phiphi33/block/docs/IMG_20210426_165738.jpg

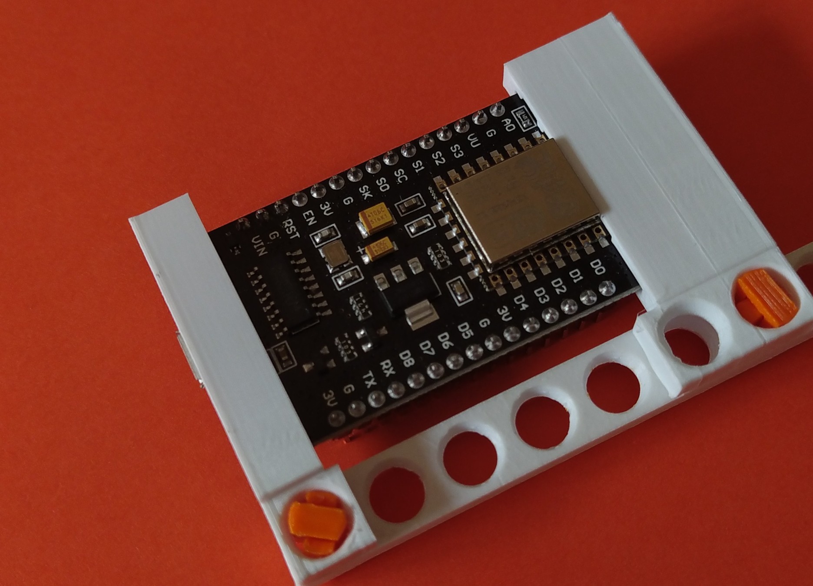
docs/IMG_20210426_165738.jpg
