phiphi33/block/docs/list-elec-csv.png

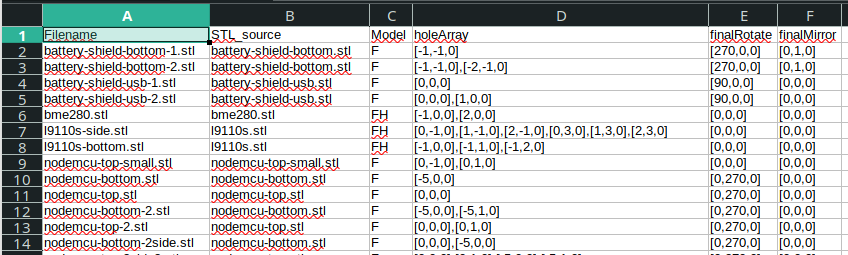
docs/list-elec-csv.png
