phiphi33/block/docs/projects/smartphone-holder.jpg

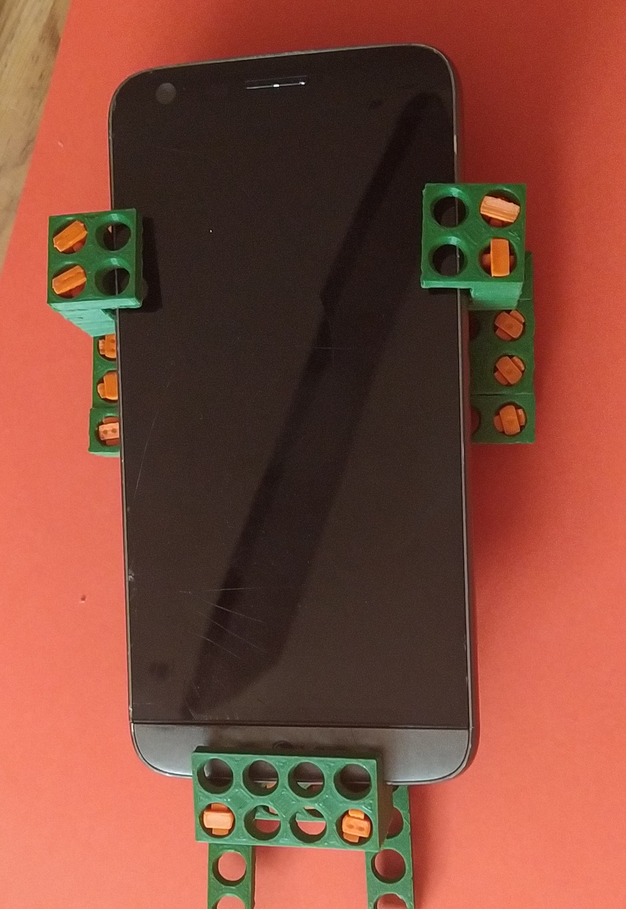
docs/projects/smartphone-holder.jpg
