phiphi33/block/other/12.8/stl/clips/blocker-2.png

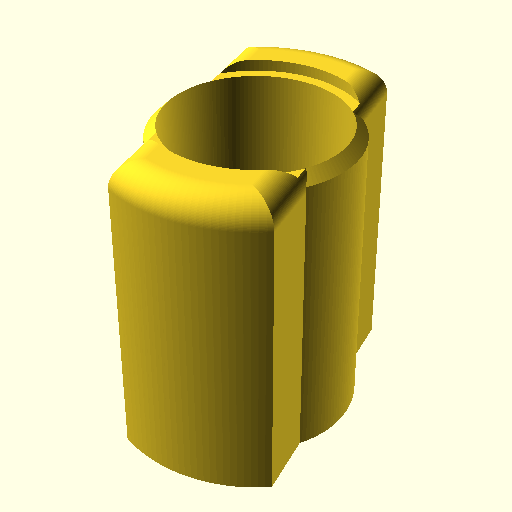
other/12.8/stl/clips/blocker-2.png
