phiphi33/block/other/12.8/stl/clips/clip-2.png

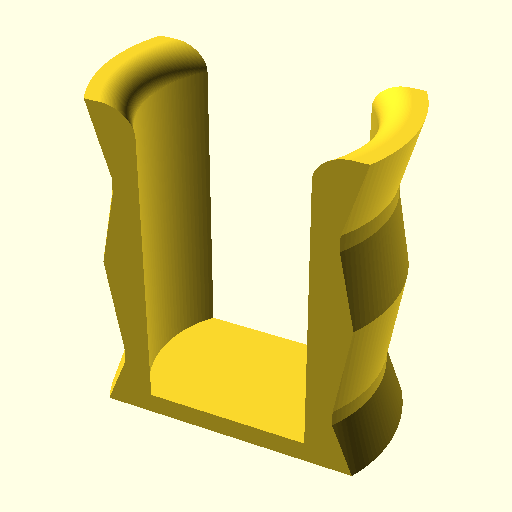
other/12.8/stl/clips/clip-2.png
