phiphi33/block/other/lego/stl/L1.png

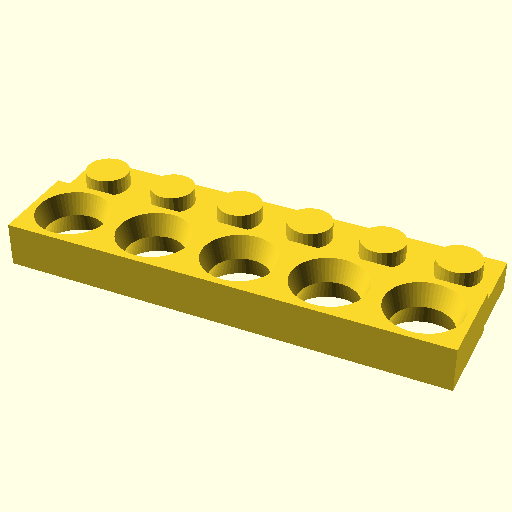
other/lego/stl/L1.png
