phiphi33/block/other/lego/stl/L2.png

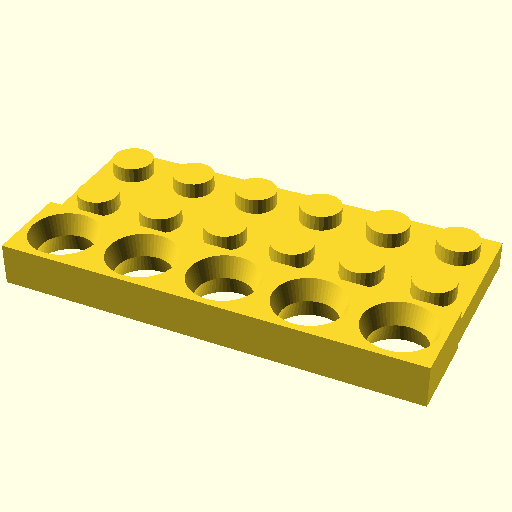
other/lego/stl/L2.png
