phiphi33/block/other/lego/stl/L3.png

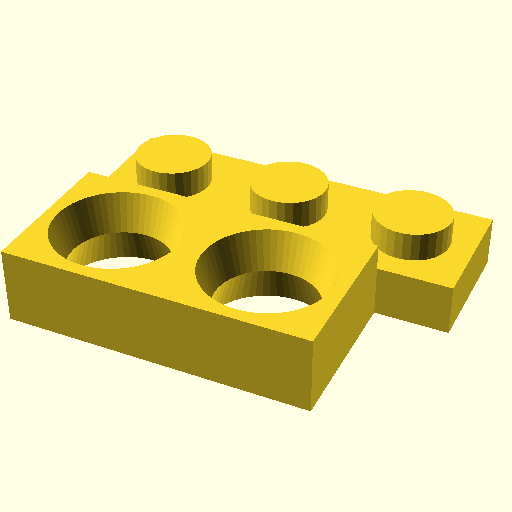
other/lego/stl/L3.png
