phiphi33/block/other/lego/stl/L4.png

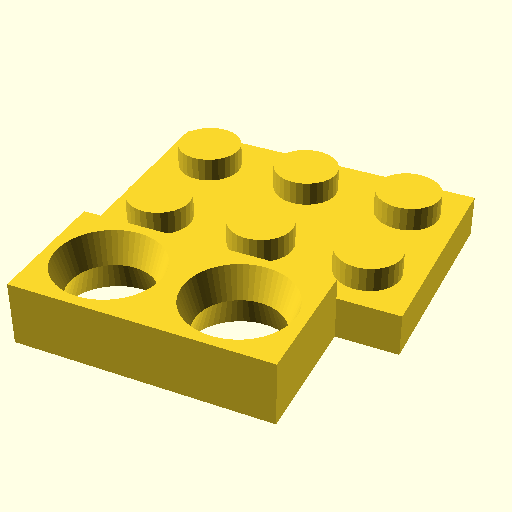
other/lego/stl/L4.png
