phiphi33/block/other/lego/stl/L5.png

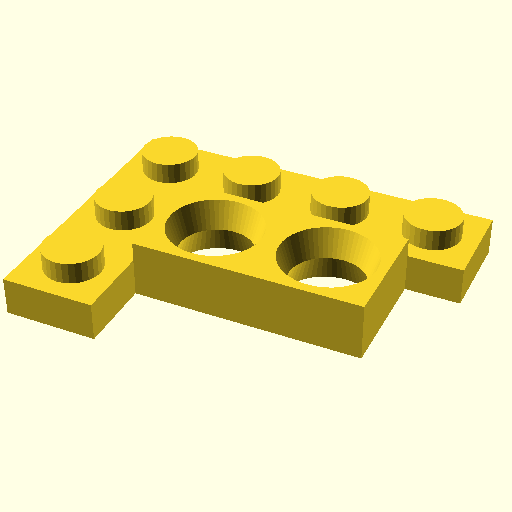
other/lego/stl/L5.png
