phiphi33/block/other/lego/stl/L6.png

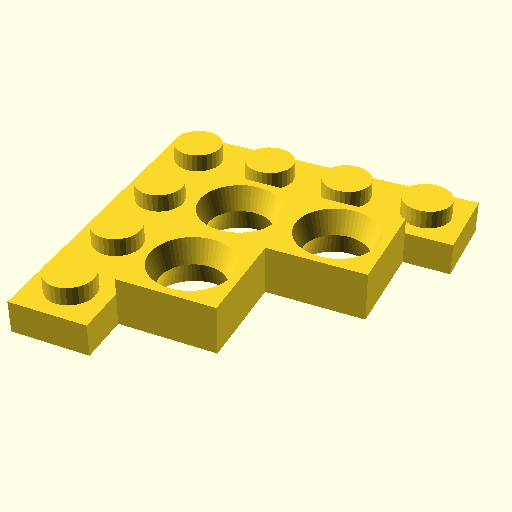
other/lego/stl/L6.png
