phiphi33/block/other/lego/stl/L7.png

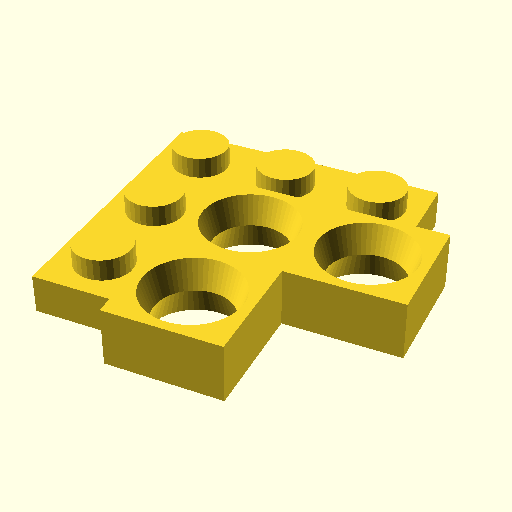
other/lego/stl/L7.png
