phiphi33/block/other/spiralwheel/stl/SP45-hard-clip.png

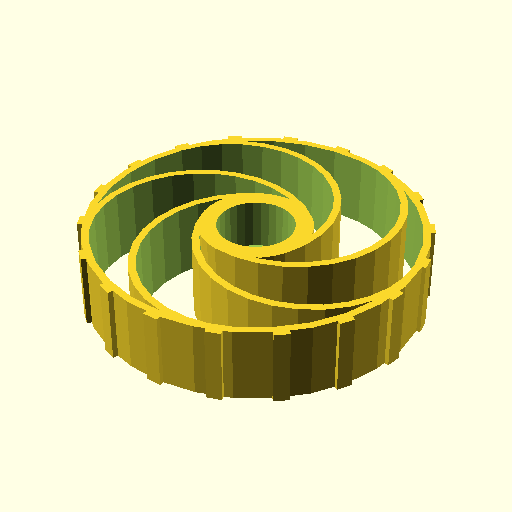
other/spiralwheel/stl/SP45-hard-clip.png
