phiphi33/block/other/spiralwheel/stl/SP45-hard-dc-gearbox.png

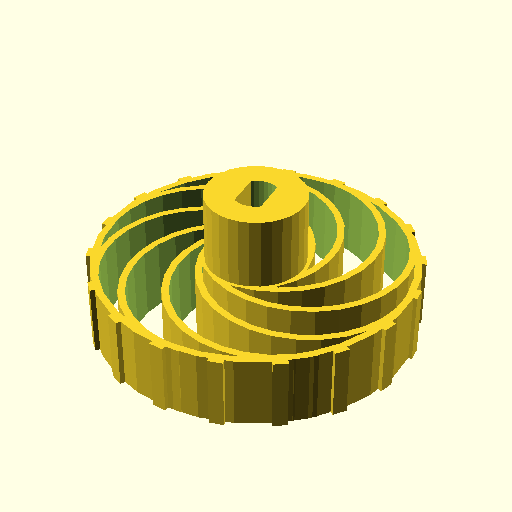
other/spiralwheel/stl/SP45-hard-dc-gearbox.png
