phiphi33/block/other/spiralwheel/stl/SP45-soft-sg90.png

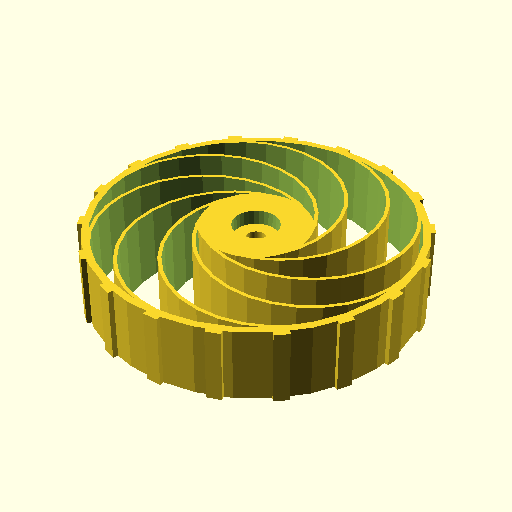
other/spiralwheel/stl/SP45-soft-sg90.png
