phiphi33/block/other/spiralwheel/stl/SP65-soft-clip.png

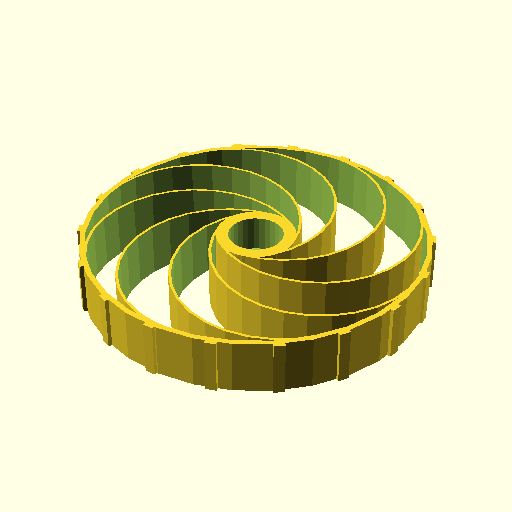
other/spiralwheel/stl/SP65-soft-clip.png
