phiphi33/block/other/spiralwheel/stl/washer.png

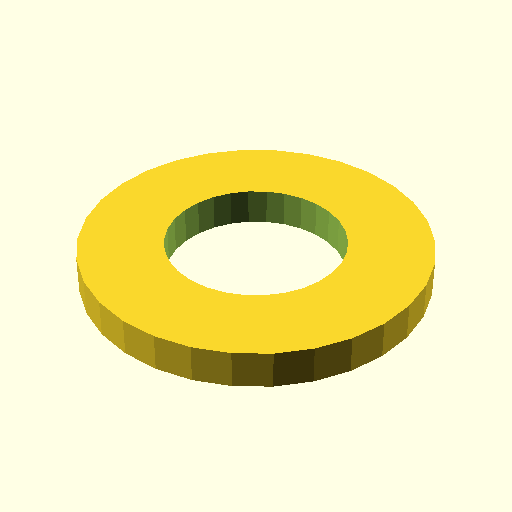
other/spiralwheel/stl/washer.png
