phiphi33/block/stl/clips/blocker-2-easy2.png

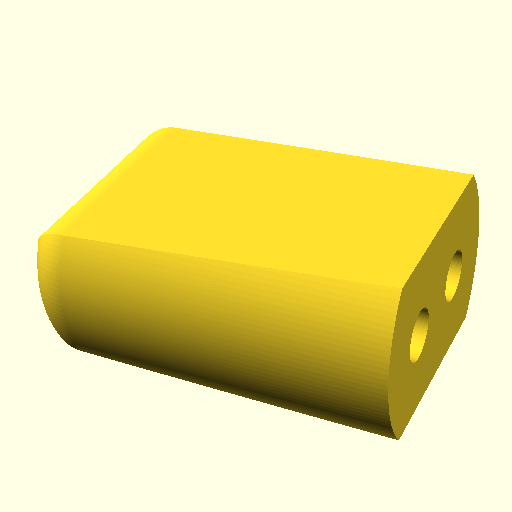
stl/clips/blocker-2-easy2.png
