phiphi33/block/stl/clips/blocker-2-easy.png

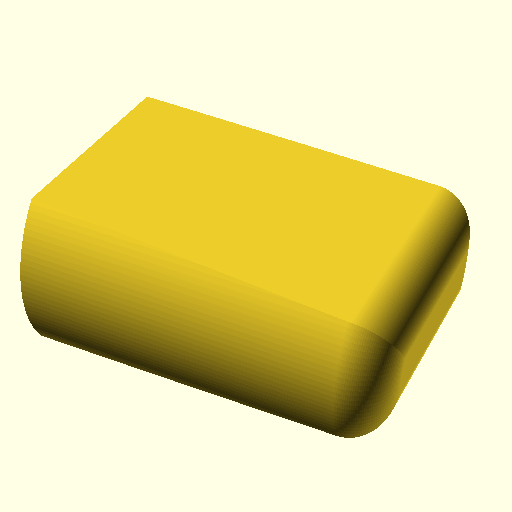
stl/clips/blocker-2-easy.png
