phiphi33/block/stl/clips/blocker-2-strong.png

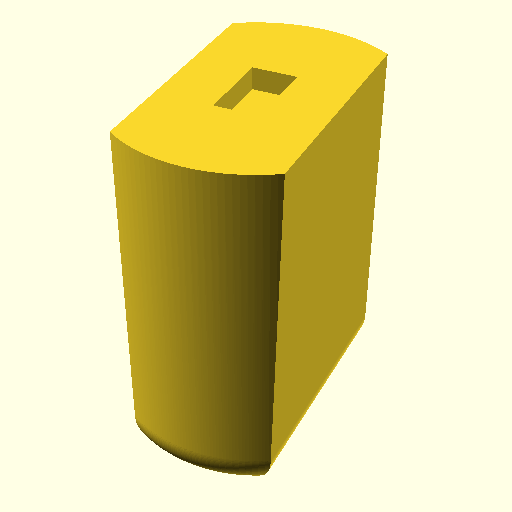
stl/clips/blocker-2-strong.png
