phiphi33/block/stl/clips/blocker-2.png

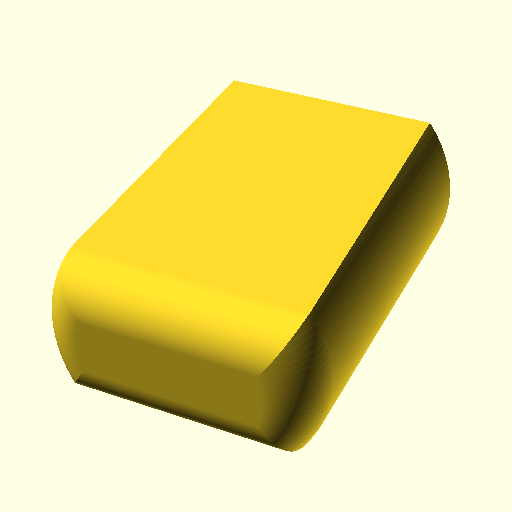
stl/clips/blocker-2.png
