phiphi33/block/stl/clips/blocker-3-easy2.png

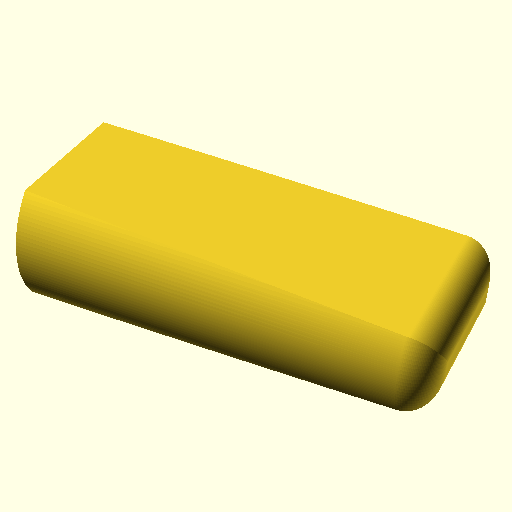
stl/clips/blocker-3-easy2.png
