phiphi33/block/stl/clips/blocker-3-strong.png

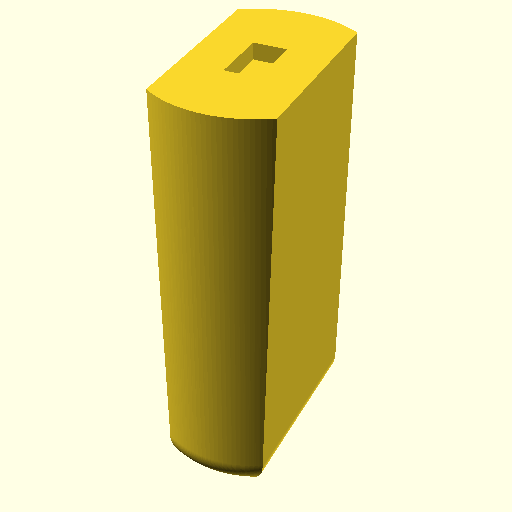
stl/clips/blocker-3-strong.png
