phiphi33/block/stl/clips/blocker-3.png

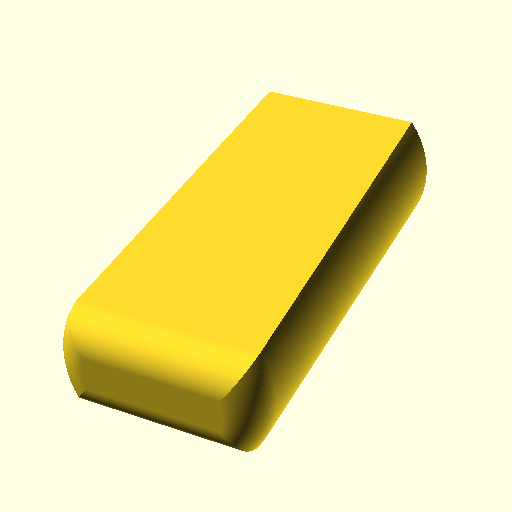
stl/clips/blocker-3.png
