phiphi33/block/stl/clips/blocker-4-easy2.png

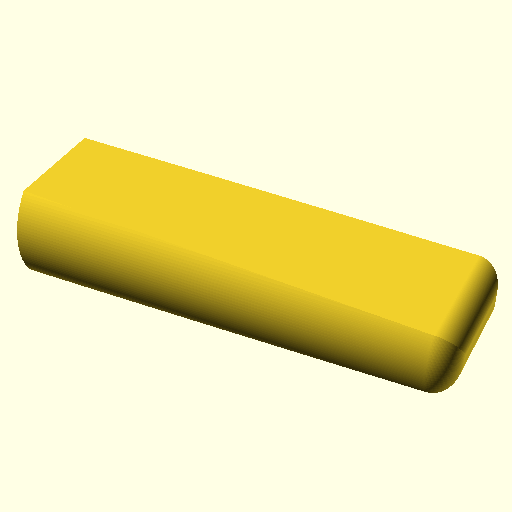
stl/clips/blocker-4-easy2.png
