phiphi33/block/stl/clips/blocker-4-strong.png

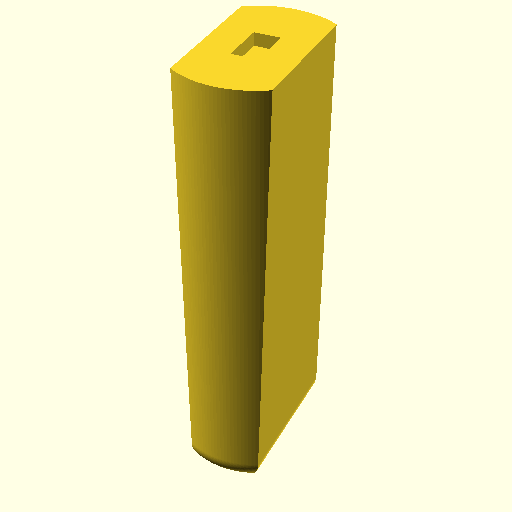
stl/clips/blocker-4-strong.png
