phiphi33/block/stl/clips/blocker-4.png

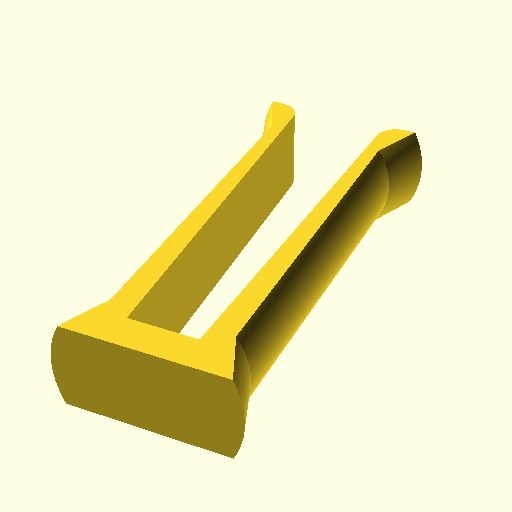
stl/clips/blocker-4.png
