phiphi33/block/stl/clips/blocker-5.png

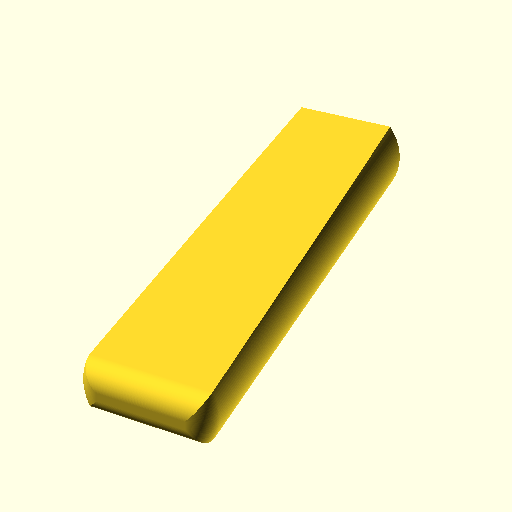
stl/clips/blocker-5.png
