phiphi33/block/stl/clips/clip-2-M4.png

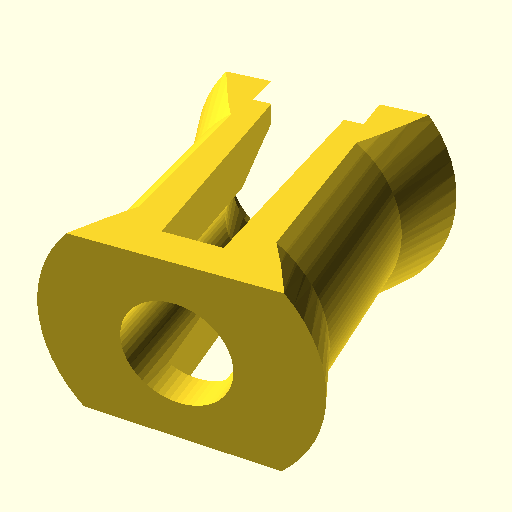
stl/clips/clip-2-M4.png
