phiphi33/block/stl/clips/clip-2.png

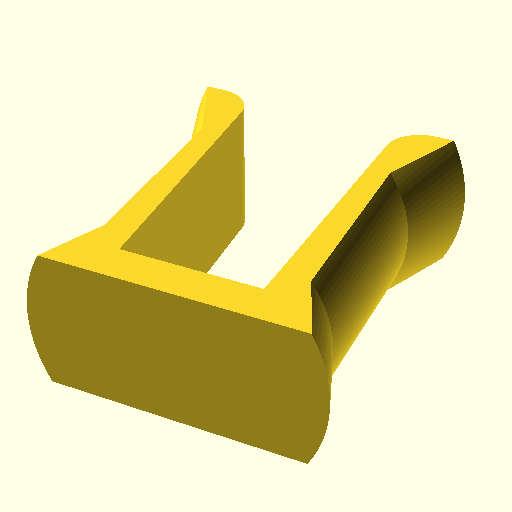
stl/clips/clip-2.png
