phiphi33/block/stl/clips/clip-3-M4.png

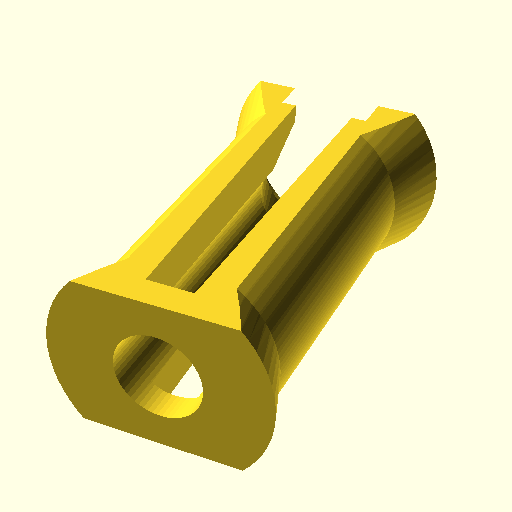
stl/clips/clip-3-M4.png
