phiphi33/block/stl/clips/clip-3.png

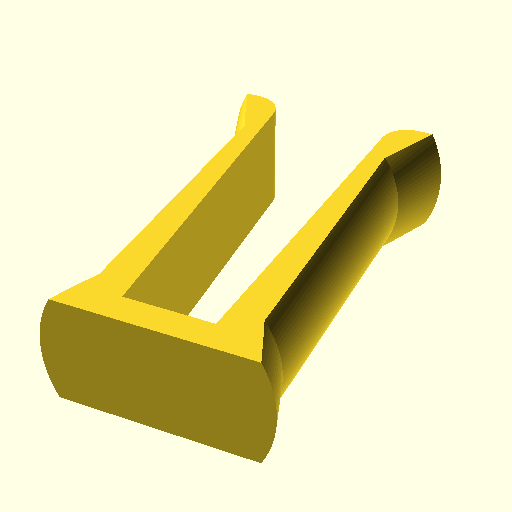
stl/clips/clip-3.png
