phiphi33/block/stl/clips/clip-3a.png

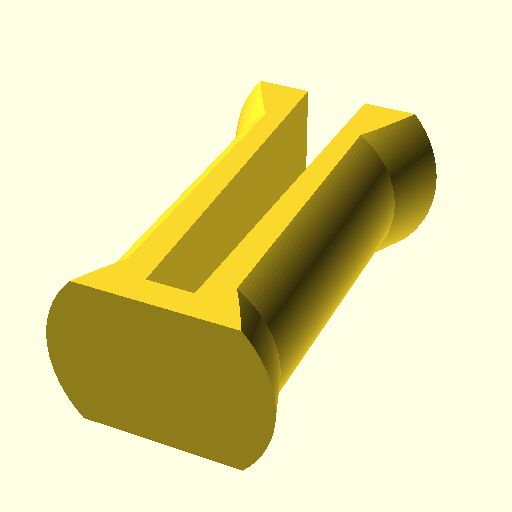
stl/clips/clip-3a.png
