phiphi33/block/stl/clips/clip-4-M4.png

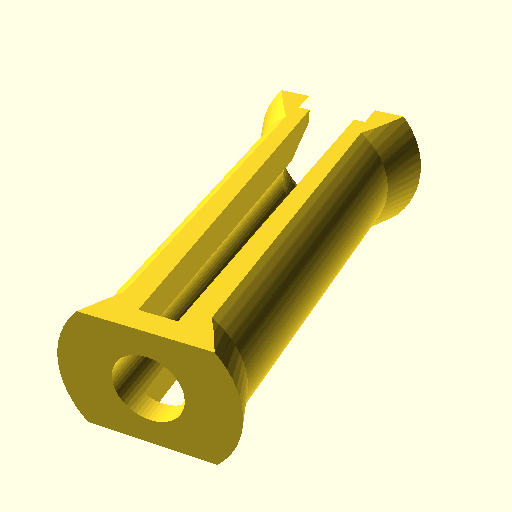
stl/clips/clip-4-M4.png
