phiphi33/block/stl/clips/clip-5.png

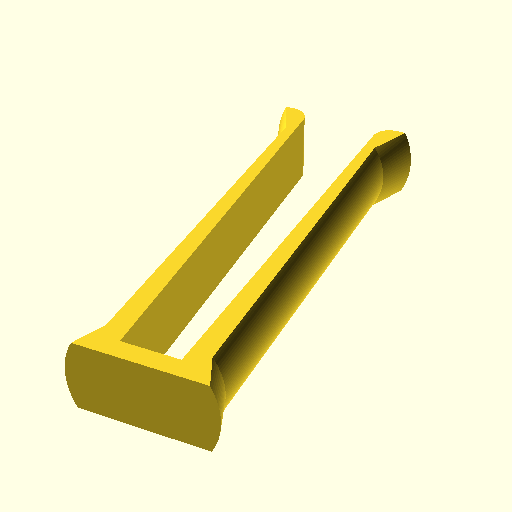
stl/clips/clip-5.png
