phiphi33/block/stl/clips/clip-6.png

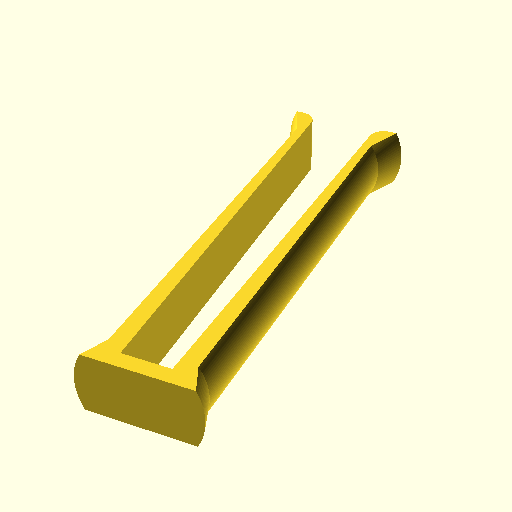
stl/clips/clip-6.png
