phiphi33/block/other/12.8/stl/basic-parts/C-2-1-1.png

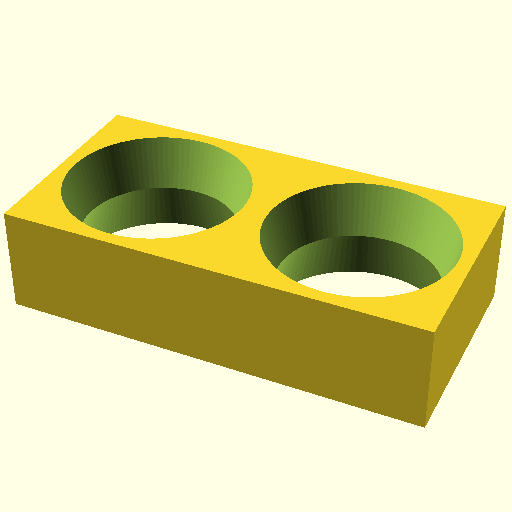
other/12.8/stl/basic-parts/C-2-1-1.png
