phiphi33/block/stl/basic-parts/C-2-2-1.png

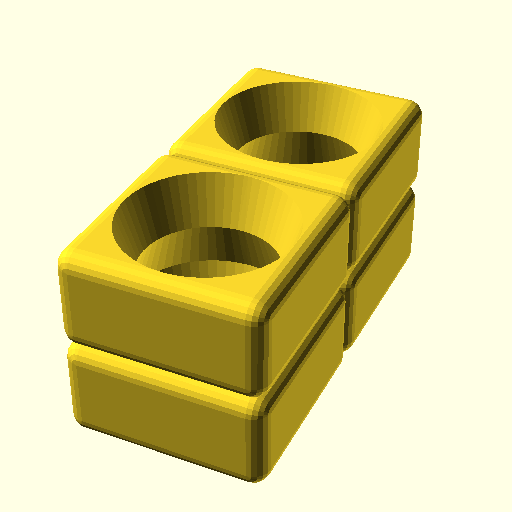
stl/basic-parts/C-2-2-1.png
