phiphi33/block/stl/basic-parts/C-2-2-2.png

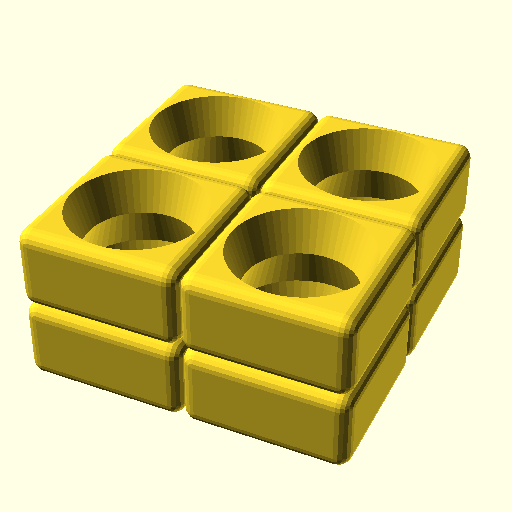
stl/basic-parts/C-2-2-2.png
