phiphi33/block/stl/basic-parts/C-3-1-1.png

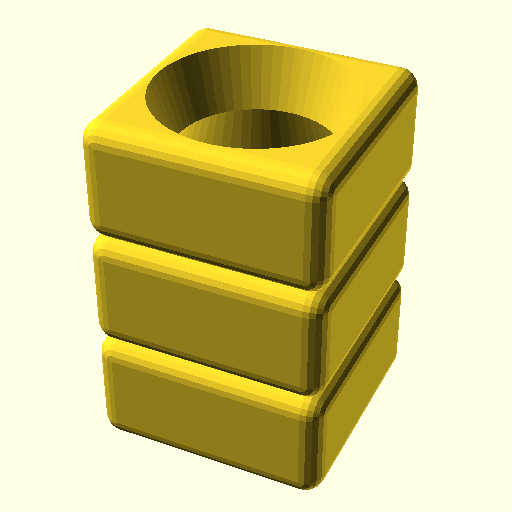
stl/basic-parts/C-3-1-1.png
