phiphi33/block/stl/basic-parts/I-1.png

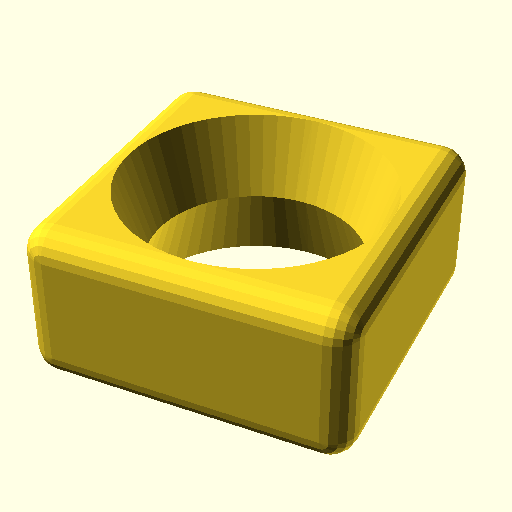
stl/basic-parts/I-1.png
