phiphi33/block/stl/basic-parts/I-2.png

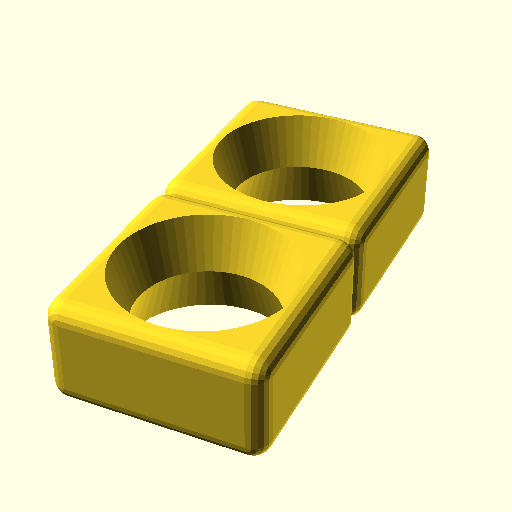
stl/basic-parts/I-2.png
