phiphi33/block/stl/basic-parts/I-3.png

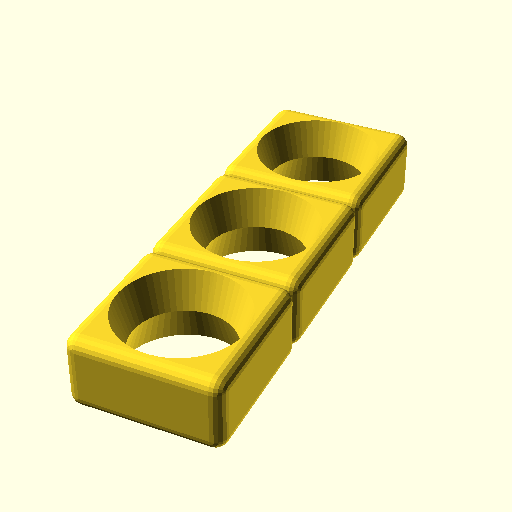
stl/basic-parts/I-3.png
