phiphi33/block/stl/basic-parts/I-4.png

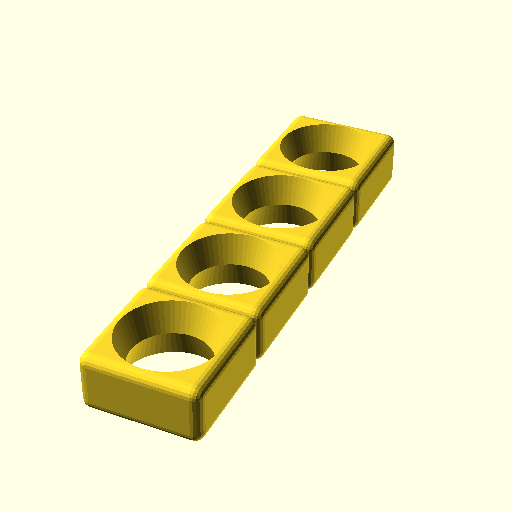
stl/basic-parts/I-4.png
