phiphi33/block/stl/basic-parts/I-7.png

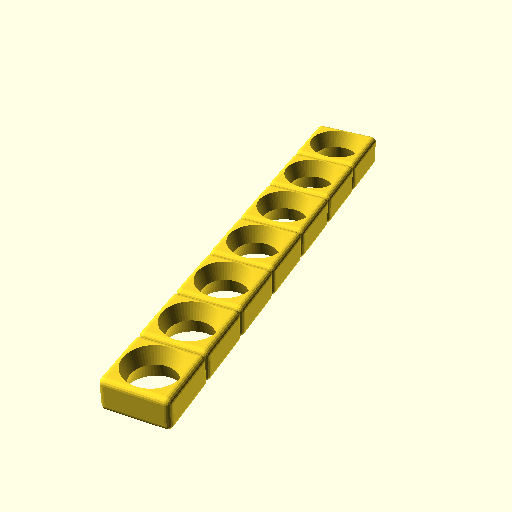
stl/basic-parts/I-7.png
