phiphi33/block/stl/basic-parts/IHR-2.png

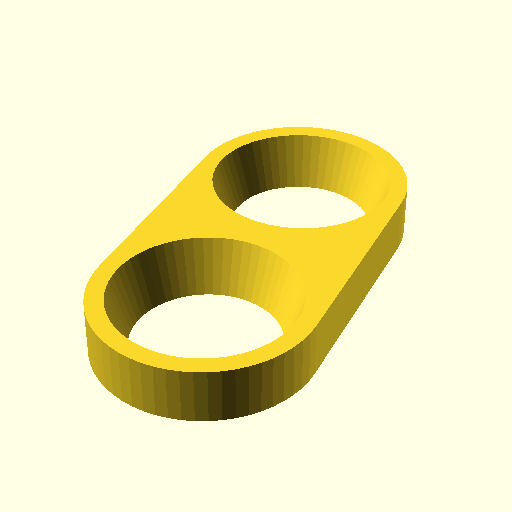
stl/basic-parts/IHR-2.png
