phiphi33/block/stl/basic-parts/IR-1.png

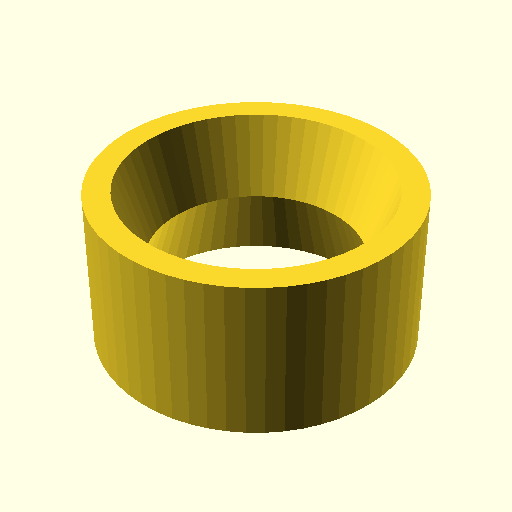
stl/basic-parts/IR-1.png
