phiphi33/block/stl/basic-parts/IR-2.png

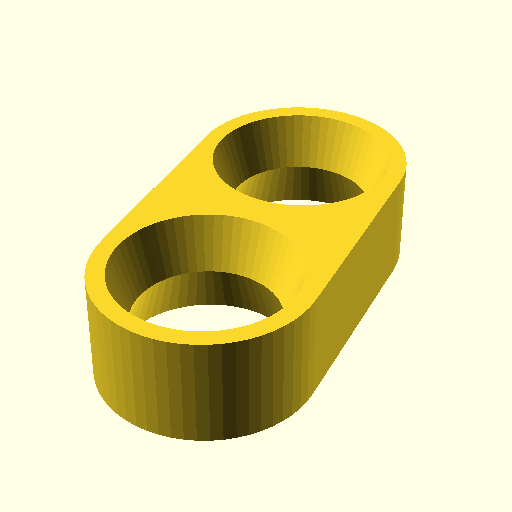
stl/basic-parts/IR-2.png
