phiphi33/block/stl/basic-parts/IR-3.png

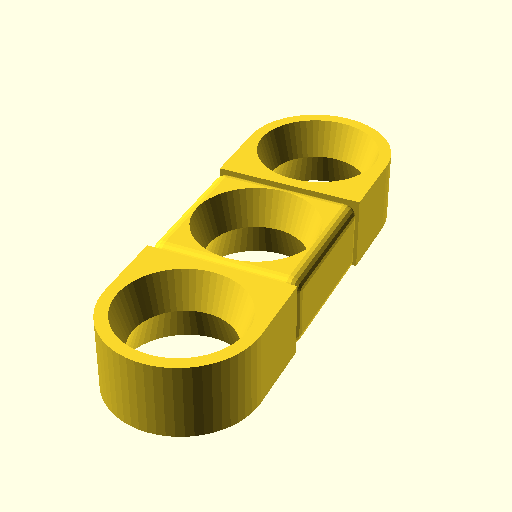
stl/basic-parts/IR-3.png
