phiphi33/block/stl/basic-parts/L-1-1-3.png

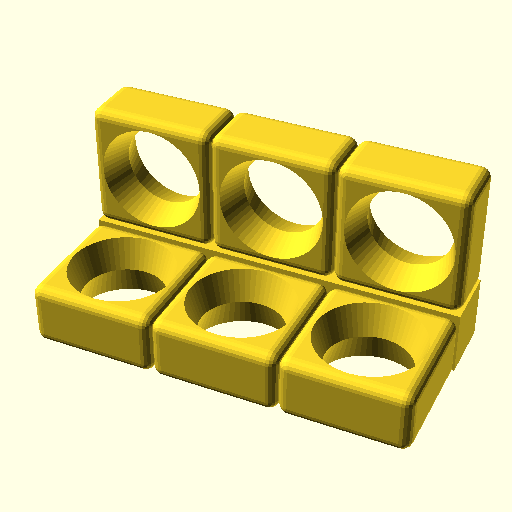
stl/basic-parts/L-1-1-3.png
