phiphi33/block/stl/basic-parts/L-1-1-4.png

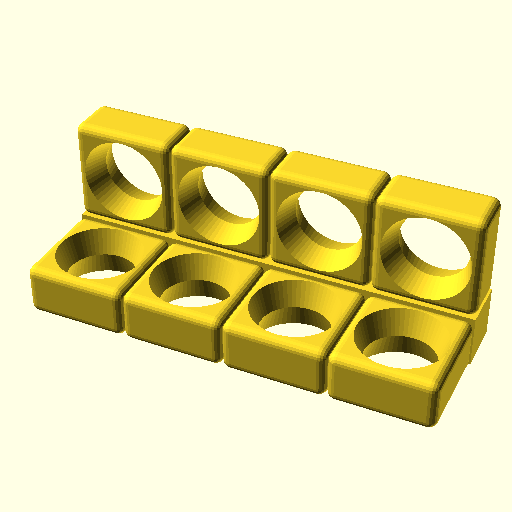
stl/basic-parts/L-1-1-4.png
