phiphi33/block/stl/basic-parts/L-1-1-8.png

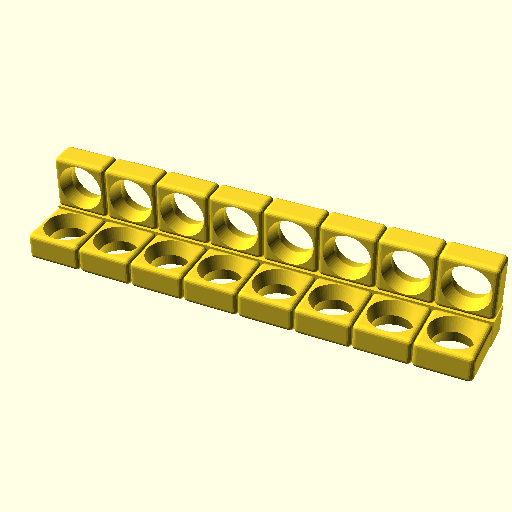
stl/basic-parts/L-1-1-8.png
