phiphi33/block/stl/basic-parts/L-2-1-2.png

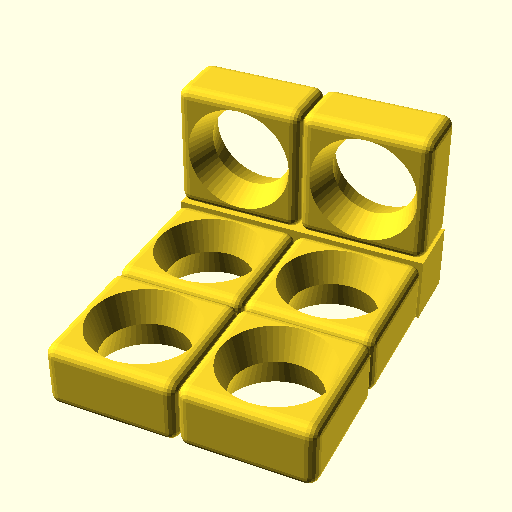
stl/basic-parts/L-2-1-2.png
