phiphi33/block/stl/basic-parts/L-2-1-5.png

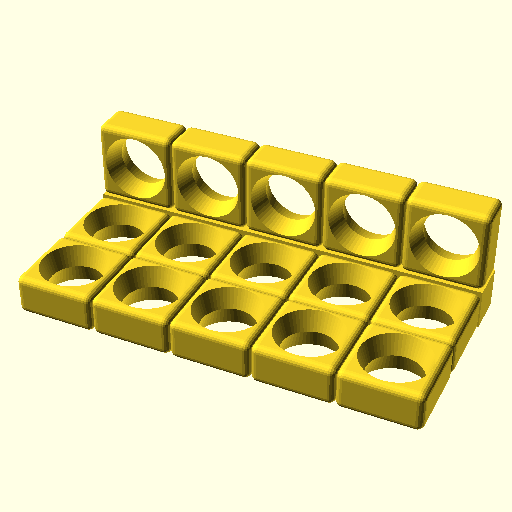
stl/basic-parts/L-2-1-5.png
