phiphi33/block/stl/basic-parts/L-2-2-1.png

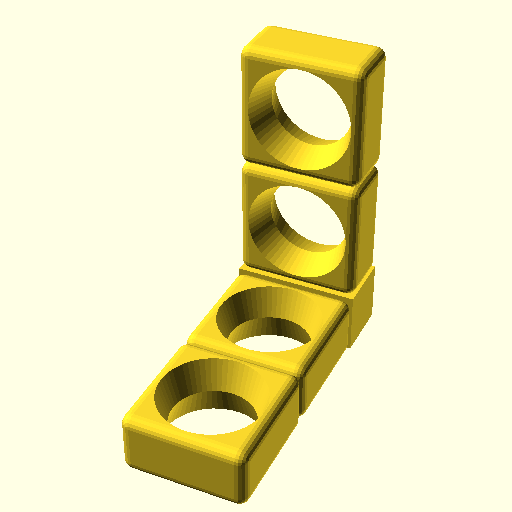
stl/basic-parts/L-2-2-1.png
