phiphi33/block/stl/basic-parts/L-2-2-3.png

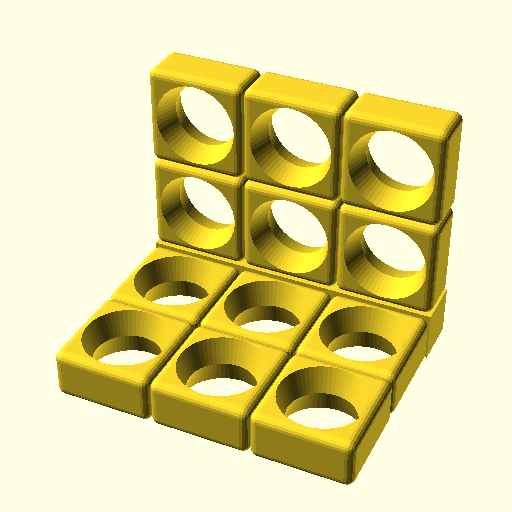
stl/basic-parts/L-2-2-3.png
