phiphi33/block/stl/basic-parts/L-3-1-1.png

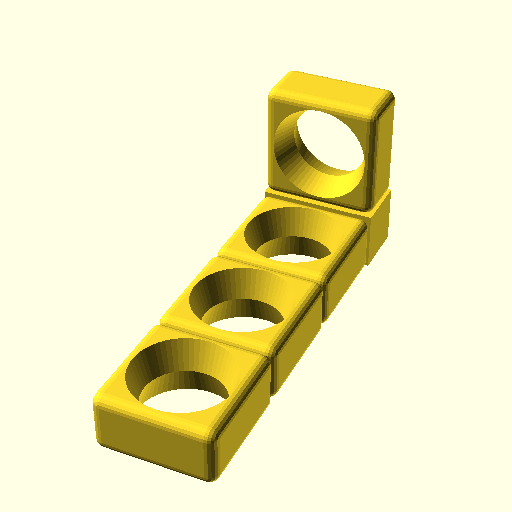
stl/basic-parts/L-3-1-1.png
