phiphi33/block/stl/basic-parts/L-3-3-3.png

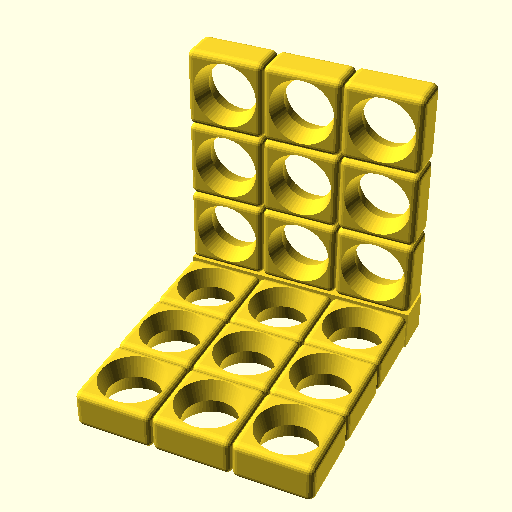
stl/basic-parts/L-3-3-3.png
