phiphi33/block/stl/basic-parts/L-4-1-1.png

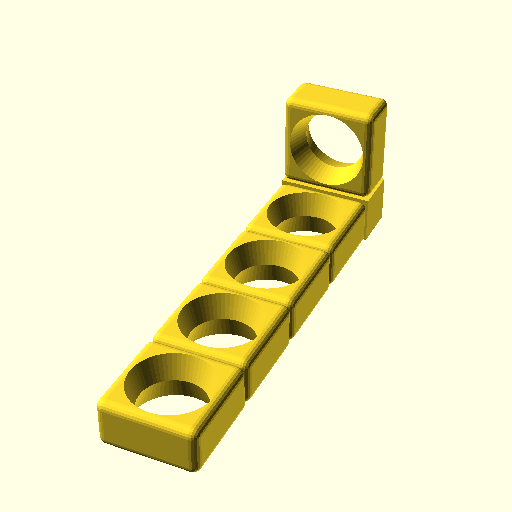
stl/basic-parts/L-4-1-1.png
