phiphi33/block/stl/basic-parts/L-6-1-1.png

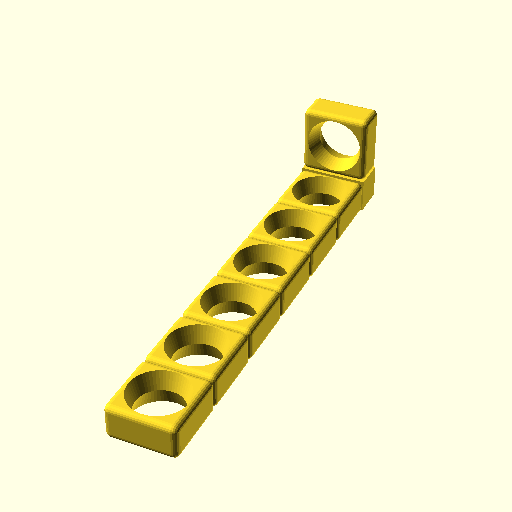
stl/basic-parts/L-6-1-1.png
