phiphi33/block/stl/basic-parts/LF-2-2.png

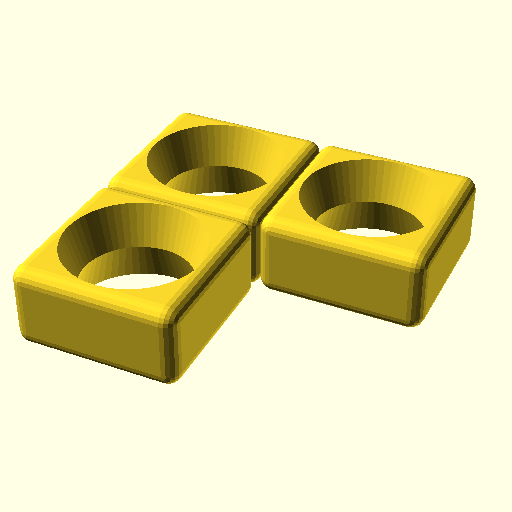
stl/basic-parts/LF-2-2.png
