phiphi33/block/stl/basic-parts/LF-3-2.png

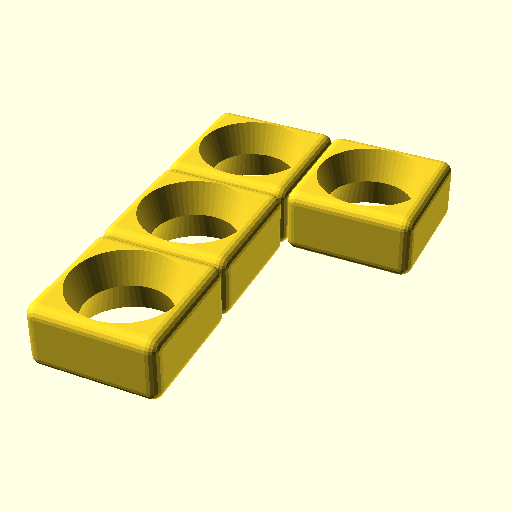
stl/basic-parts/LF-3-2.png
