phiphi33/block/stl/basic-parts/LF-3-3.png

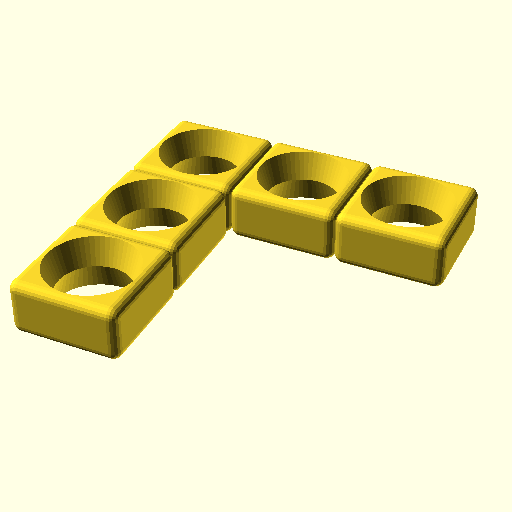
stl/basic-parts/LF-3-3.png
