phiphi33/block/stl/basic-parts/LF-4-2.png

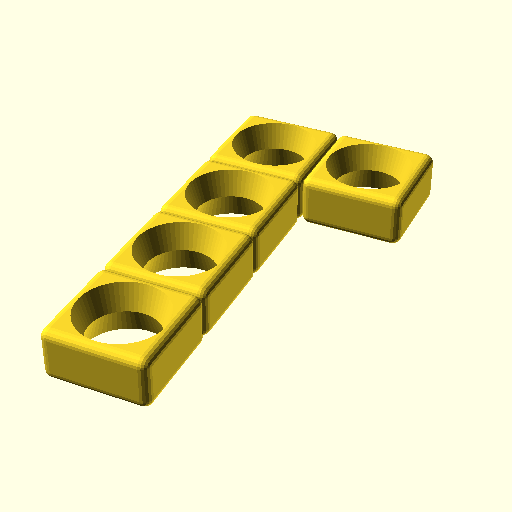
stl/basic-parts/LF-4-2.png
