phiphi33/block/stl/basic-parts/LF-4-3.png

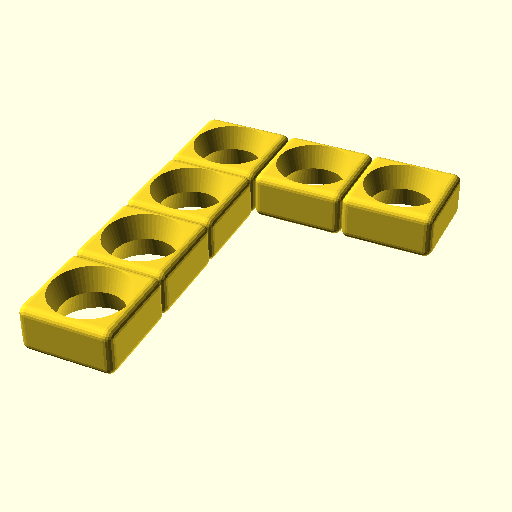
stl/basic-parts/LF-4-3.png
