phiphi33/block/stl/basic-parts/LF-4-4.png

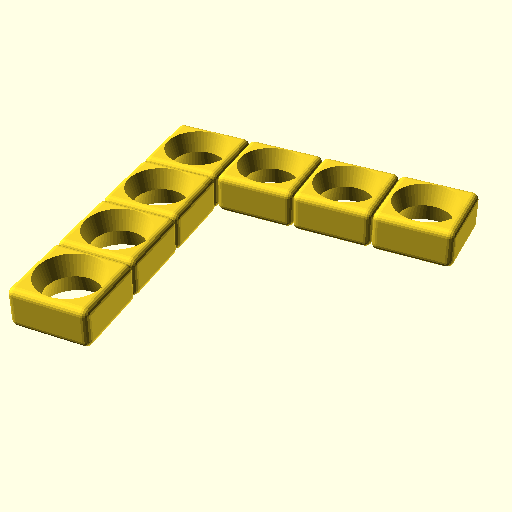
stl/basic-parts/LF-4-4.png
