phiphi33/block/stl/basic-parts/LF-6-2.png

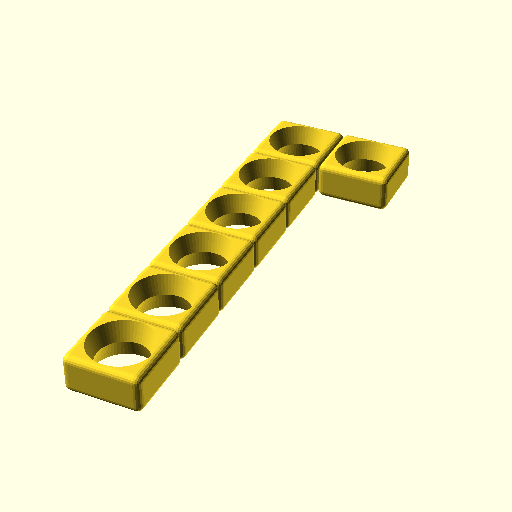
stl/basic-parts/LF-6-2.png
