phiphi33/block/stl/basic-parts/LF-6-3.png

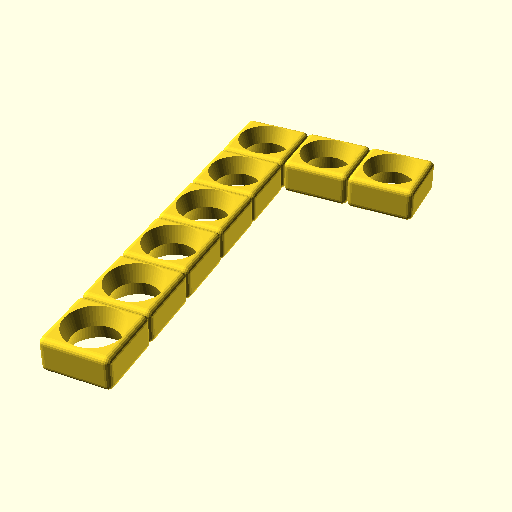
stl/basic-parts/LF-6-3.png
