phiphi33/block/stl/basic-parts/P-2-2.png

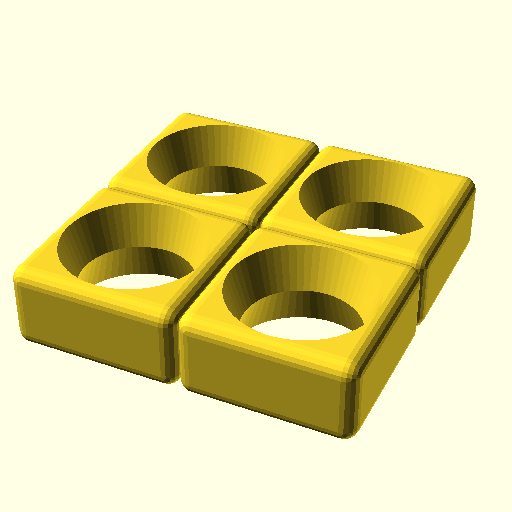
stl/basic-parts/P-2-2.png
