phiphi33/block/stl/basic-parts/P-3-2.png

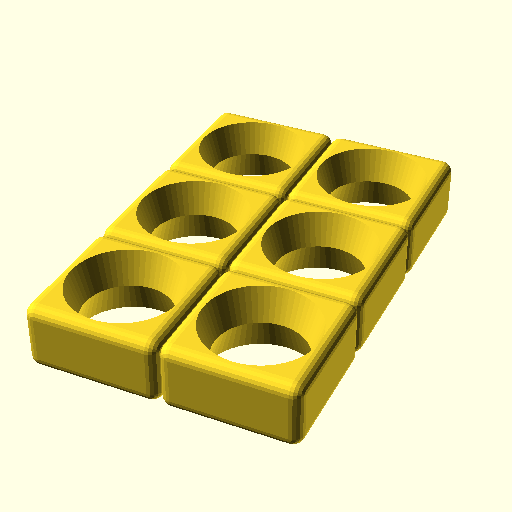
stl/basic-parts/P-3-2.png
