phiphi33/block/stl/basic-parts/P-3-3.png

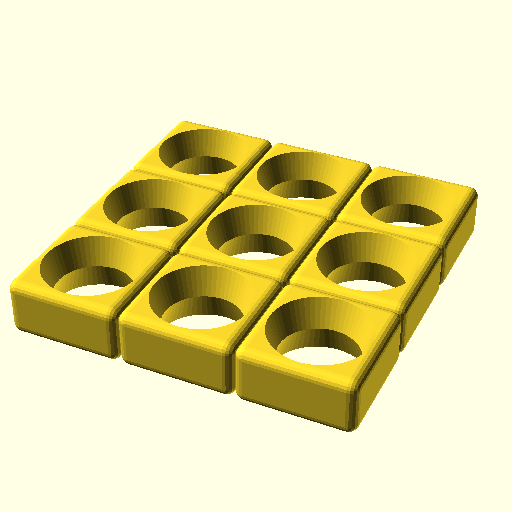
stl/basic-parts/P-3-3.png
