phiphi33/block/stl/basic-parts/P-4-2.png

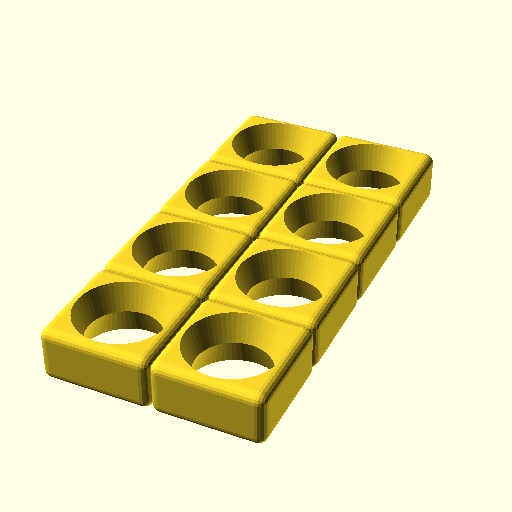
stl/basic-parts/P-4-2.png
