phiphi33/block/stl/basic-parts/P-4-4.png

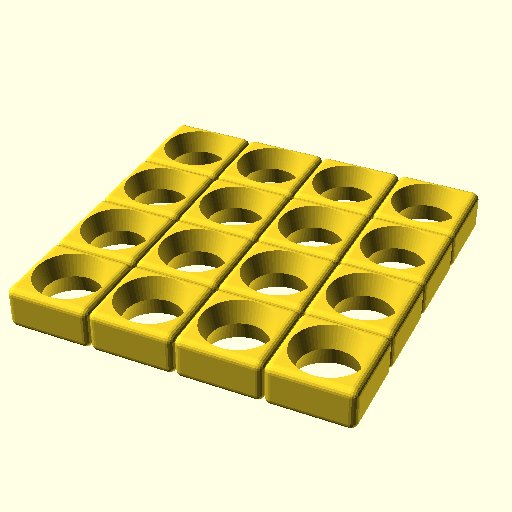
stl/basic-parts/P-4-4.png
