phiphi33/block/stl/basic-parts/P-5-2.png

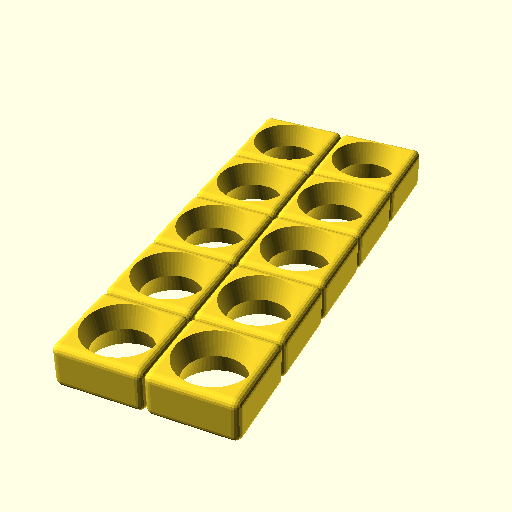
stl/basic-parts/P-5-2.png
