phiphi33/block/stl/basic-parts/P-5-4.png

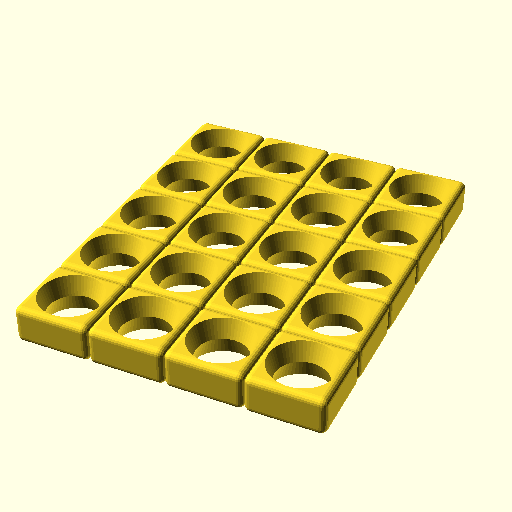
stl/basic-parts/P-5-4.png
