phiphi33/block/stl/basic-parts/P-6-2.png

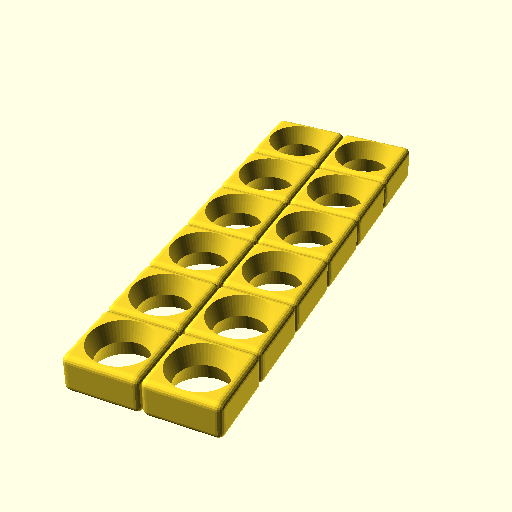
stl/basic-parts/P-6-2.png
