phiphi33/block/stl/basic-parts/S-1-1-1.png

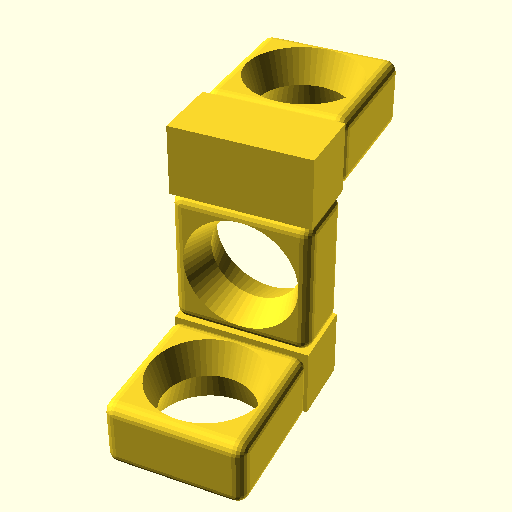
stl/basic-parts/S-1-1-1.png
