phiphi33/block/stl/basic-parts/S-2-1-2.png

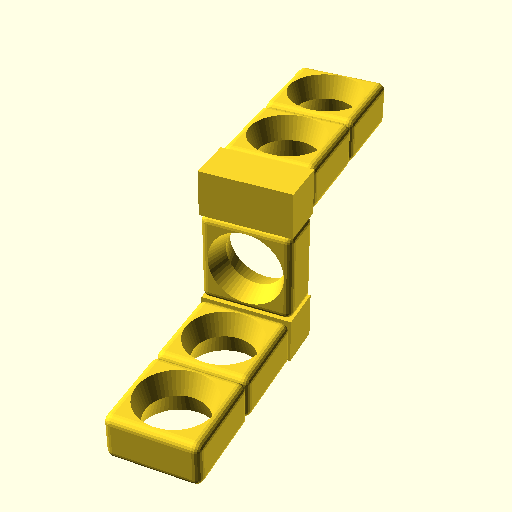
stl/basic-parts/S-2-1-2.png
