phiphi33/block/stl/basic-parts/U-1-2-1.png

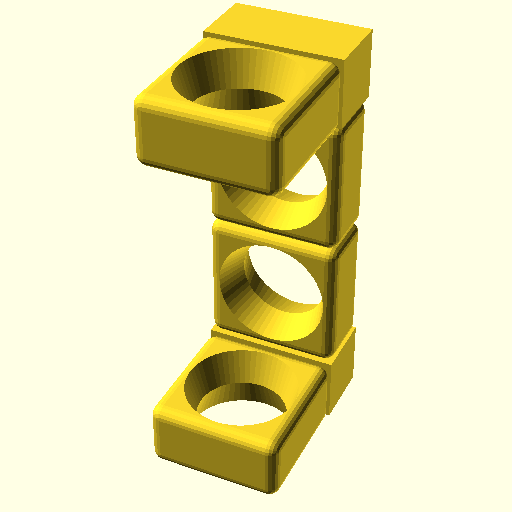
stl/basic-parts/U-1-2-1.png
