phiphi33/block/stl/basic-parts/U-2-2-2.png

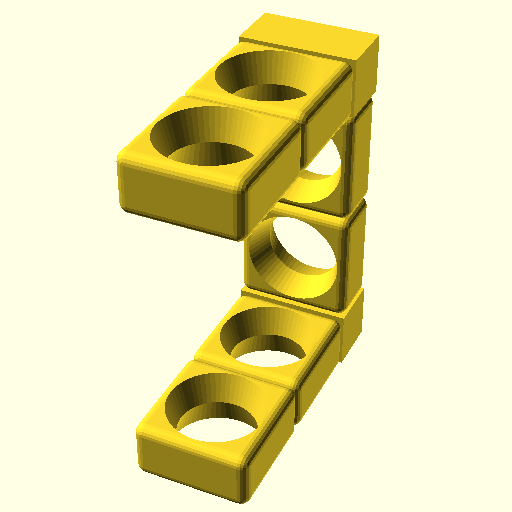
stl/basic-parts/U-2-2-2.png
