phiphi33/block/stl/basic-parts/U-3-3-3.png

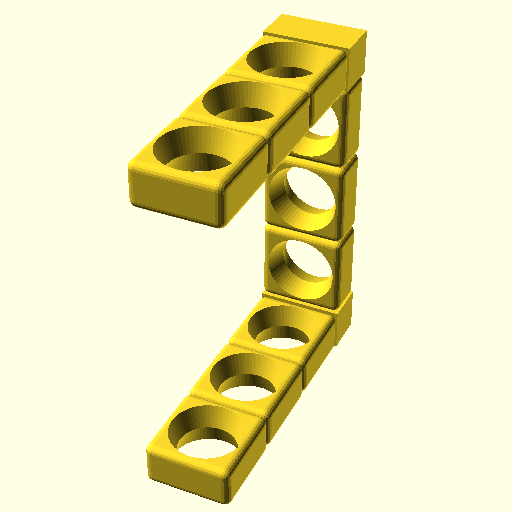
stl/basic-parts/U-3-3-3.png
