phiphi33/block/stl/electronic-parts/18650x2/18650x2-holder-bottom.png

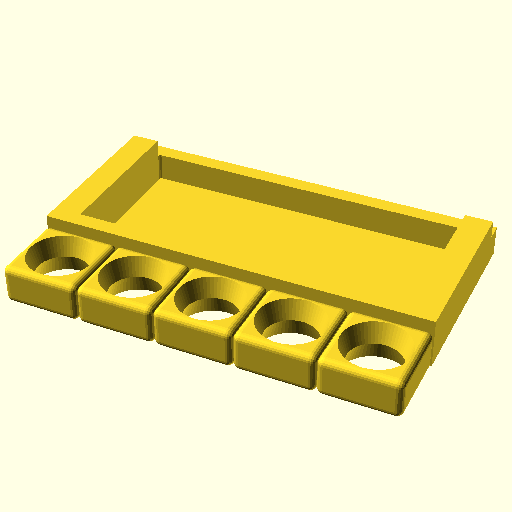
stl/electronic-parts/18650x2/18650x2-holder-bottom.png
