phiphi33/block/stl/electronic-parts/arduino-nano/nano-bottom-2side.png

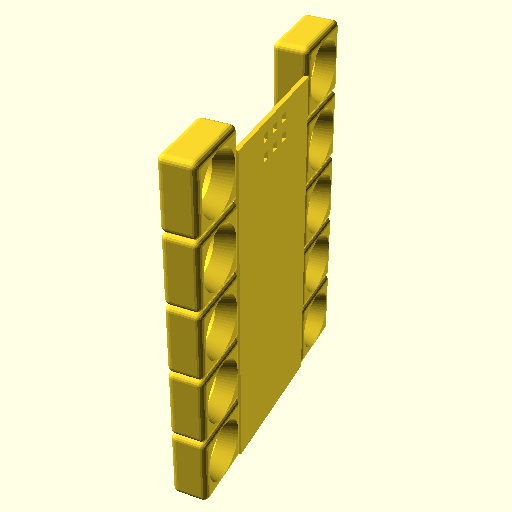
stl/electronic-parts/arduino-nano/nano-bottom-2side.png
