phiphi33/block/stl/electronic-parts/battery-shield/battery-shield-bottom-1.png

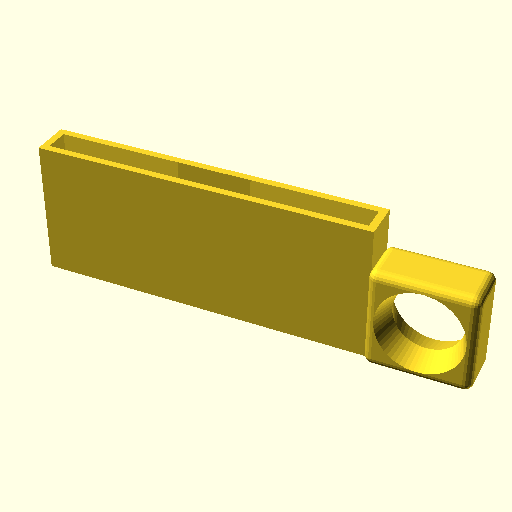
stl/electronic-parts/battery-shield/battery-shield-bottom-1.png
