phiphi33/block/stl/electronic-parts/battery-shield/battery-shield-usb-1.png

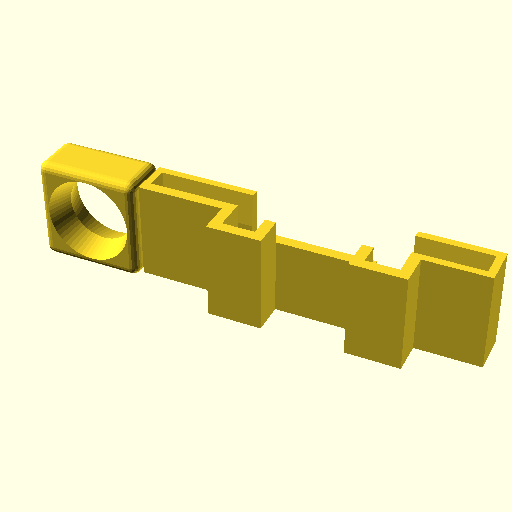
stl/electronic-parts/battery-shield/battery-shield-usb-1.png
