phiphi33/block/stl/electronic-parts/battery-shield/battery-shield-usb-2.png

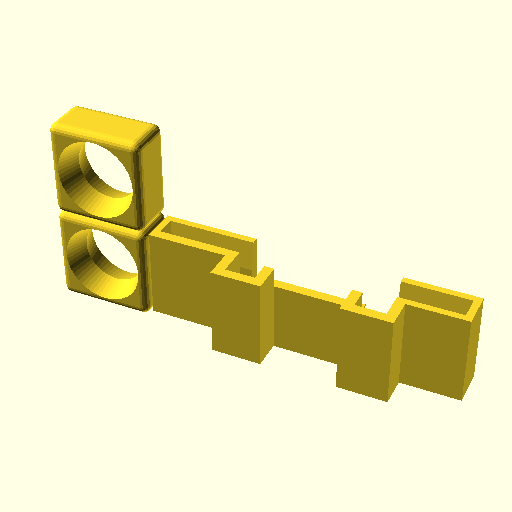
stl/electronic-parts/battery-shield/battery-shield-usb-2.png
