phiphi33/block/stl/electronic-parts/bme280/bme280.png

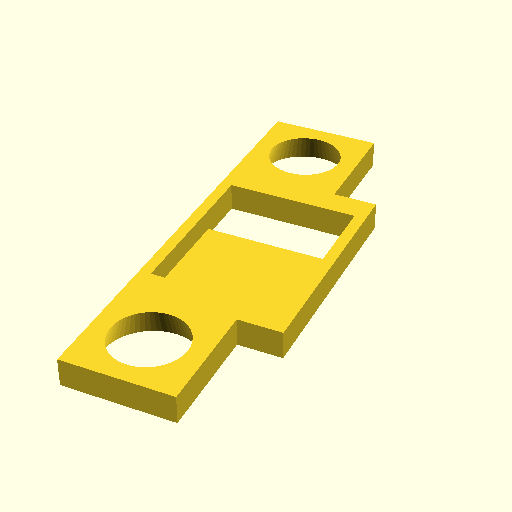
stl/electronic-parts/bme280/bme280.png
