phiphi33/block/stl/electronic-parts/breadboard/breadboard25-2.png

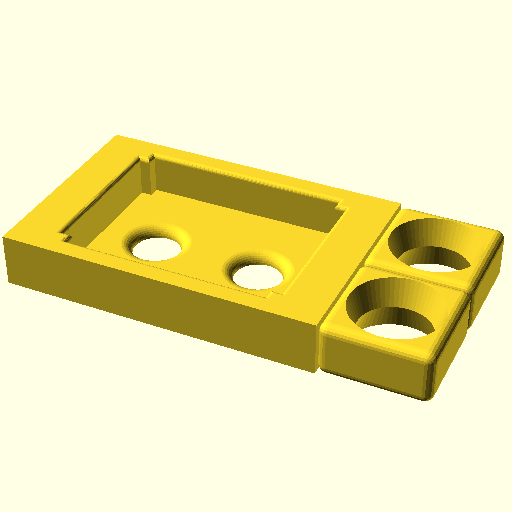
stl/electronic-parts/breadboard/breadboard25-2.png
