phiphi33/block/stl/electronic-parts/breadboard/breadboard25-3.png

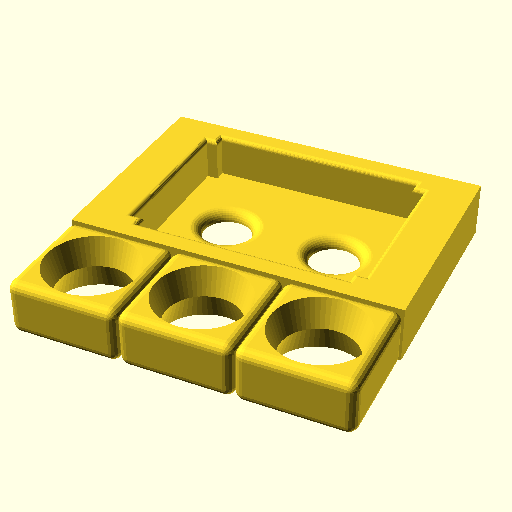
stl/electronic-parts/breadboard/breadboard25-3.png
