phiphi33/block/stl/electronic-parts/button14x20/button14x20-bottom-1side.png

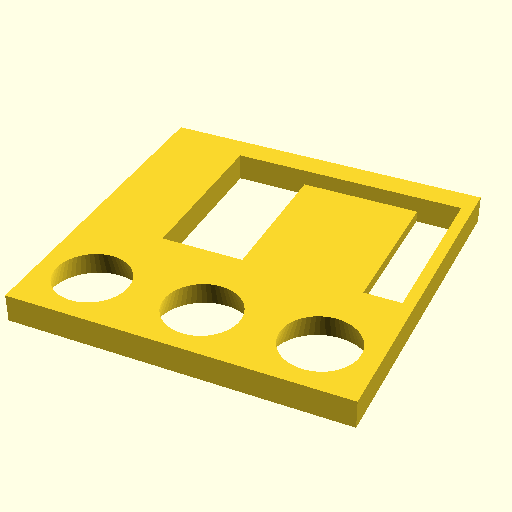
stl/electronic-parts/button14x20/button14x20-bottom-1side.png
