phiphi33/block/stl/electronic-parts/button14x20/button14x20-half-bottomx2-2side.png

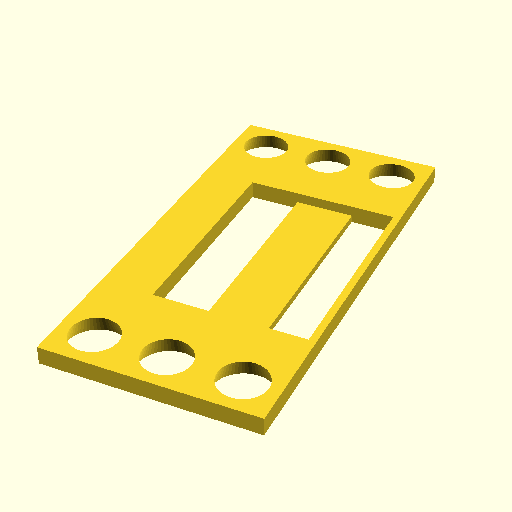
stl/electronic-parts/button14x20/button14x20-half-bottomx2-2side.png
