phiphi33/block/stl/electronic-parts/button14x20/button14x20-half-topx2-1side.png

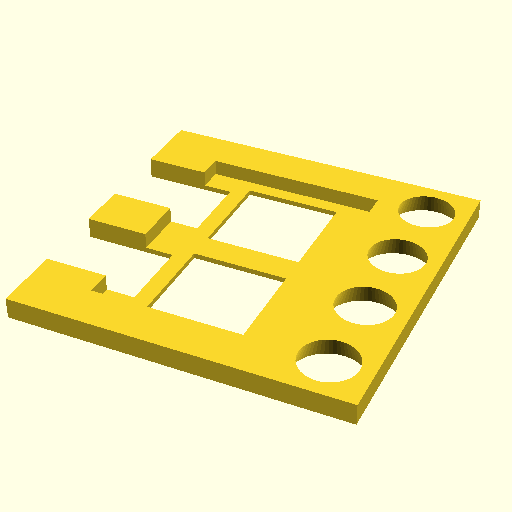
stl/electronic-parts/button14x20/button14x20-half-topx2-1side.png
