phiphi33/block/stl/electronic-parts/button14x20/button14x20-top-1side.png

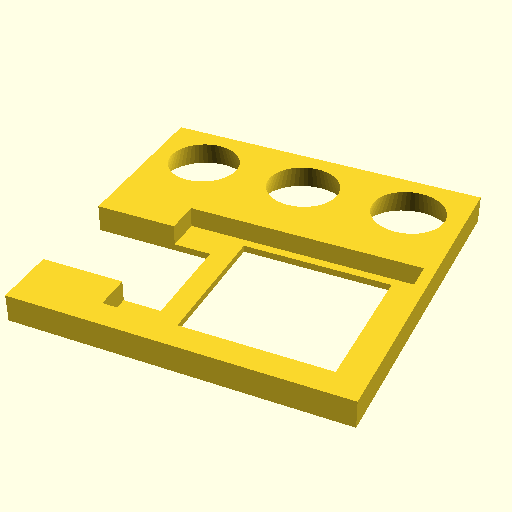
stl/electronic-parts/button14x20/button14x20-top-1side.png
