phiphi33/block/stl/electronic-parts/button14x20/button14x20-top-small.png

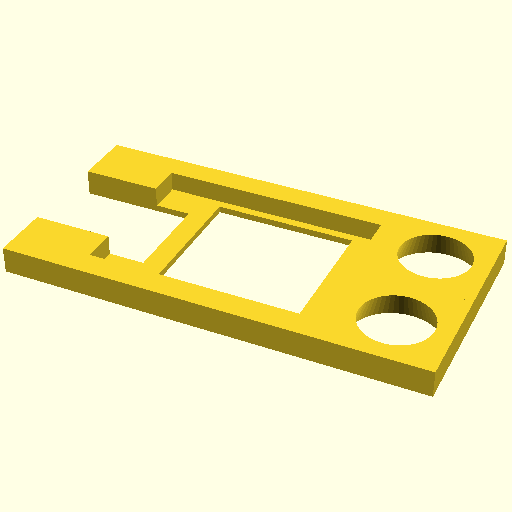
stl/electronic-parts/button14x20/button14x20-top-small.png
