phiphi33/block/stl/electronic-parts/D1-mini/D1-mini-small.png

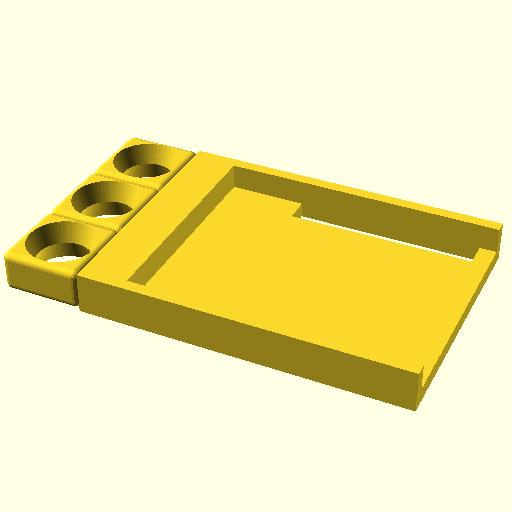
stl/electronic-parts/D1-mini/D1-mini-small.png
