phiphi33/block/stl/electronic-parts/D1-mini/D1-mini.png

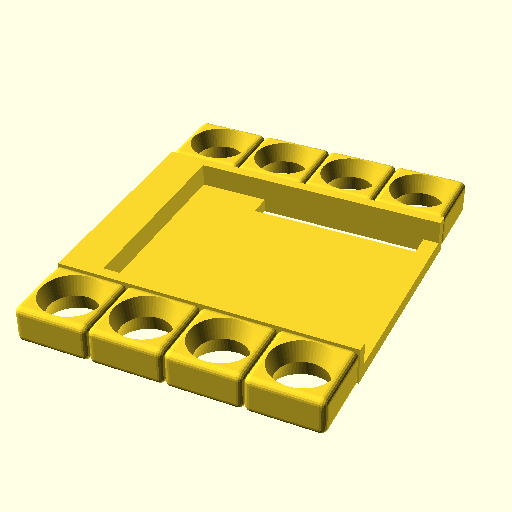
stl/electronic-parts/D1-mini/D1-mini.png
