phiphi33/block/stl/electronic-parts/dc-motor-gear/dc-motor-v2-double.png

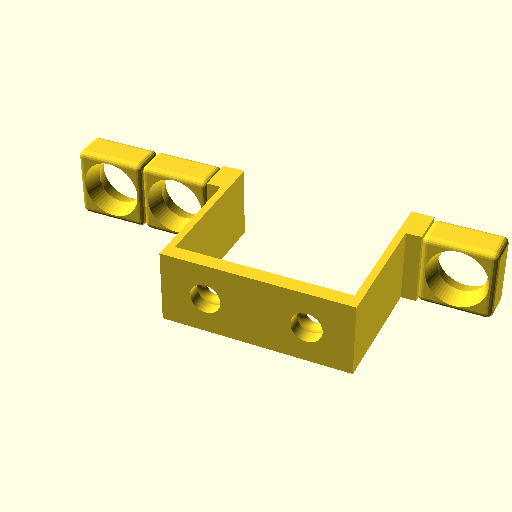
stl/electronic-parts/dc-motor-gear/dc-motor-v2-double.png
