phiphi33/block/stl/electronic-parts/dupont/dupontx2.png

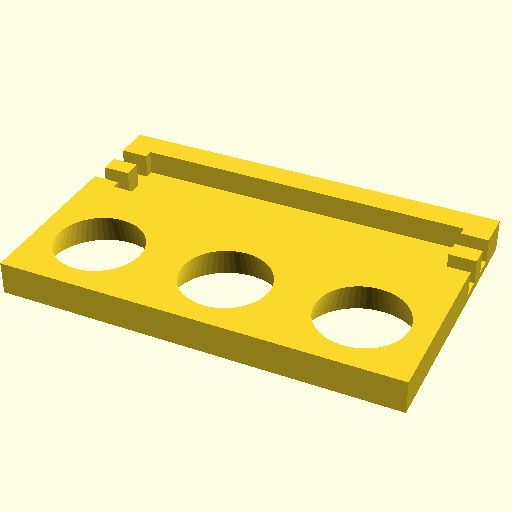
stl/electronic-parts/dupont/dupontx2.png
