phiphi33/block/stl/electronic-parts/dupont/dupontx4.png

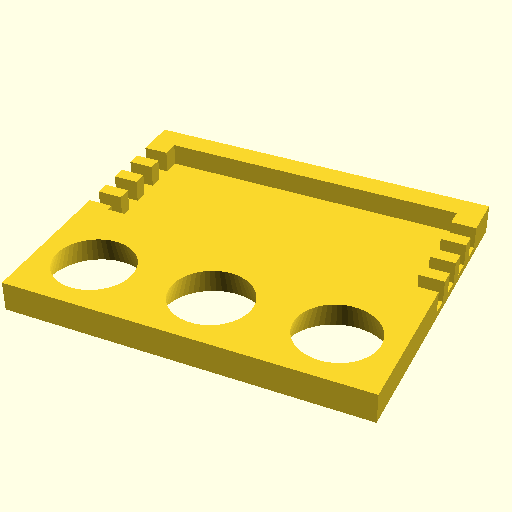
stl/electronic-parts/dupont/dupontx4.png
