phiphi33/block/stl/electronic-parts/esp32-30/esp32-30.png

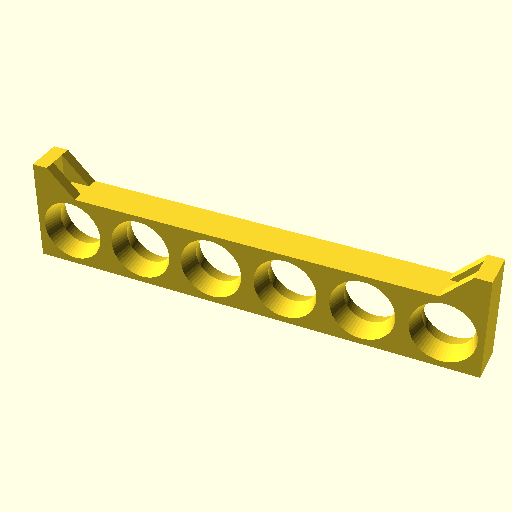
stl/electronic-parts/esp32-30/esp32-30.png
