phiphi33/block/stl/electronic-parts/esp32-cam/esp32-cam.png

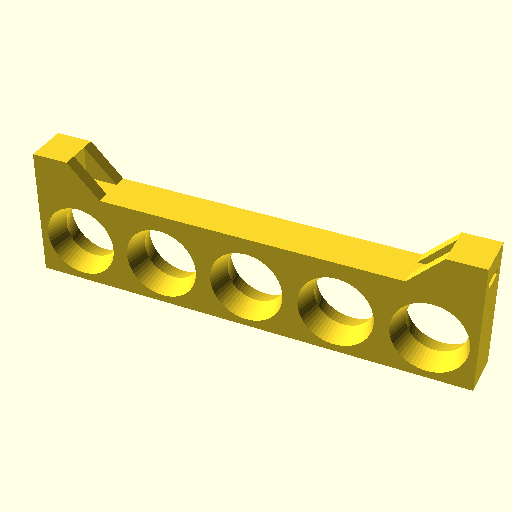
stl/electronic-parts/esp32-cam/esp32-cam.png
