phiphi33/block/stl/electronic-parts/l9110s/l9110s-bottom.png

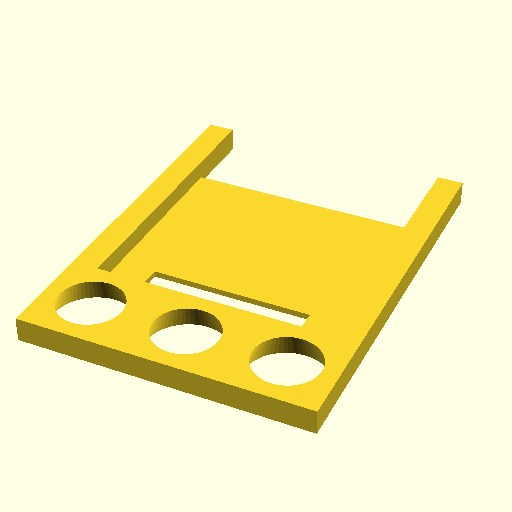
stl/electronic-parts/l9110s/l9110s-bottom.png
