phiphi33/block/stl/electronic-parts/l9110s/l9110s-side.png

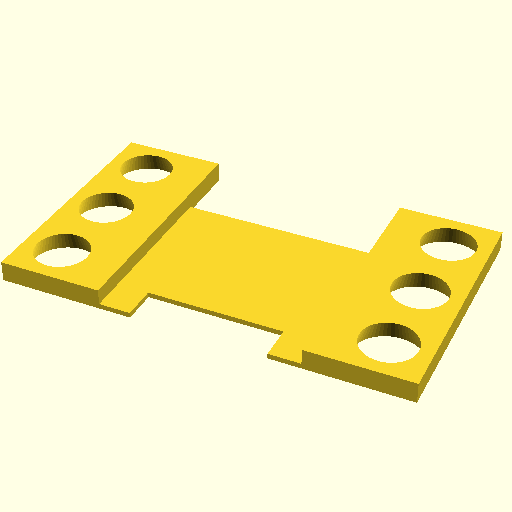
stl/electronic-parts/l9110s/l9110s-side.png
