phiphi33/block/stl/electronic-parts/n20-geared/n20-geared.png

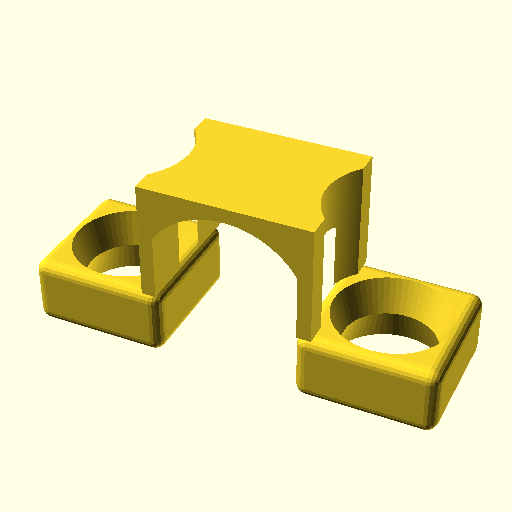
stl/electronic-parts/n20-geared/n20-geared.png
