phiphi33/block/stl/electronic-parts/nodemcu/nodemcu-bottom-2.png

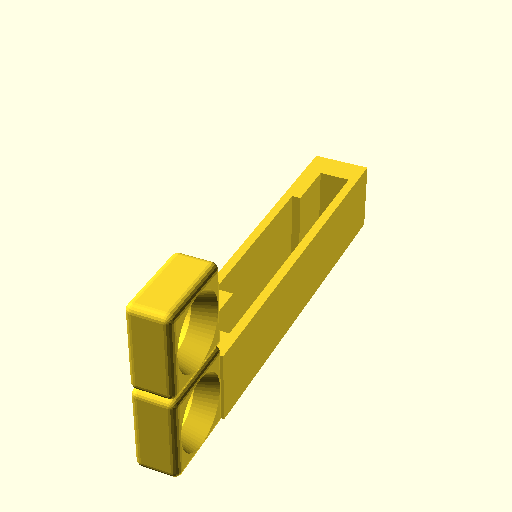
stl/electronic-parts/nodemcu/nodemcu-bottom-2.png
