phiphi33/block/stl/electronic-parts/nodemcu/nodemcu-generic.png

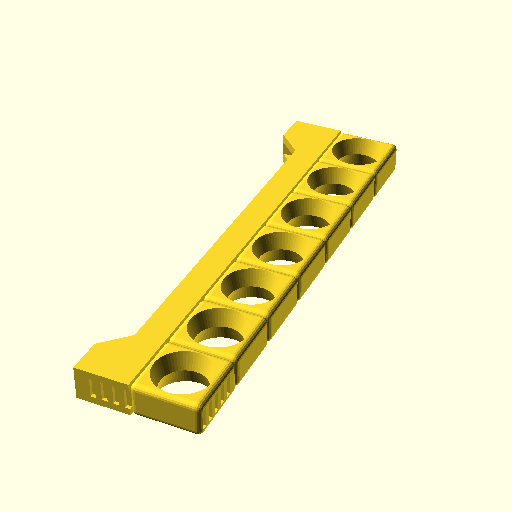
stl/electronic-parts/nodemcu/nodemcu-generic.png
