phiphi33/block/stl/electronic-parts/nodemcu/nodemcu-top-1side2.png

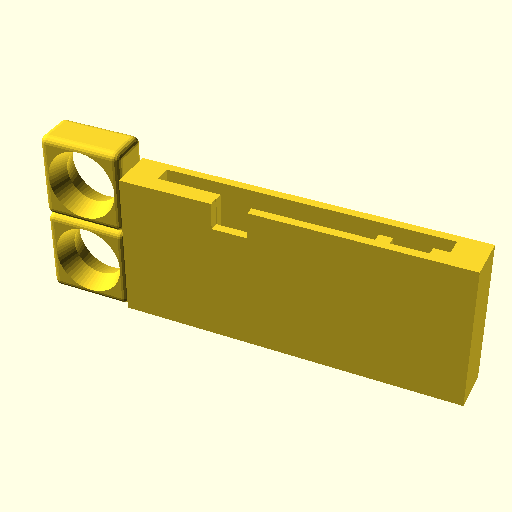
stl/electronic-parts/nodemcu/nodemcu-top-1side2.png
