phiphi33/block/stl/electronic-parts/oled-128x64/oled-128x64-bottom-2side.png

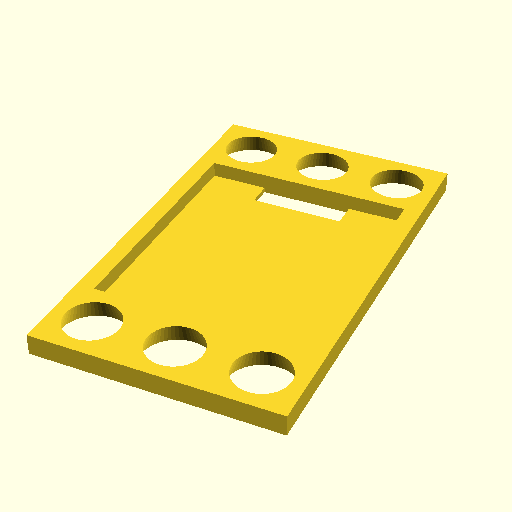
stl/electronic-parts/oled-128x64/oled-128x64-bottom-2side.png
