phiphi33/block/stl/electronic-parts/sg90/sg90-2x1-1side.png

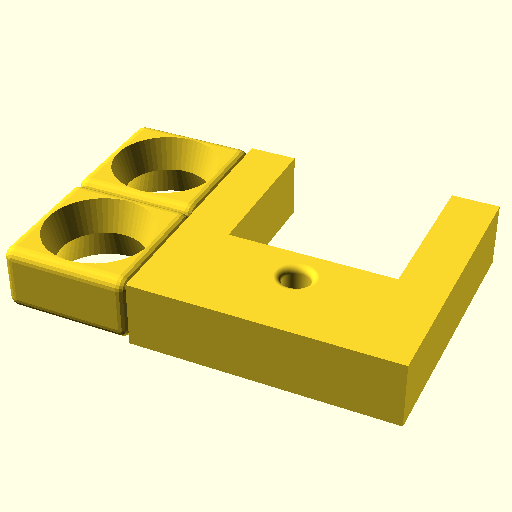
stl/electronic-parts/sg90/sg90-2x1-1side.png
