phiphi33/block/stl/electronic-parts/sg90/sg90-2x1.png

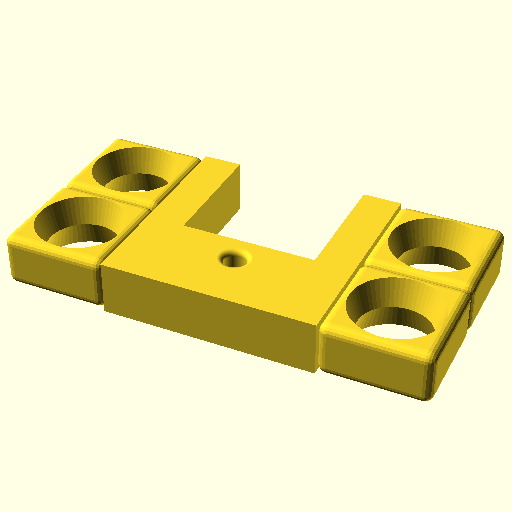
stl/electronic-parts/sg90/sg90-2x1.png
