phiphi33/block/stl/electronic-parts/sg90/sg90-2x2.png

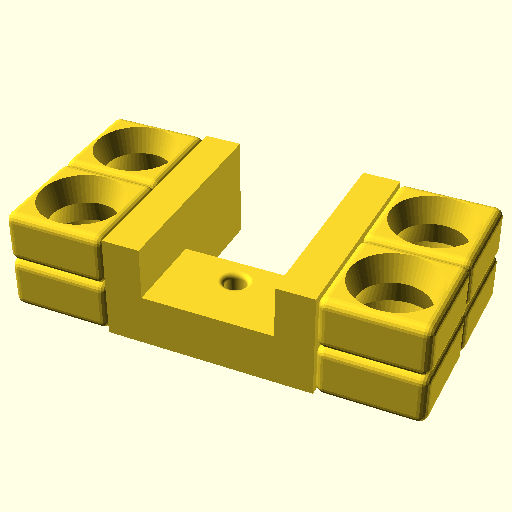
stl/electronic-parts/sg90/sg90-2x2.png
