phiphi33/block/stl/electronic-parts/sg90/sg90-3x1.png

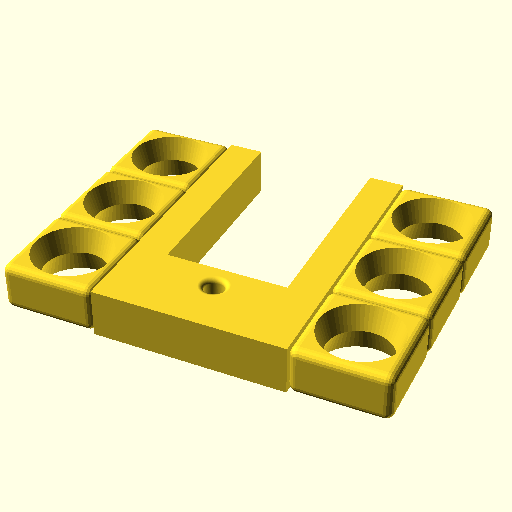
stl/electronic-parts/sg90/sg90-3x1.png
