phiphi33/block/stl/electronic-parts/sg90/sg90-4x1-large.png

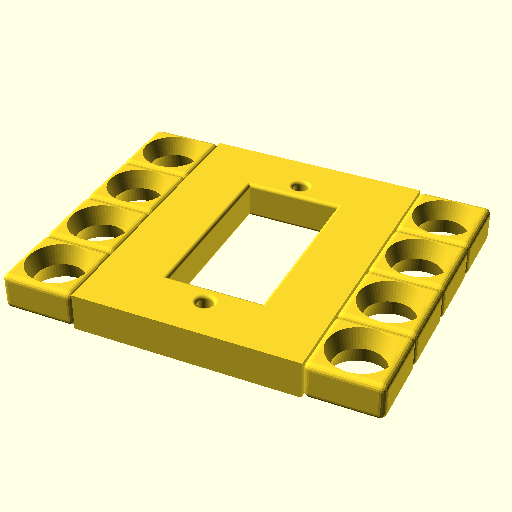
stl/electronic-parts/sg90/sg90-4x1-large.png
