phiphi33/block/stl/electronic-parts/sg90/sg90-helix-4.png

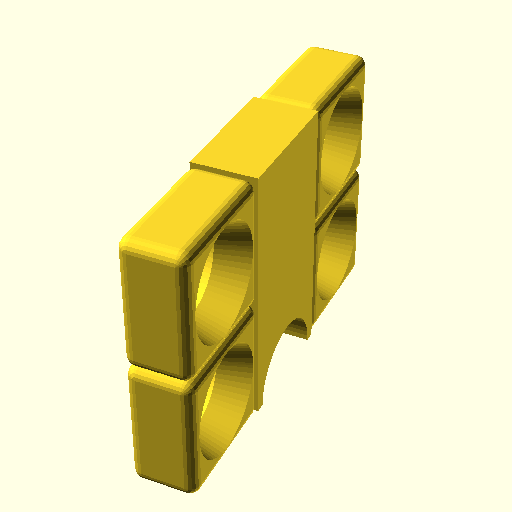
stl/electronic-parts/sg90/sg90-helix-4.png
