phiphi33/block/stl/electronic-parts/tm1637/tm1637-1other-side-bottom.png

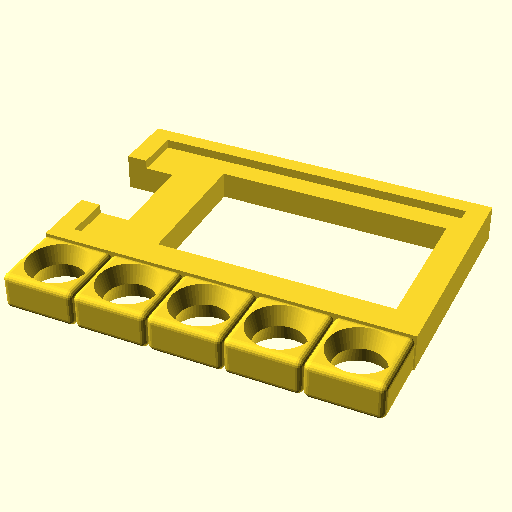
stl/electronic-parts/tm1637/tm1637-1other-side-bottom.png
