phiphi33/block/stl/electronic-parts/tm1637/tm1637-1side-top.png

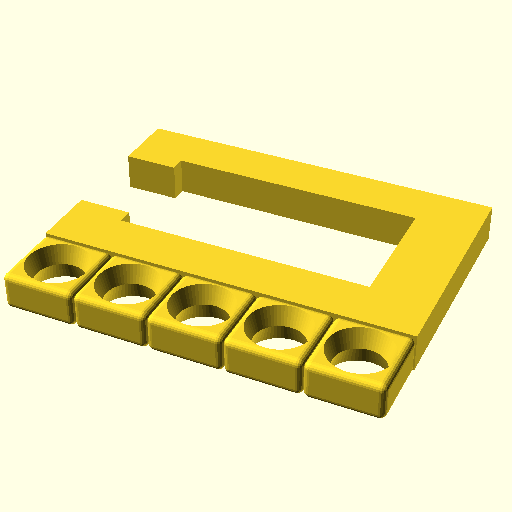
stl/electronic-parts/tm1637/tm1637-1side-top.png
