phiphi33/block/stl/electronic-parts/tm1637/tm1637-small-bottom.png

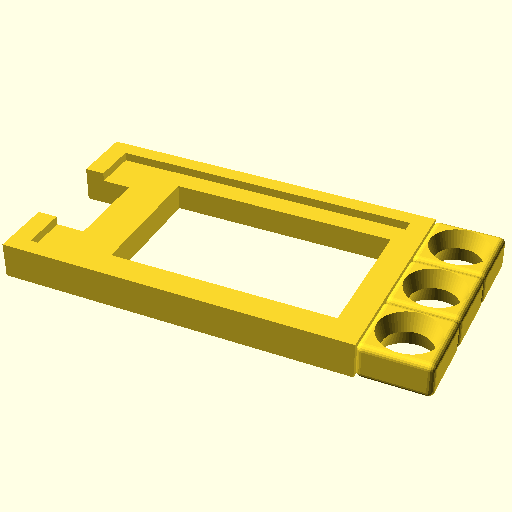
stl/electronic-parts/tm1637/tm1637-small-bottom.png
