phiphi33/block/stl/electronic-parts/wire/wire-2H.png

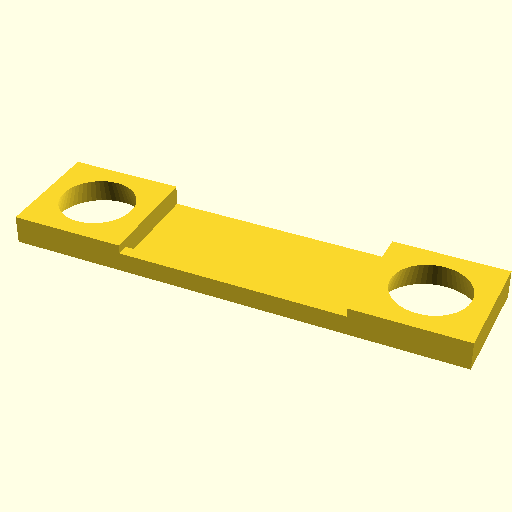
stl/electronic-parts/wire/wire-2H.png
