phiphi33/block/stl/electronic-parts/wire/wire-3-2side.png

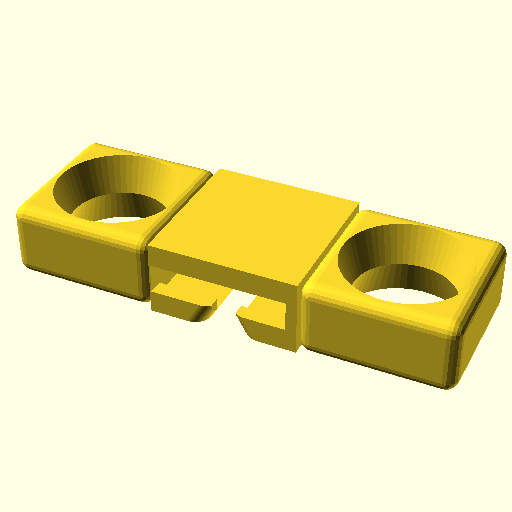
stl/electronic-parts/wire/wire-3-2side.png
