phiphi33/block/stl/electronic-parts/wire/wire-3-otherside.png

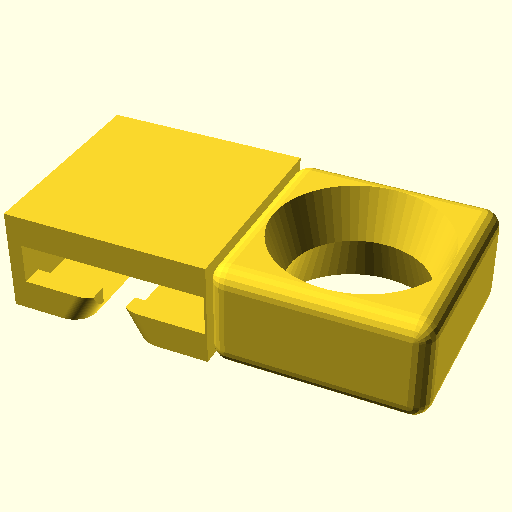
stl/electronic-parts/wire/wire-3-otherside.png
