phiphi33/block/stl/electronic-parts/wire/wire-3.png

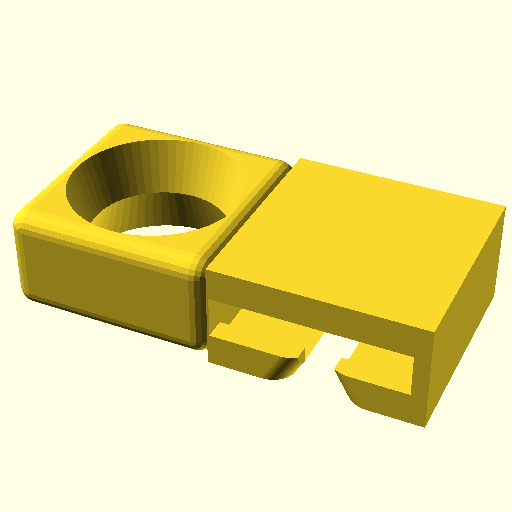
stl/electronic-parts/wire/wire-3.png
