phiphi33/block/stl/electronic-parts/wire/wire-5H-strong.png

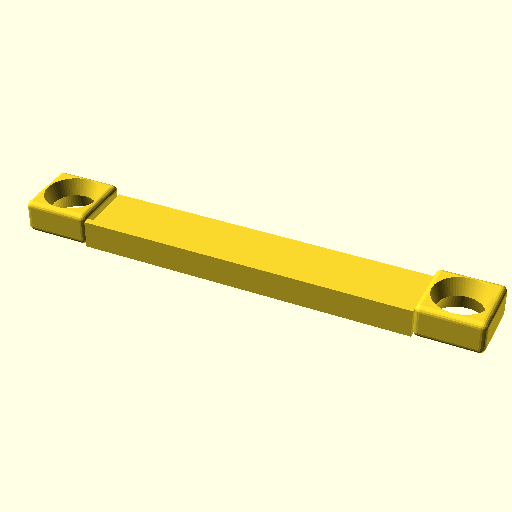
stl/electronic-parts/wire/wire-5H-strong.png
