phiphi33/block/stl/electronic-parts/wire/wire-6.png

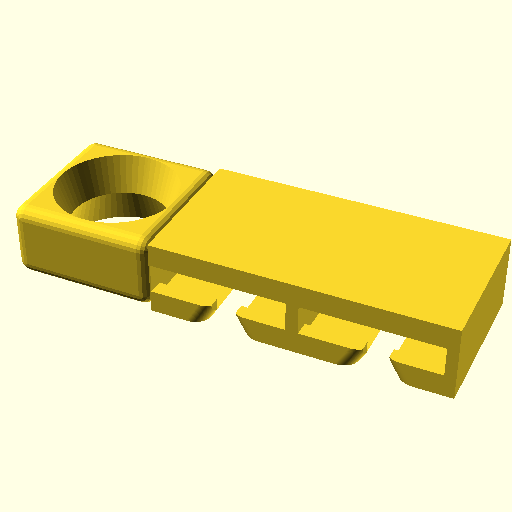
stl/electronic-parts/wire/wire-6.png
