phiphi33/block/other/spiralwheel/stl/SP65-medium-clip.stl

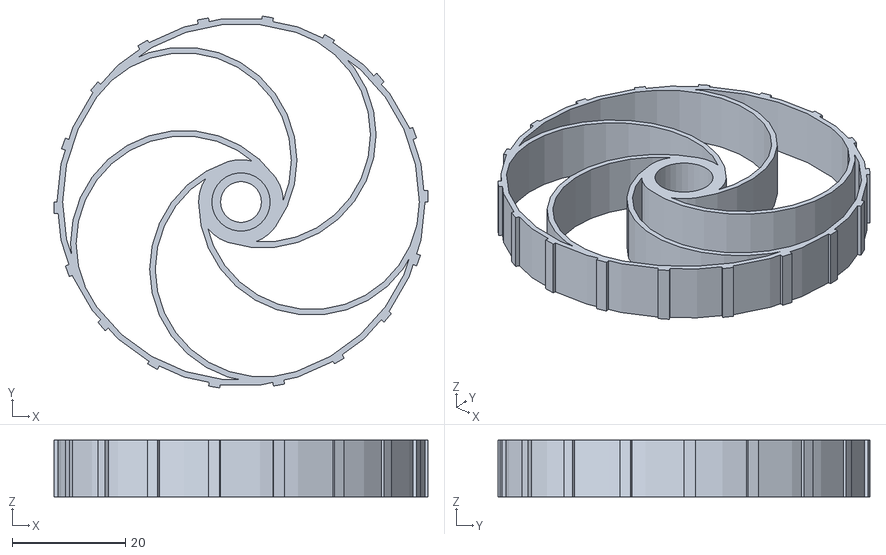
[picture p204: CAD file, 2024-02-18]
other/spiralwheel/stl/SP65-medium-clip.stl
66.0 x 65.7 x 10.0
