phiphi33/block/stl/basic-parts/P-5-4.stl

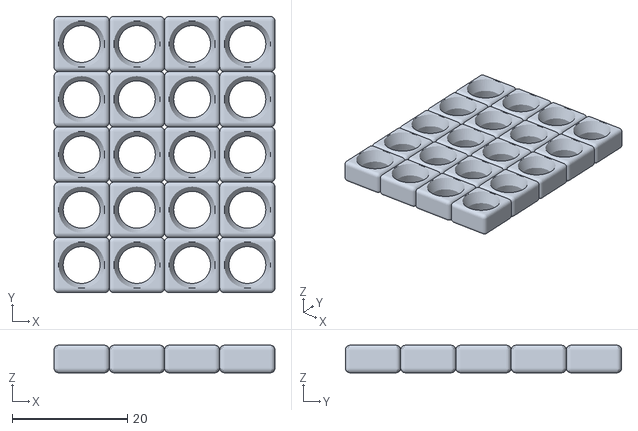
[picture p205: CAD file, 2024-02-21]
stl/basic-parts/P-5-4.stl
38.4 x 48.0 x 4.80
