phiphi33/block/stl/clips/clip-6-M4.stl

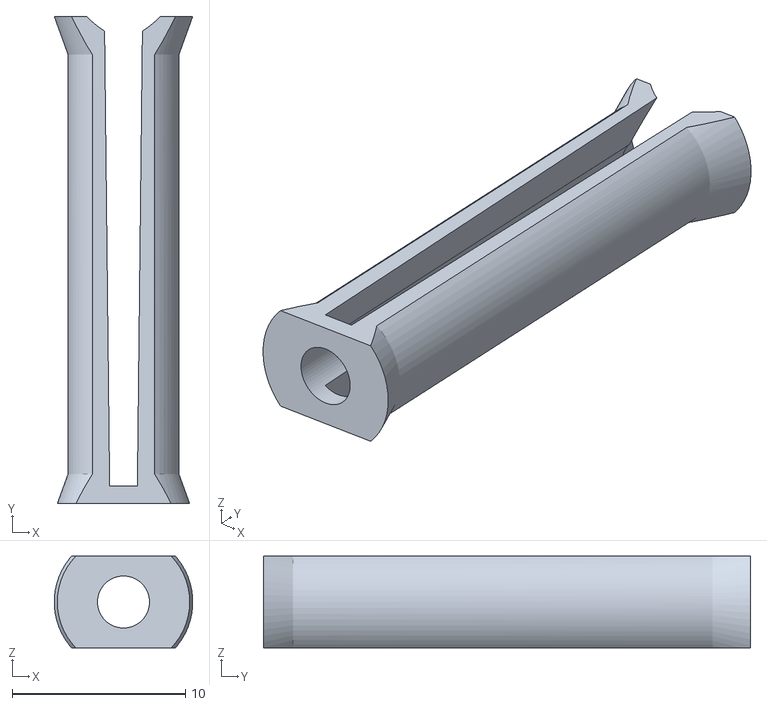
[picture p206: CAD file, 2024-01-07]
stl/clips/clip-6-M4.stl
7.99 x 28.1 x 5.30
