phiphi33/block/stl/electronic-parts/battery-shield/battery-shield-bottom-2.stl

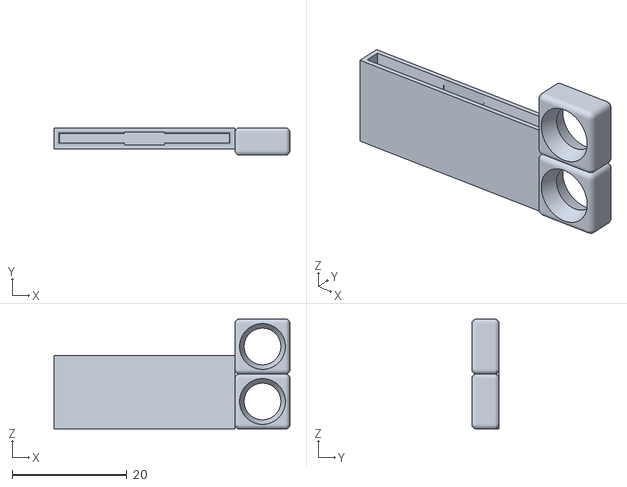
[picture p208: CAD file, 2024-01-14]
stl/electronic-parts/battery-shield/battery-shield-bottom-2.stl
41.2 x 4.80 x 19.2
