phiphi33/block/stl/electronic-parts/bme280/bme280.stl

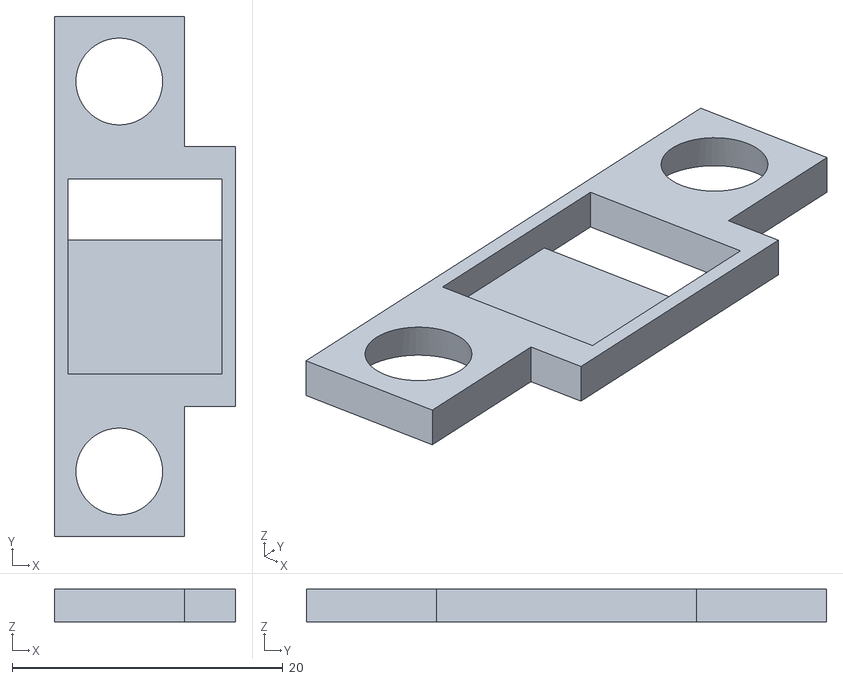
[picture p209: CAD file, 2019-09-07]
stl/electronic-parts/bme280/bme280.stl
13.4 x 38.4 x 2.40
