phiphi33/block/stl/electronic-parts/breadboard/breadboard25-2.stl

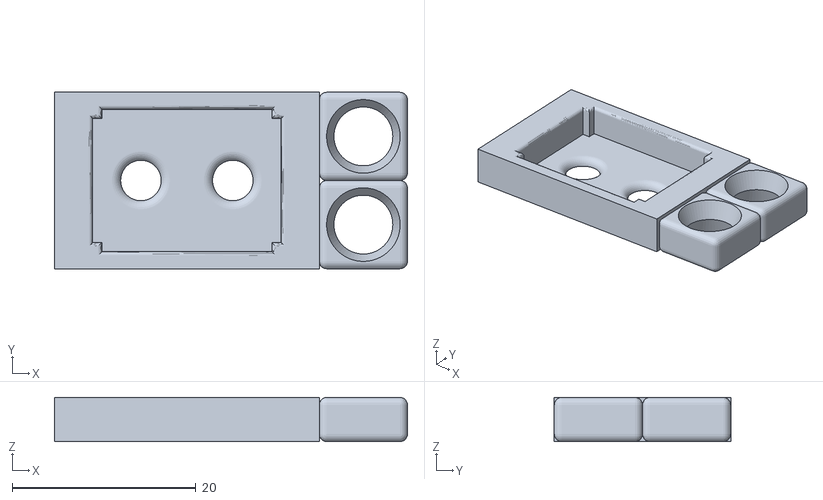
[picture p210: CAD file, 2024-01-14]
stl/electronic-parts/breadboard/breadboard25-2.stl
38.4 x 19.2 x 4.80
