phiphi33/block/stl/electronic-parts/D1-mini/D1-mini-other-side.stl

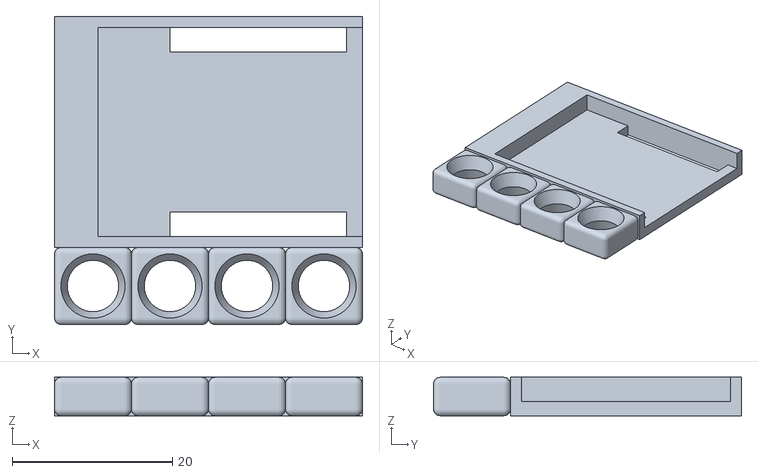
[picture p212: CAD file, 2024-01-14]
stl/electronic-parts/D1-mini/D1-mini-other-side.stl
38.4 x 38.4 x 4.80
