phiphi33/block/stl/electronic-parts/dc-motor-gear/dc-motor-v2-down.stl

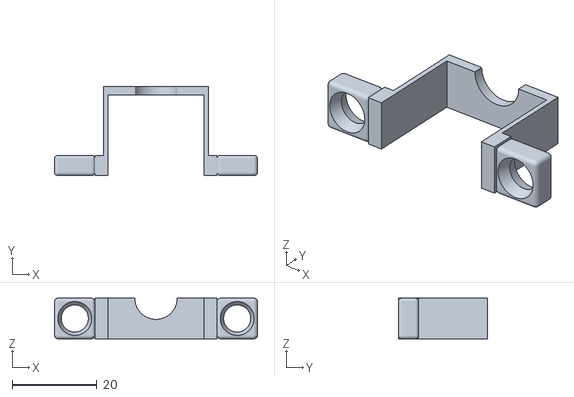
[picture p213: CAD file, 2024-01-14]
stl/electronic-parts/dc-motor-gear/dc-motor-v2-down.stl
48.0 x 21.1 x 9.60
