phiphi33/block/stl/electronic-parts/dupont/dupontx4.stl

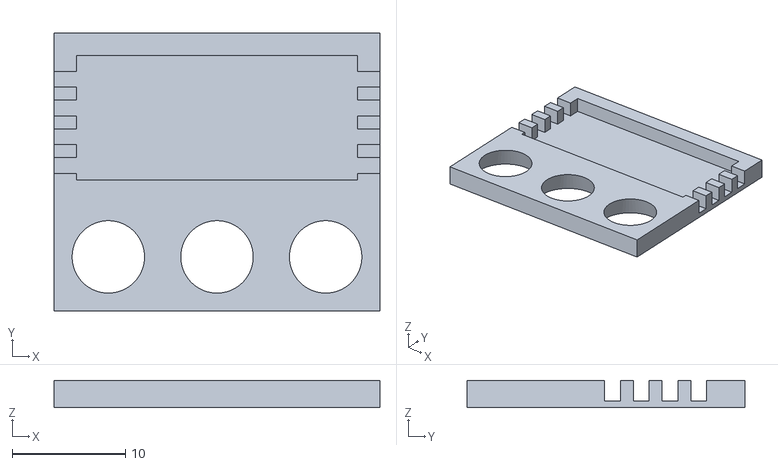
[picture p214: CAD file, 2020-05-10]
stl/electronic-parts/dupont/dupontx4.stl
28.8 x 24.6 x 2.40
