phiphi33/block/stl/electronic-parts/esp32-30/esp32-30.stl

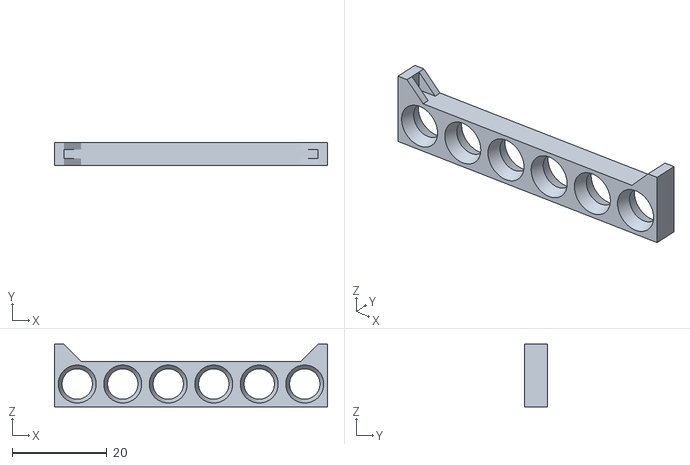
[picture p215: CAD file, 2024-01-14]
stl/electronic-parts/esp32-30/esp32-30.stl
57.6 x 4.80 x 13.2
