phiphi33/block/stl/electronic-parts/esp32-cam/esp32-cam.stl

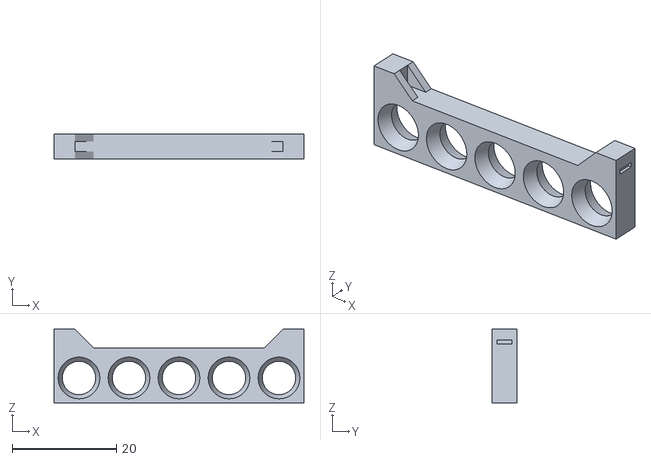
[picture p216: CAD file, 2024-01-14]
stl/electronic-parts/esp32-cam/esp32-cam.stl
48.0 x 4.80 x 14.2
