phiphi33/block/stl/electronic-parts/l9110s/l9110s-bottom.stl

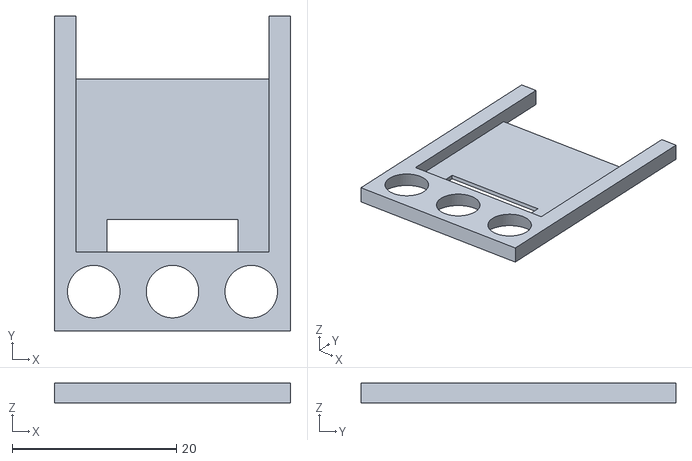
[picture p217: CAD file, 2019-09-07]
stl/electronic-parts/l9110s/l9110s-bottom.stl
28.8 x 38.4 x 2.40
