phiphi33/block/stl/electronic-parts/n20-geared/n20-geared-double.stl

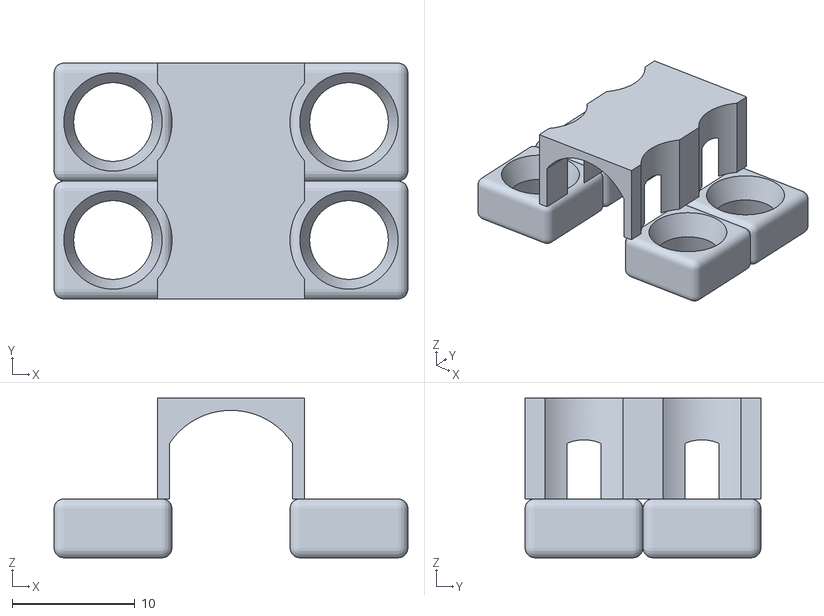
[picture p218: CAD file, 2024-01-14]
stl/electronic-parts/n20-geared/n20-geared-double.stl
28.8 x 19.2 x 13.0
