phiphi33/block/stl/electronic-parts/nodemcu/nodemcu-bottom.stl

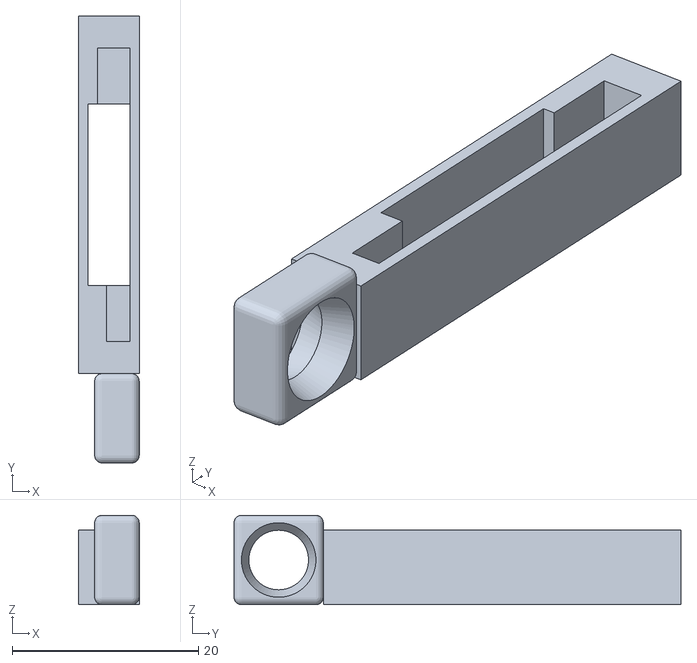
[picture p219: CAD file, 2024-01-14]
stl/electronic-parts/nodemcu/nodemcu-bottom.stl
6.50 x 48.0 x 9.60
