phiphi33/block/stl/electronic-parts/oled-128x64/oled-128x64-big-2side.stl

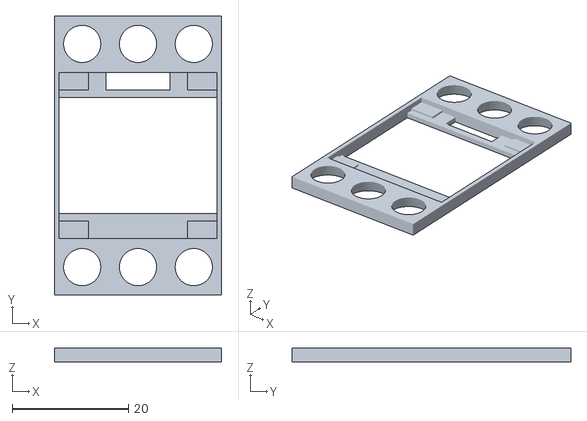
[picture p220: CAD file, 2023-08-28]
stl/electronic-parts/oled-128x64/oled-128x64-big-2side.stl
28.8 x 48.0 x 2.40
