phiphi33/block/stl/electronic-parts/pn532/pn532.stl

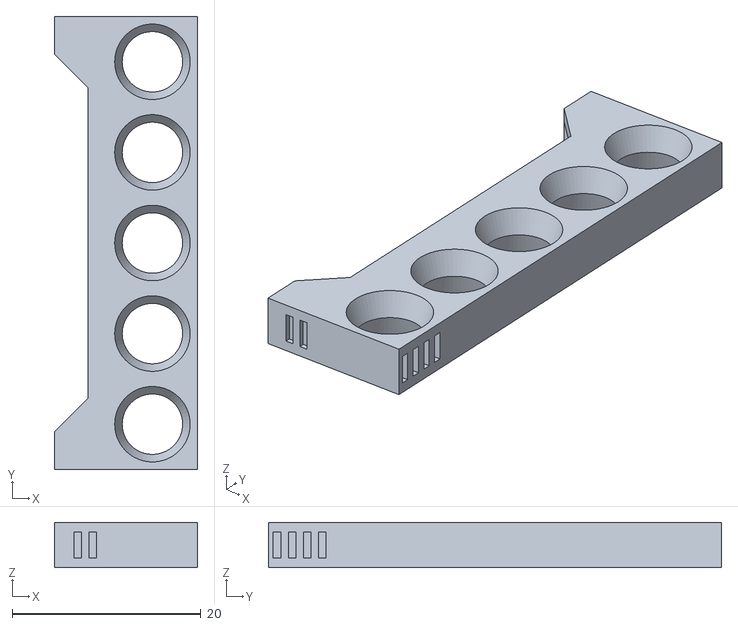
[picture p221: CAD file, 2024-01-14]
stl/electronic-parts/pn532/pn532.stl
15.2 x 48.0 x 4.80
