phiphi33/block/stl/electronic-parts/rc522/rc522.stl

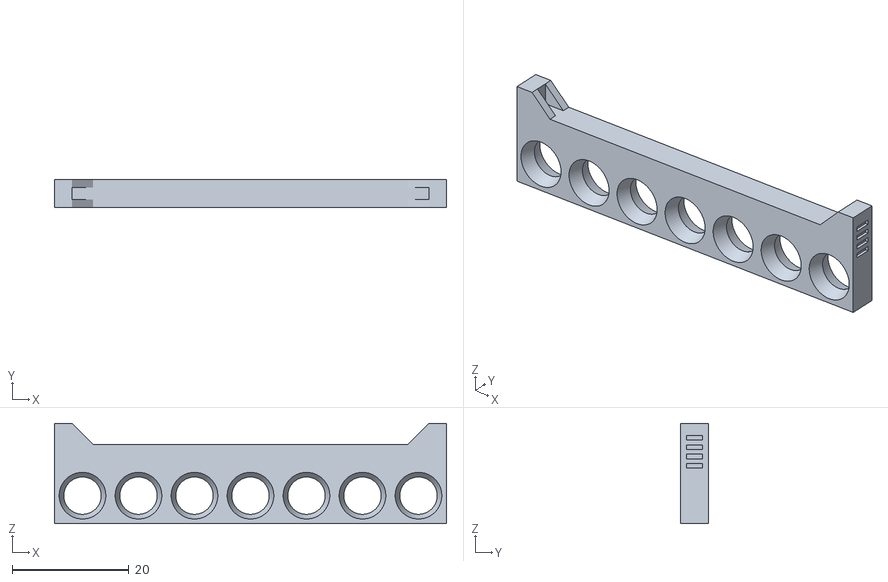
[picture p222: CAD file, 2024-01-14]
stl/electronic-parts/rc522/rc522.stl
67.2 x 4.80 x 17.2
