phiphi33/block/stl/electronic-parts/sg90/sg90-helix-1.stl

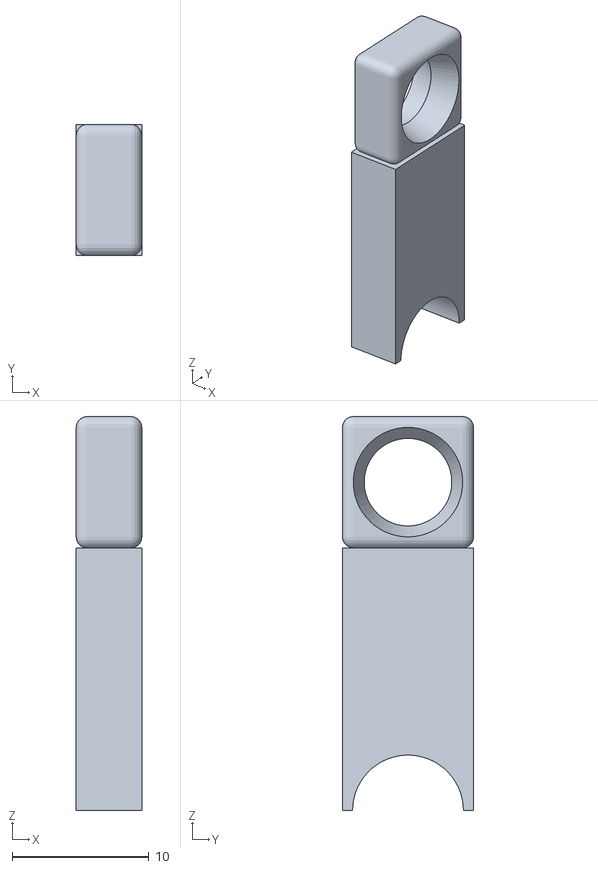
[picture p223: CAD file, 2024-01-14]
stl/electronic-parts/sg90/sg90-helix-1.stl
4.80 x 9.60 x 28.8
