phiphi33/block/stl/electronic-parts/switch/switch-4.stl

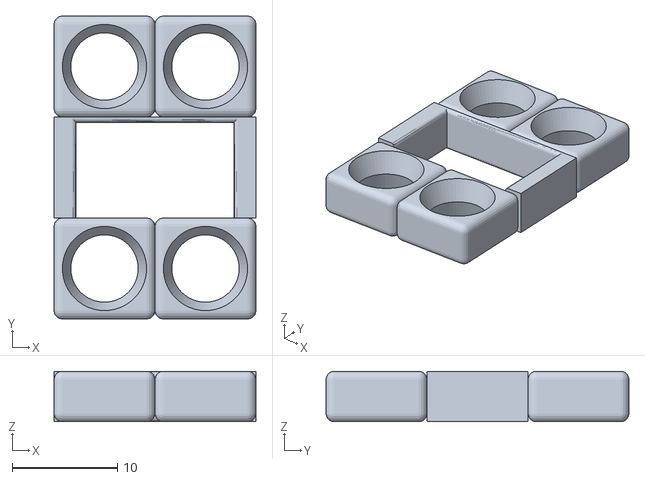
[picture p224: CAD file, 2024-02-28]
stl/electronic-parts/switch/switch-4.stl
19.2 x 28.8 x 4.80
