phiphi33/block/stl/electronic-parts/tm1637/tm1637-1other-side-top.stl

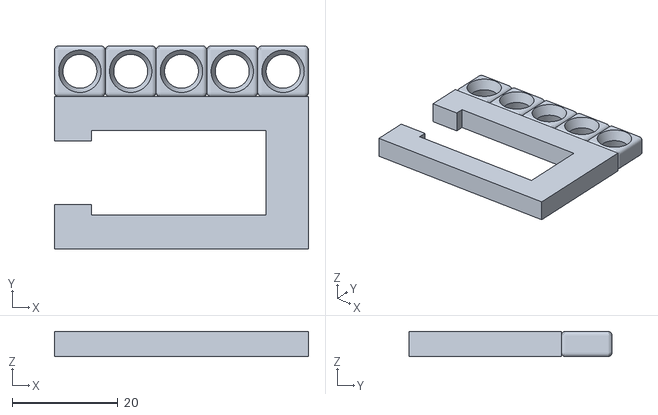
[picture p225: CAD file, 2024-01-14]
stl/electronic-parts/tm1637/tm1637-1other-side-top.stl
48.0 x 38.4 x 4.80
