phiphi33/block/stl/electronic-parts/wire/wire-4H-strong.stl

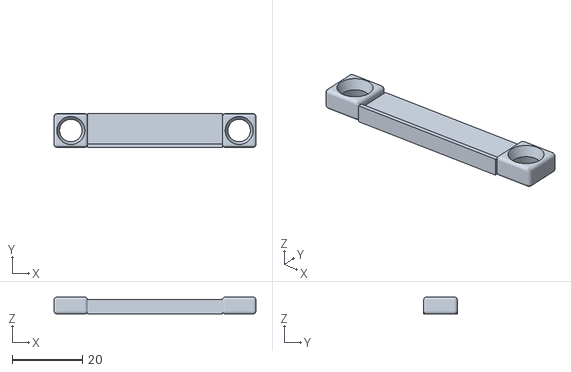
[picture p226: CAD file, 2024-01-14]
stl/electronic-parts/wire/wire-4H-strong.stl
57.6 x 9.60 x 4.80
