phiphi33/block/stl/electronic/sg90-4x1-1side.stl

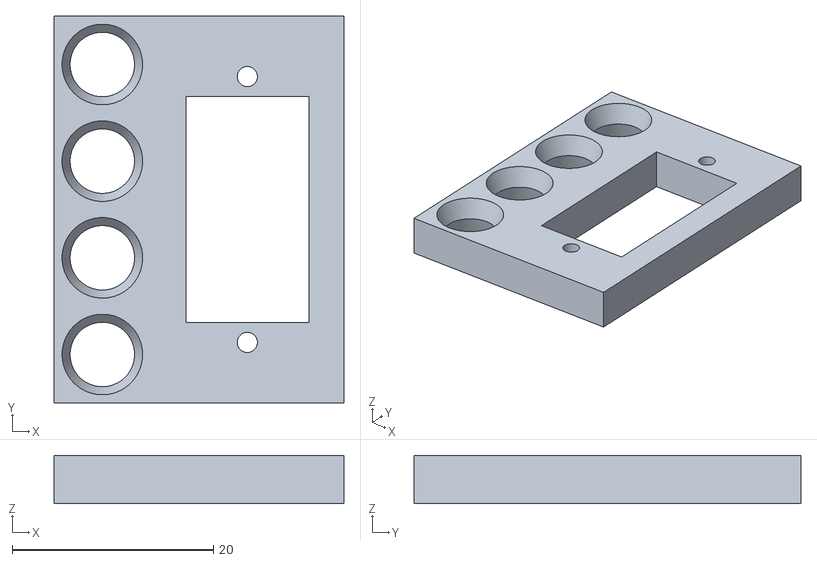
[picture p227: CAD file, 2020-05-04]
stl/electronic/sg90-4x1-1side.stl
28.8 x 38.4 x 4.80
