phiphi33/block/tests/spiralwheel/stl/SP65-dc-gearbox.stl

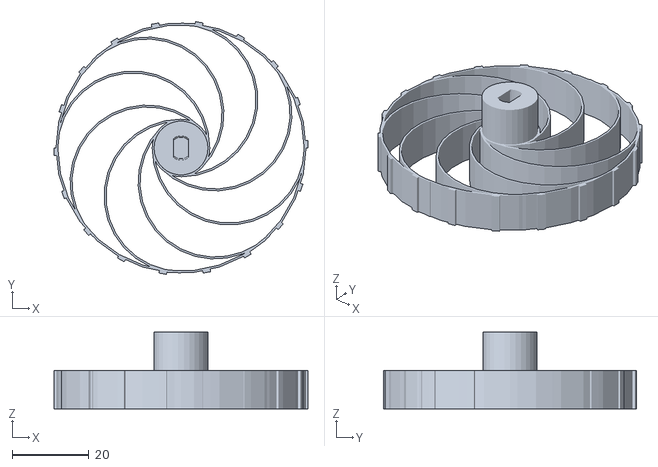
[picture p228: CAD file, 2020-05-11]
tests/spiralwheel/stl/SP65-dc-gearbox.stl
66.0 x 65.7 x 20.0
