phiphi33/block/dat/clips/clip-3a.stl

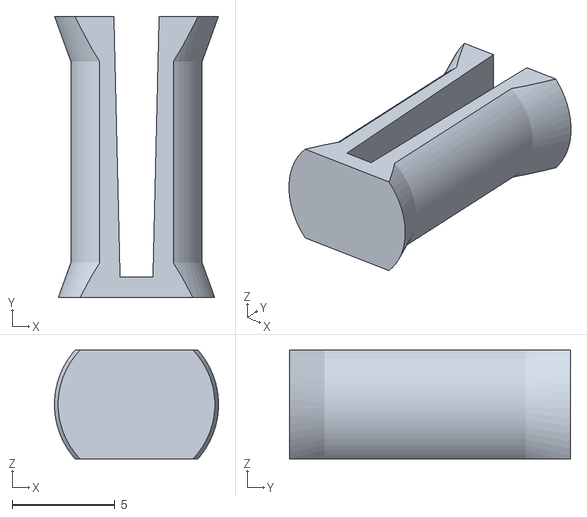
[picture p229: CAD file, 2022-05-13]
dat/clips/clip-3a.stl
7.99 x 13.7 x 5.30
