phiphi33/block/dat/other/other-L9110.stl

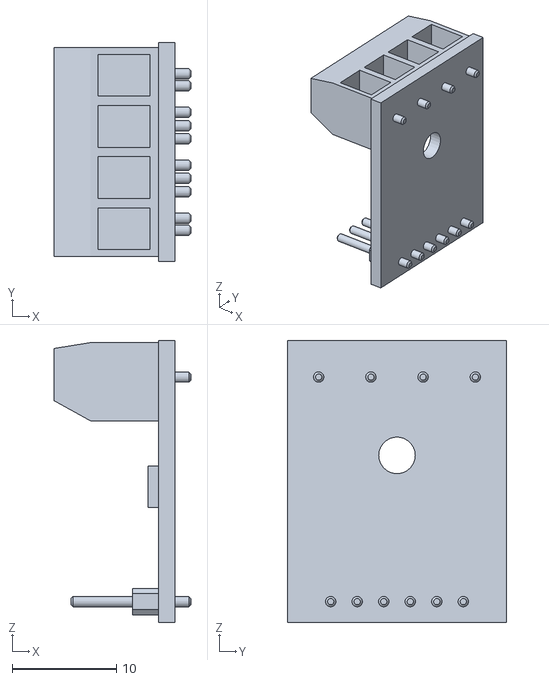
[picture p230: CAD file, 2022-05-13]
dat/other/other-L9110.stl
13.1 x 21.0 x 27.0
