phiphi33/block/imports/joystick-generic.stl

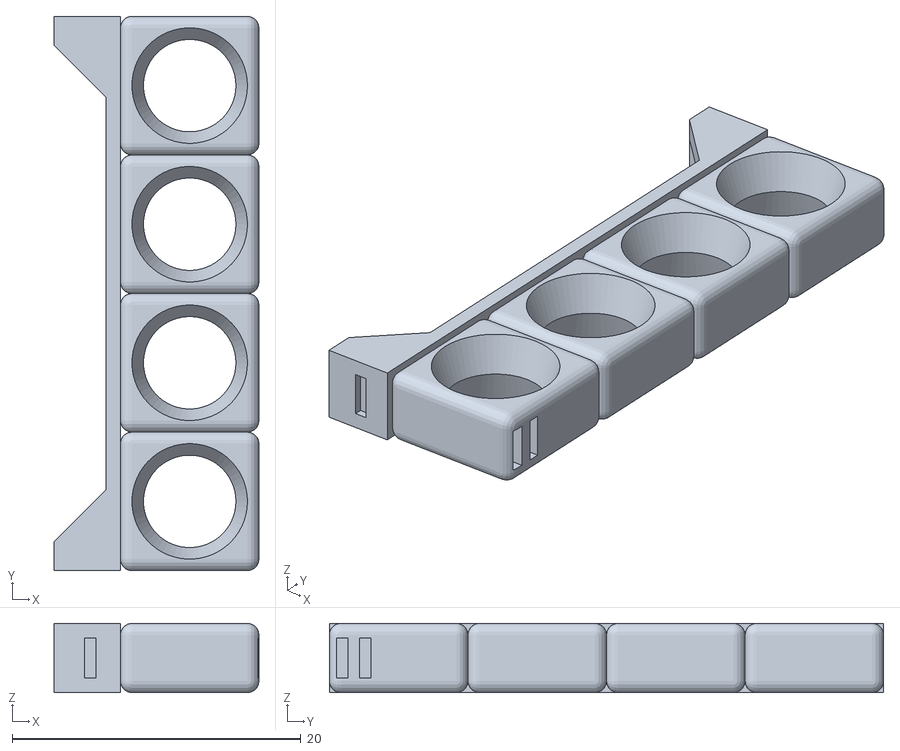
[picture p231: CAD file, 2024-02-14]
imports/joystick-generic.stl
14.2 x 38.4 x 4.80
