phiphi33/block/other/12.8/stl/basic-parts/C-2-1-1.stl

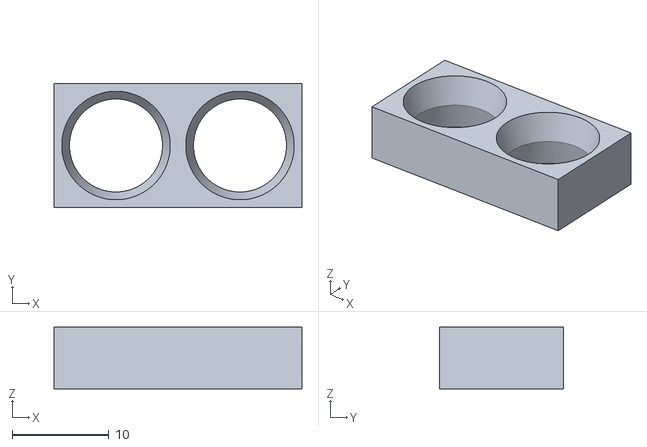
[picture p232: CAD file, 2020-06-02]
other/12.8/stl/basic-parts/C-2-1-1.stl
25.6 x 12.8 x 6.40
