phiphi33/block/other/12.8/stl/clips/clip-2-line.stl

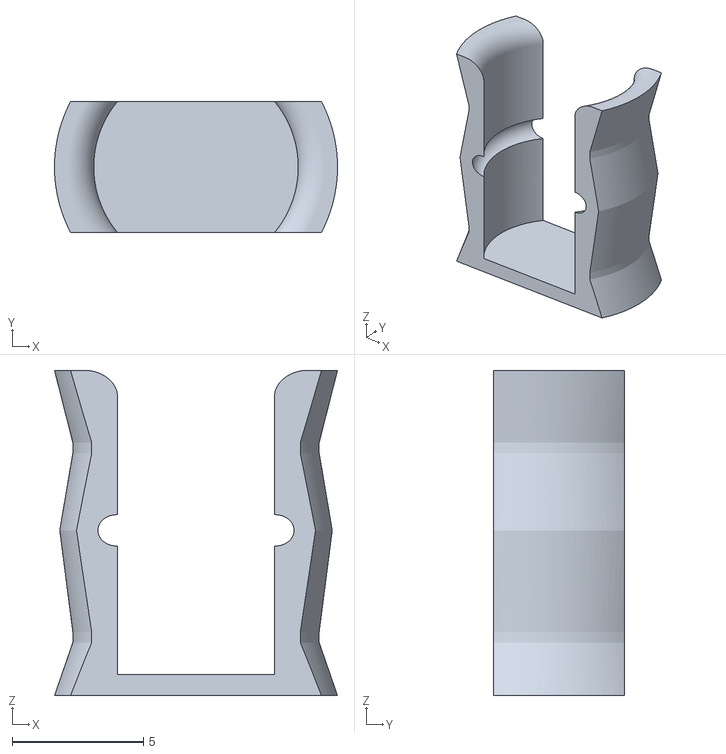
[picture p233: CAD file, 2020-06-02]
other/12.8/stl/clips/clip-2-line.stl
10.8 x 5.00 x 12.4
