phiphi33/block/other/6.4/stl/basic/P-2-2.stl

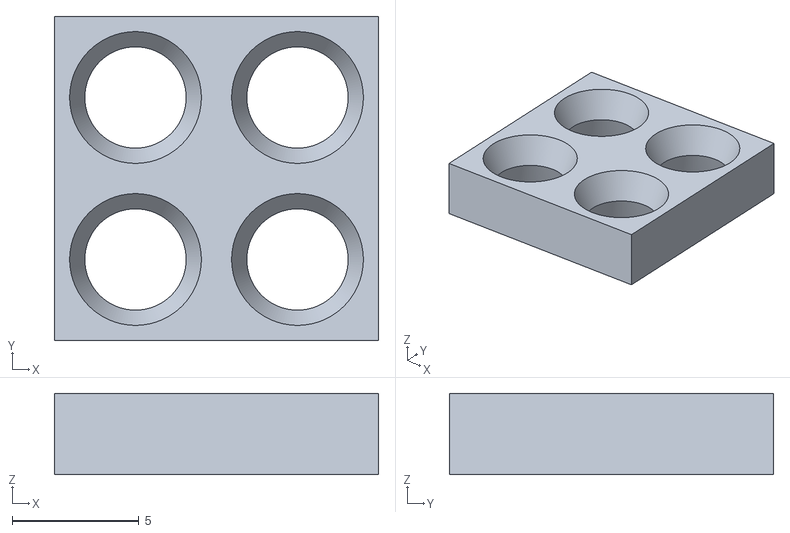
[picture p234: CAD file, 2020-04-19]
other/6.4/stl/basic/P-2-2.stl
12.8 x 12.8 x 3.20
