phiphi33/block/other/gears/stl/gears_bevel-14.stl

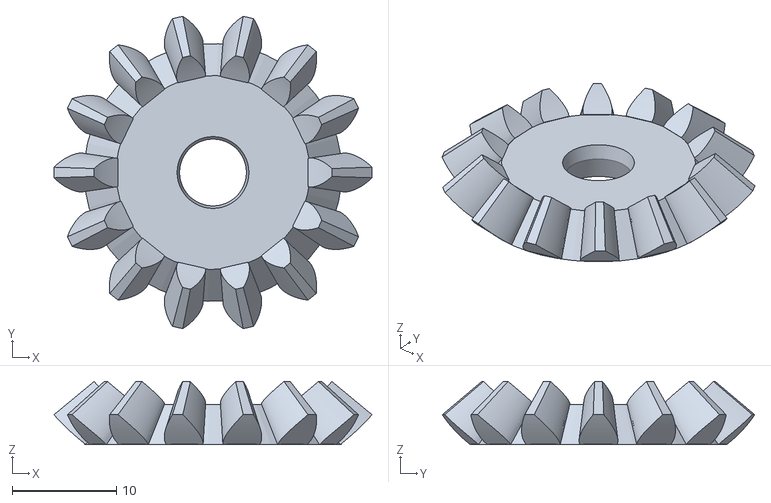
[picture p235: CAD file, 2023-12-05]
other/gears/stl/gears_bevel-14.stl
30.5 x 30.0 x 6.05
