phiphi33/block/other/lego/stl/L6.stl

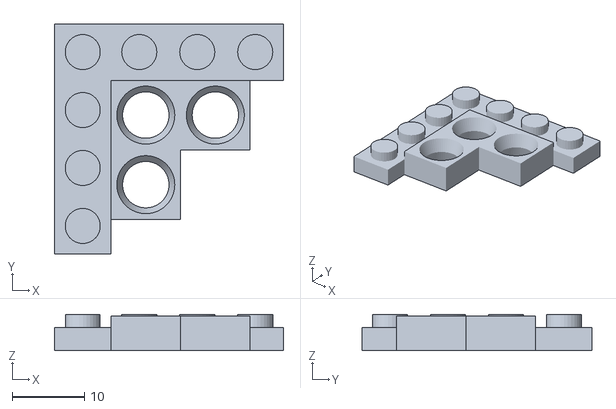
[picture p236: CAD file, 2022-05-13]
other/lego/stl/L6.stl
31.6 x 31.8 x 5.00
