phiphi33/block/other/spiralwheel/stl/SP45-medium-clip.stl

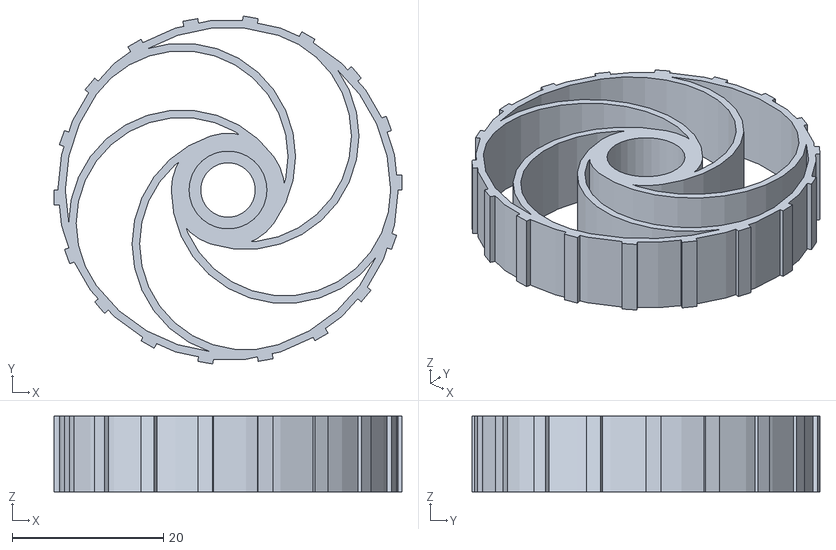
[picture p237: CAD file, 2024-02-18]
other/spiralwheel/stl/SP45-medium-clip.stl
46.0 x 46.0 x 10.0
