phiphi33/block/stl/basic-parts/LF-6-3.stl

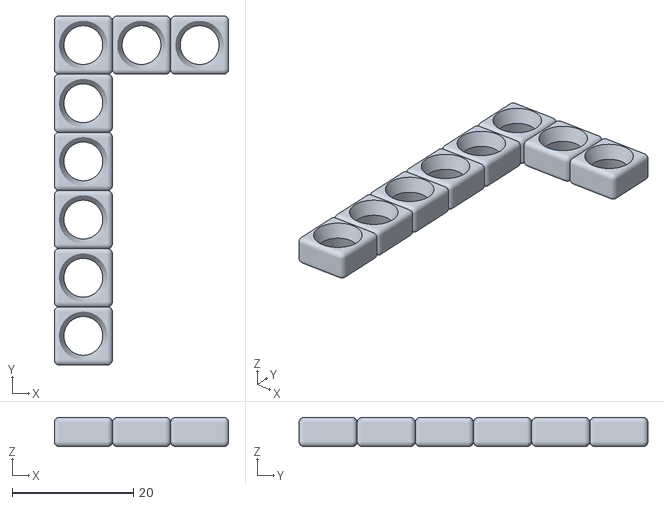
[picture p238: CAD file, 2024-01-11]
stl/basic-parts/LF-6-3.stl
28.8 x 57.6 x 4.80
