phiphi33/block/stl/clips/clip-5-M4.stl

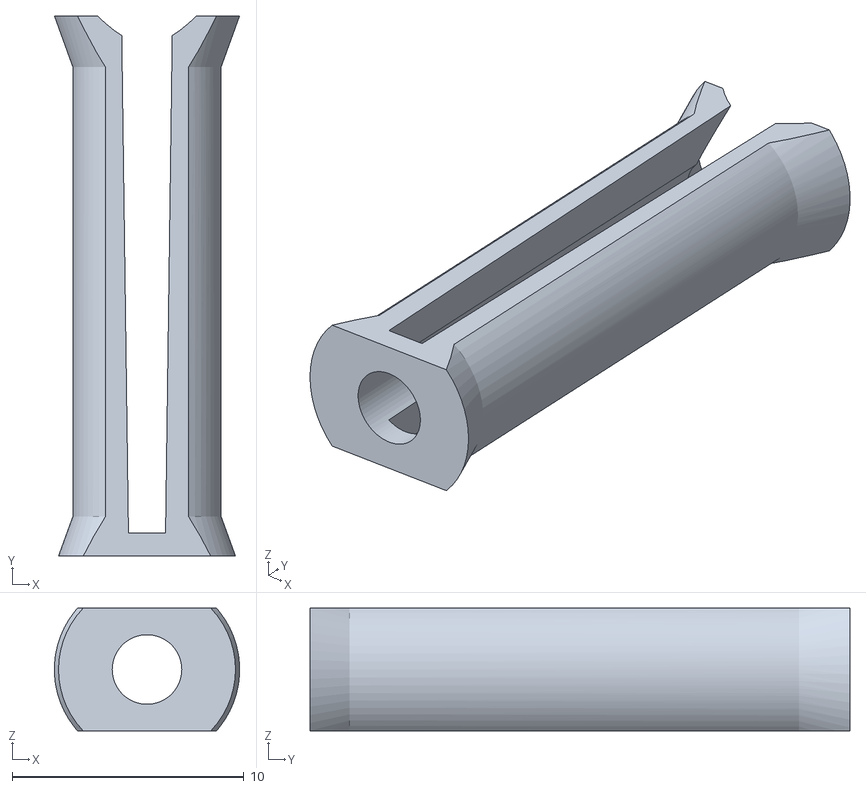
[picture p239: CAD file, 2024-01-07]
stl/clips/clip-5-M4.stl
7.99 x 23.3 x 5.30
