phiphi33/block/stl/electronic-parts/arduino-nano/nano-top-2side.stl

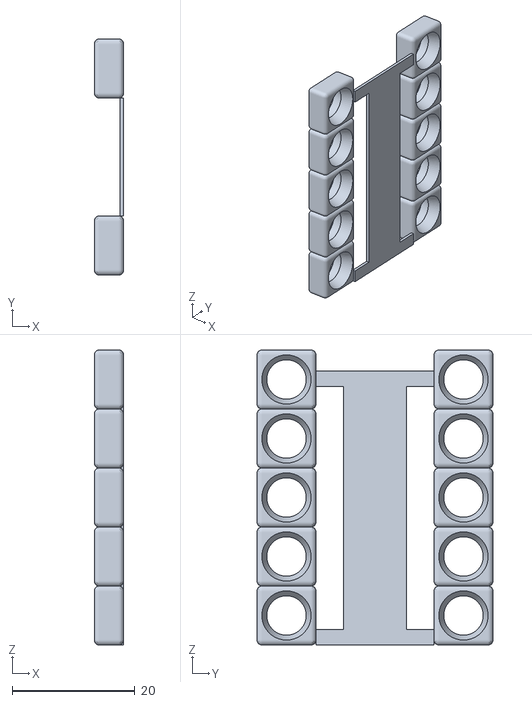
[picture p240: CAD file, 2024-01-14]
stl/electronic-parts/arduino-nano/nano-top-2side.stl
4.80 x 38.4 x 48.0
