phiphi33/block/stl/electronic-parts/battery-shield/battery-shield-bottom-1.stl

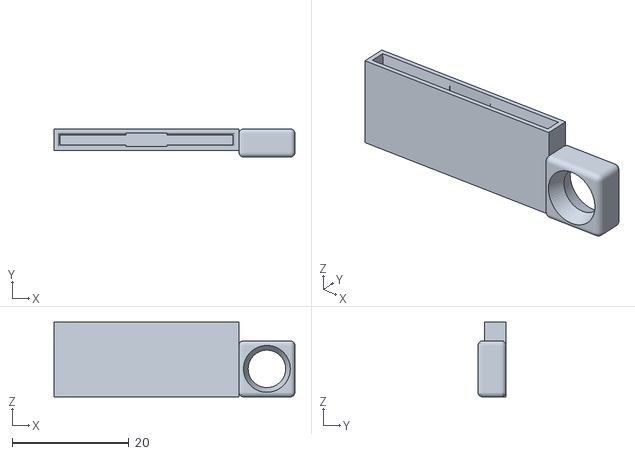
[picture p241: CAD file, 2024-01-14]
stl/electronic-parts/battery-shield/battery-shield-bottom-1.stl
41.2 x 4.80 x 12.8
