phiphi33/block/stl/electronic-parts/breadboard/breadboard25-3.stl

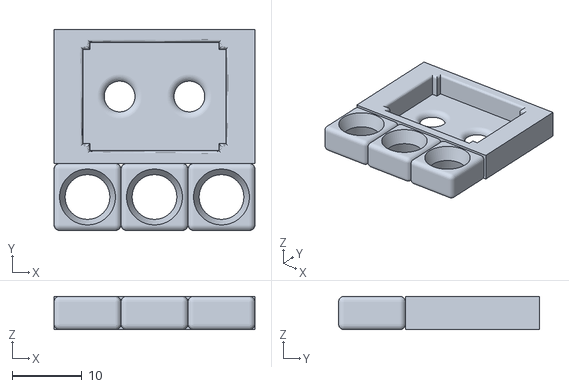
[picture p242: CAD file, 2024-01-14]
stl/electronic-parts/breadboard/breadboard25-3.stl
28.8 x 28.8 x 4.80
