phiphi33/block/stl/electronic-parts/button14x20/button14x20-half-topx2-1side.stl

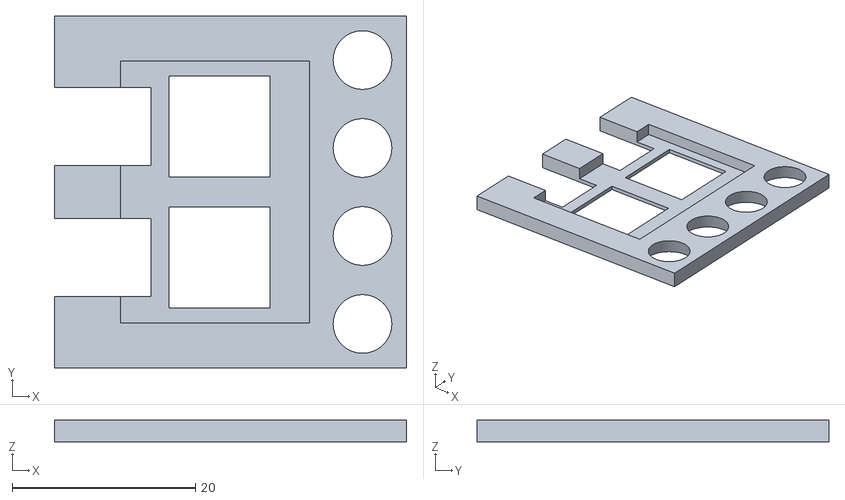
[picture p243: CAD file, 2022-05-13]
stl/electronic-parts/button14x20/button14x20-half-topx2-1side.stl
38.4 x 38.4 x 2.40
