phiphi33/block/stl/electronic-parts/dc-motor-gear/dc-motor-v2-down-double.stl

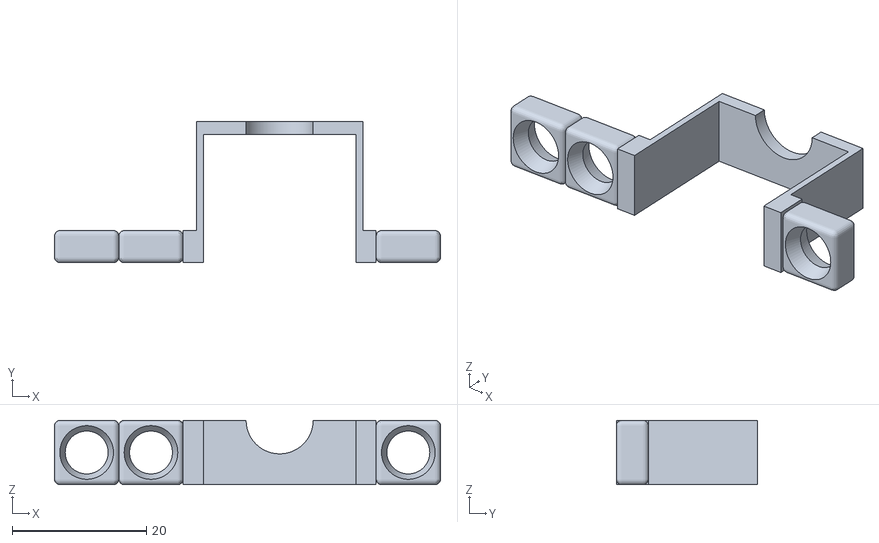
[picture p244: CAD file, 2024-01-14]
stl/electronic-parts/dc-motor-gear/dc-motor-v2-down-double.stl
57.6 x 21.1 x 9.60
