phiphi33/block/stl/electronic-parts/dupont/dupontx6.stl

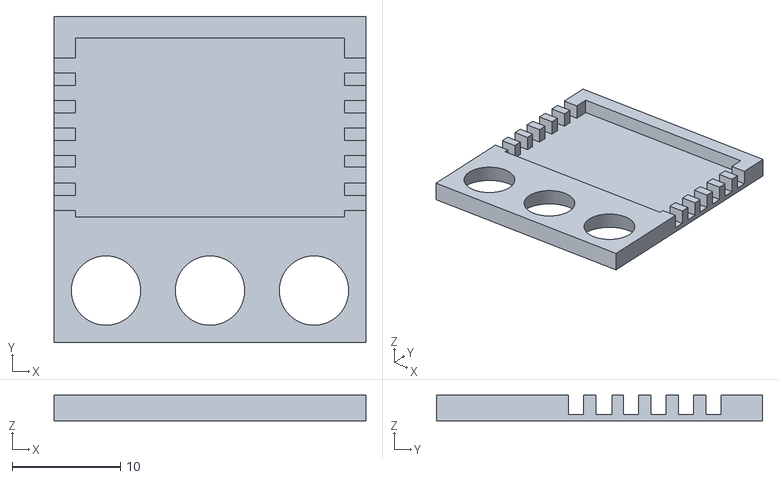
[picture p245: CAD file, 2020-05-10]
stl/electronic-parts/dupont/dupontx6.stl
28.8 x 30.1 x 2.40
