phiphi33/block/stl/electronic-parts/l9110s/l9110s-side.stl

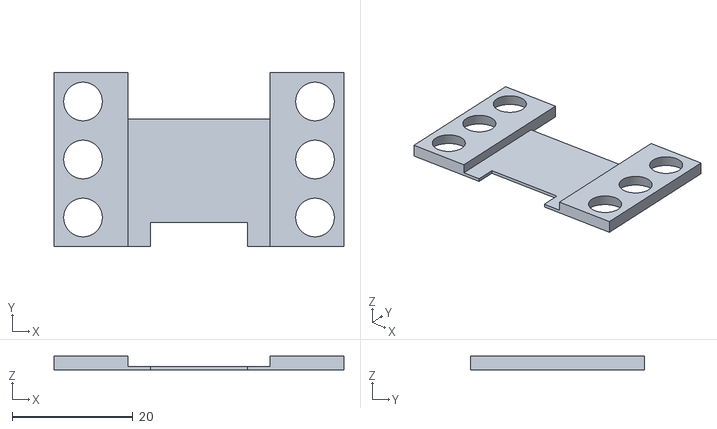
[picture p246: CAD file, 2019-08-03]
stl/electronic-parts/l9110s/l9110s-side.stl
48.0 x 28.8 x 2.40
