phiphi33/block/stl/electronic-parts/n20-geared/n20-geared.stl

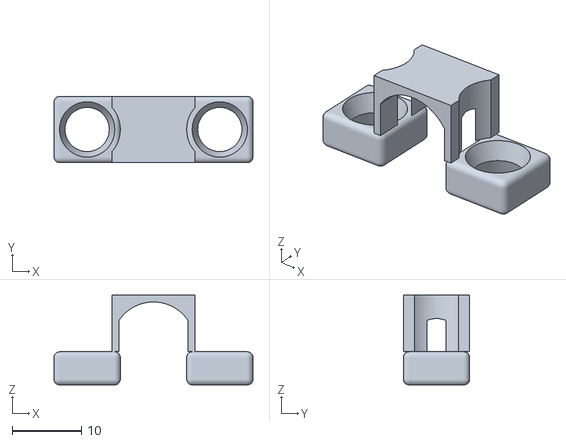
[picture p247: CAD file, 2024-01-14]
stl/electronic-parts/n20-geared/n20-geared.stl
28.8 x 9.60 x 13.0
