phiphi33/block/stl/electronic-parts/nodemcu/nodemcu-top-small-1side.stl

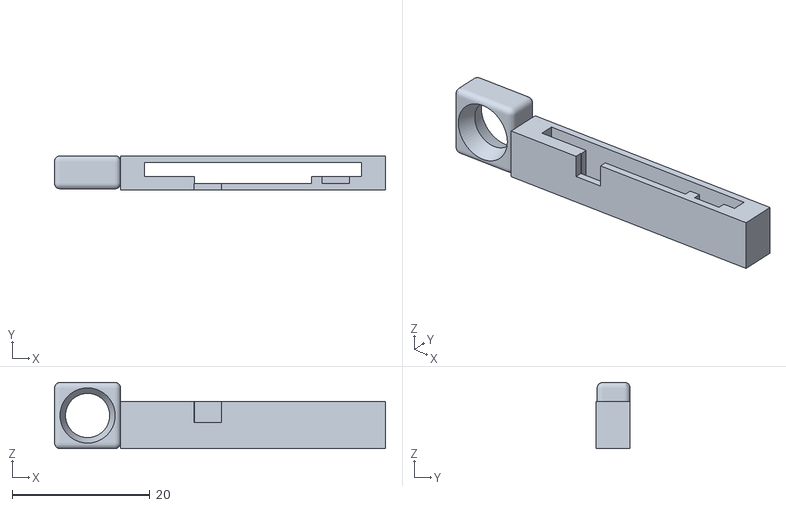
[picture p248: CAD file, 2024-01-14]
stl/electronic-parts/nodemcu/nodemcu-top-small-1side.stl
48.0 x 5.00 x 9.60
