phiphi33/block/stl/electronic-parts/oled-128x64/oled-128x64-big-1side.stl

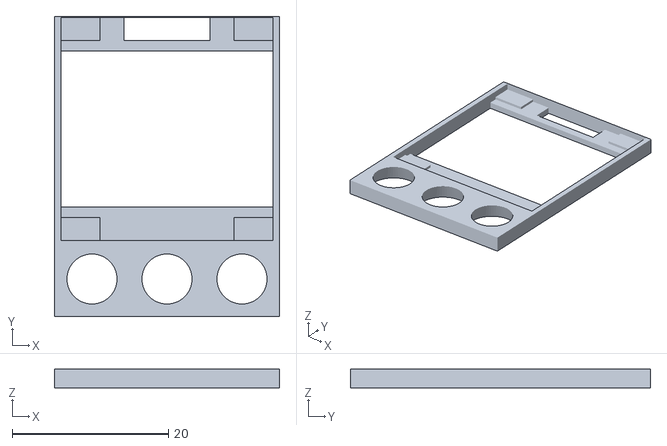
[picture p249: CAD file, 2023-08-28]
stl/electronic-parts/oled-128x64/oled-128x64-big-1side.stl
28.8 x 38.4 x 2.40
