phiphi33/block/stl/electronic-parts/sg90/sg90-helix-4.stl

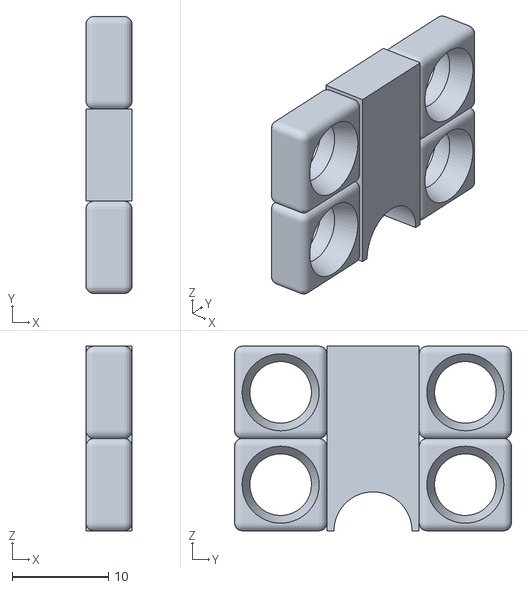
[picture p250: CAD file, 2024-01-14]
stl/electronic-parts/sg90/sg90-helix-4.stl
4.80 x 28.8 x 19.2
