phiphi33/block/stl/electronic-parts/tm1637/tm1637-small-top.stl

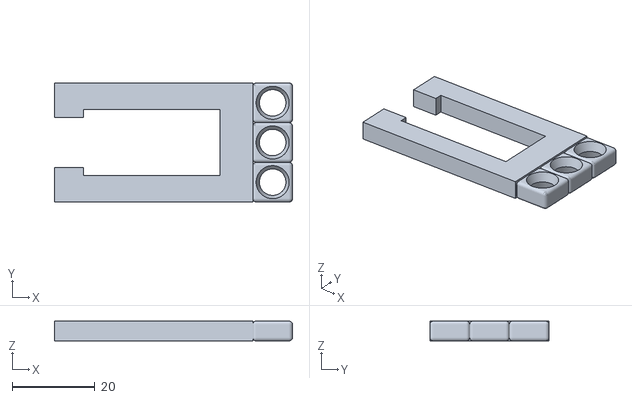
[picture p251: CAD file, 2024-01-14]
stl/electronic-parts/tm1637/tm1637-small-top.stl
57.6 x 28.8 x 4.80
