phiphi33/block/stl/electronic-parts/wire/wire-3-otherside.stl

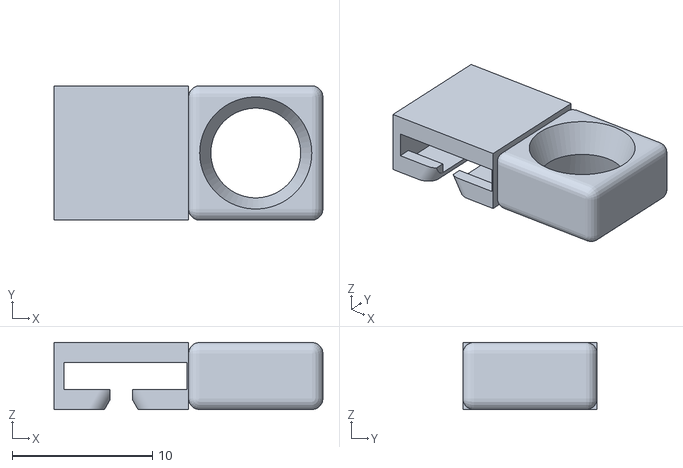
[picture p252: CAD file, 2024-01-14]
stl/electronic-parts/wire/wire-3-otherside.stl
19.2 x 9.60 x 4.80
