phiphi33/block/stl/electronic/sg90-2x2.stl

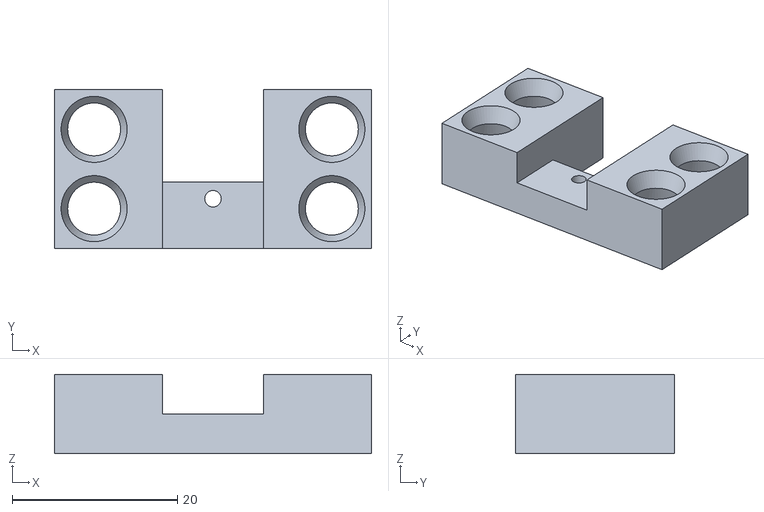
[picture p253: CAD file, 2020-05-04]
stl/electronic/sg90-2x2.stl
38.4 x 19.2 x 9.60
