phiphi33/block/dat/clips/clip-4a.stl

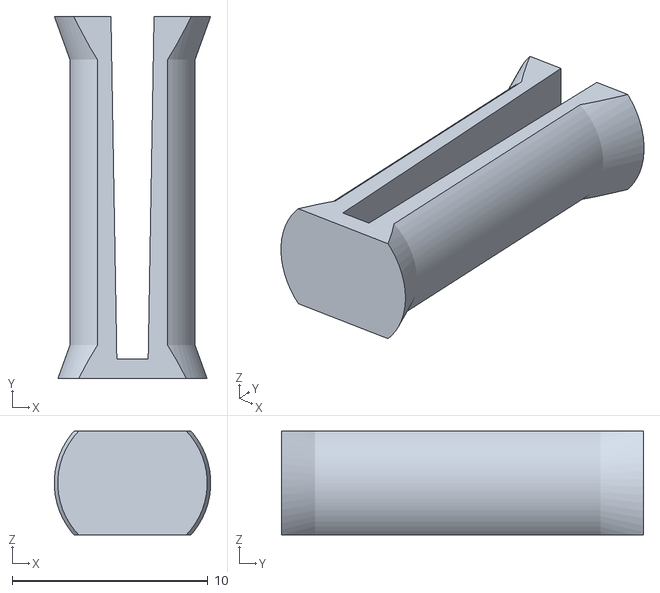
[picture p254: CAD file, 2022-05-13]
dat/clips/clip-4a.stl
7.99 x 18.5 x 5.30
