phiphi33/block/dat/other/other-dc-motor-gearbox.stl

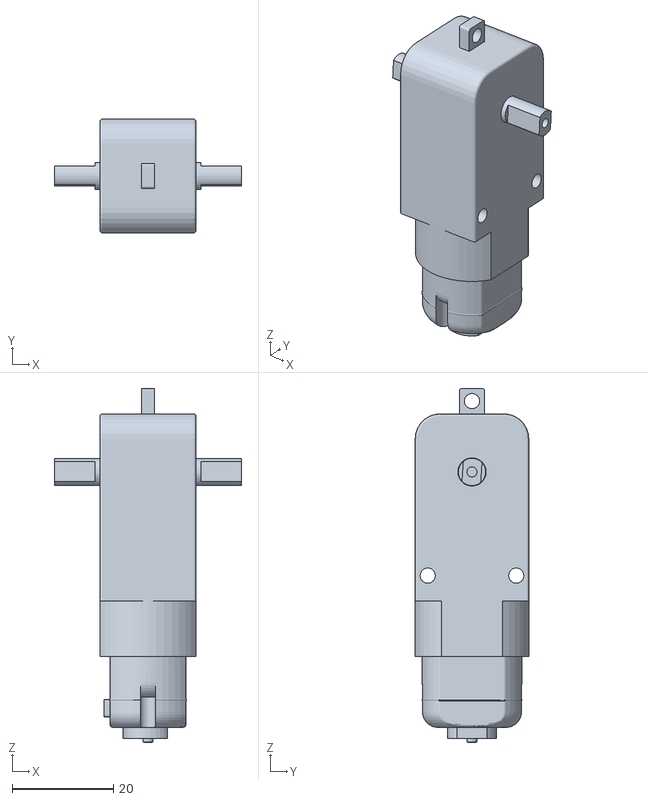
[picture p255: CAD file, 2022-05-13]
dat/other/other-dc-motor-gearbox.stl
37.0 x 22.5 x 70.0
