phiphi33/block/imports/nodemcu-generic.stl

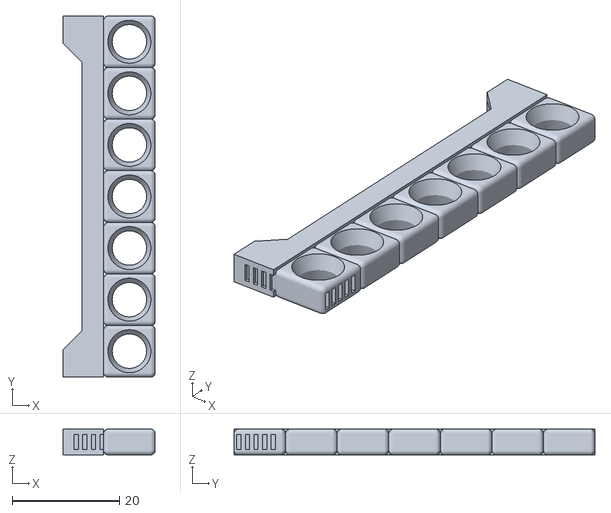
[picture p256: CAD file, 2024-01-11]
imports/nodemcu-generic.stl
17.2 x 67.2 x 4.80
