phiphi33/block/other/12.8/stl/basic-parts/C-3-1-1.stl

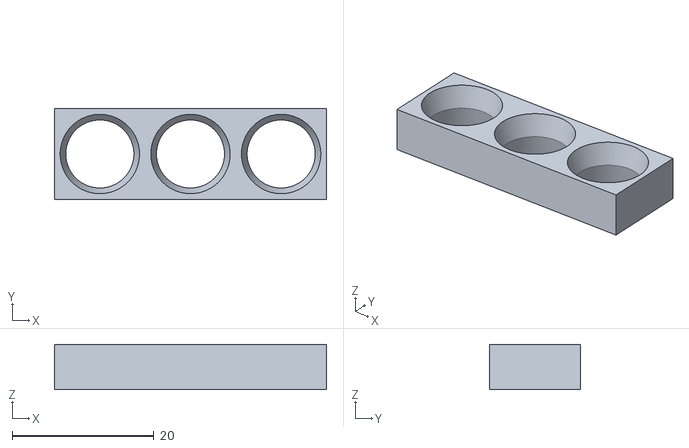
[picture p257: CAD file, 2020-06-02]
other/12.8/stl/basic-parts/C-3-1-1.stl
38.4 x 12.8 x 6.40
