phiphi33/block/other/12.8/stl/clips/clip-2-strong.stl

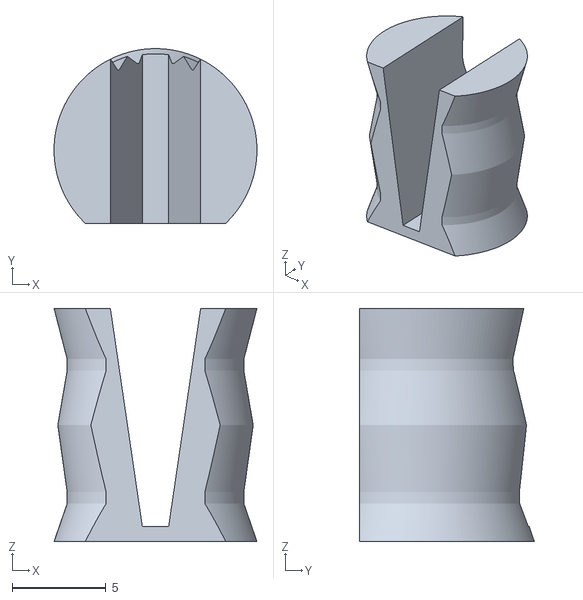
[picture p258: CAD file, 2020-06-02]
other/12.8/stl/clips/clip-2-strong.stl
10.8 x 9.30 x 12.4
