phiphi33/block/other/gears/stl/gears_helical-23.stl

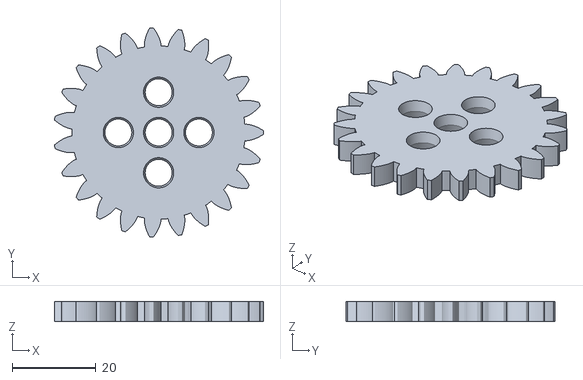
[picture p259: CAD file, 2023-11-19]
other/gears/stl/gears_helical-23.stl
49.8 x 49.9 x 4.80
