phiphi33/block/other/lego/stl/L3.stl

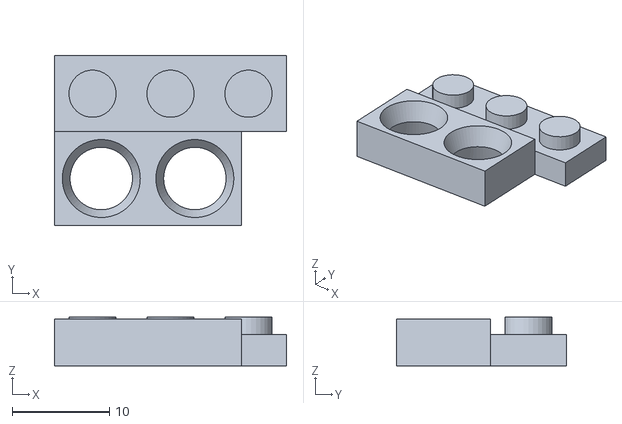
[picture p260: CAD file, 2022-05-13]
other/lego/stl/L3.stl
23.8 x 17.4 x 5.00
