phiphi33/block/other/spiralwheel/stl/SP75-soft-clip.stl

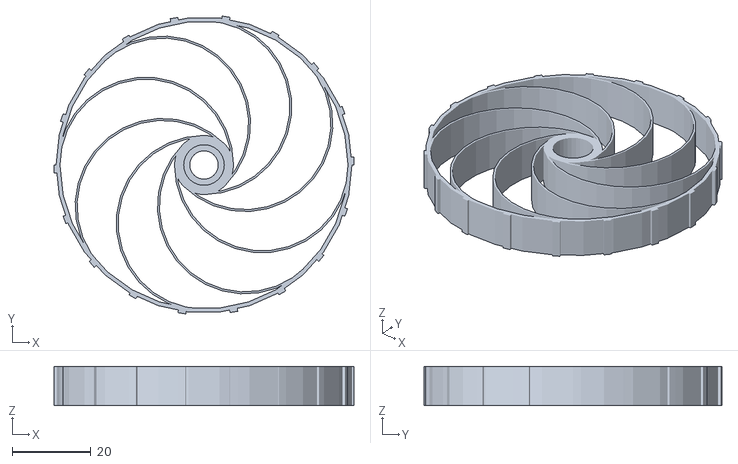
[picture p261: CAD file, 2024-02-18]
other/spiralwheel/stl/SP75-soft-clip.stl
76.0 x 75.5 x 10.0
