phiphi33/block/stl/clips/clip-3-M4.stl

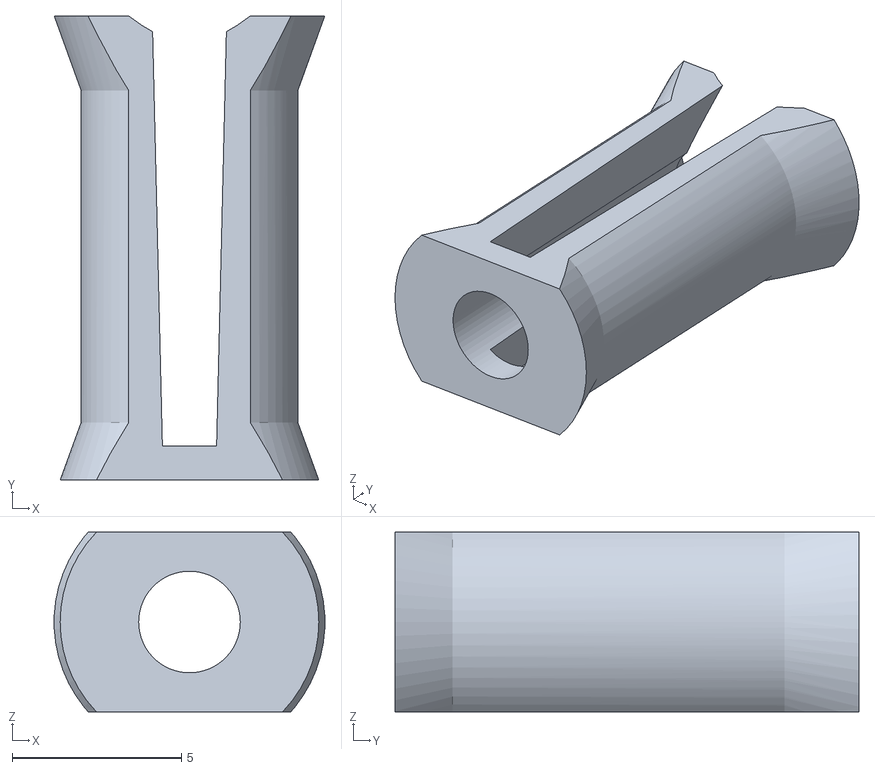
[picture p262: CAD file, 2024-01-07]
stl/clips/clip-3-M4.stl
7.99 x 13.7 x 5.30
