phiphi33/block/stl/electronic-parts/battery-shield/battery-shield-usb-1.stl

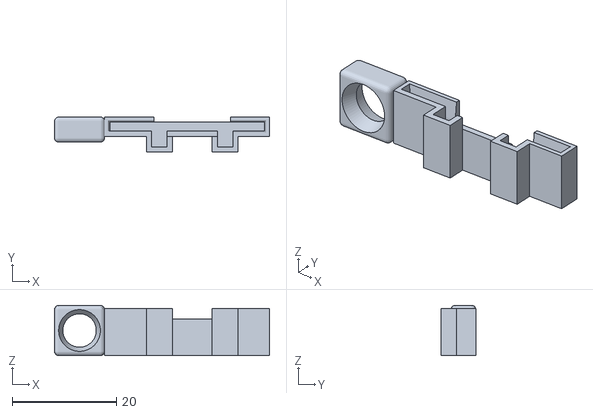
[picture p263: CAD file, 2024-01-14]
stl/electronic-parts/battery-shield/battery-shield-usb-1.stl
41.2 x 6.70 x 9.60
