phiphi33/block/stl/electronic-parts/D1-mini/D1-mini.stl

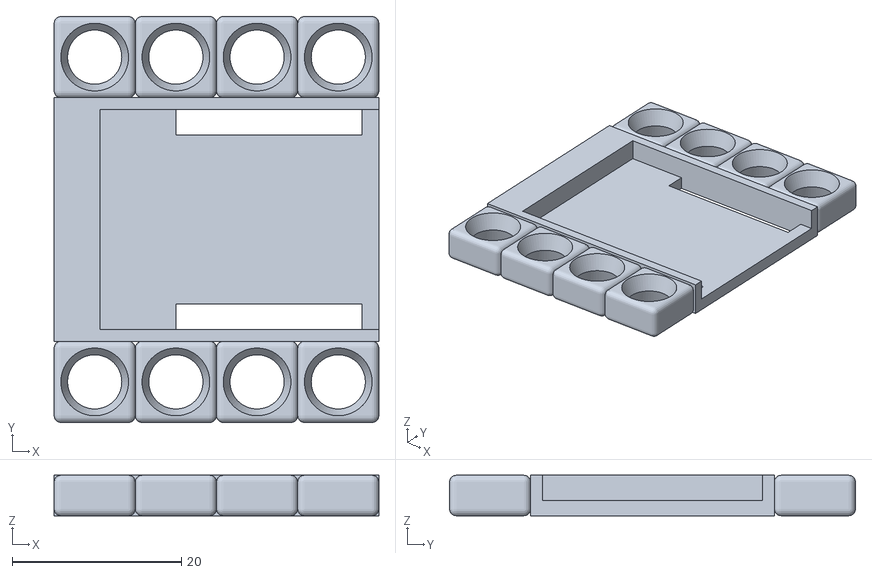
[picture p265: CAD file, 2024-01-14]
stl/electronic-parts/D1-mini/D1-mini.stl
38.4 x 48.0 x 4.80
