phiphi33/block/stl/electronic-parts/dupont/dupontx2.stl

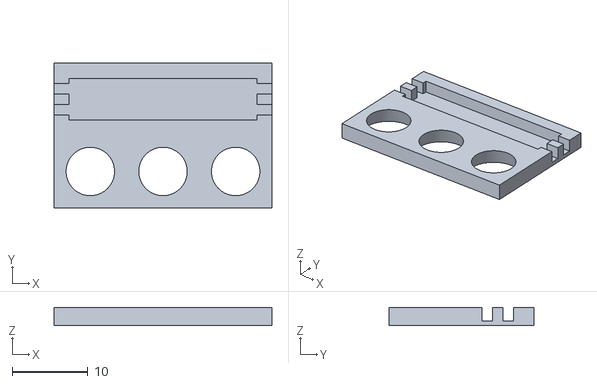
[picture p266: CAD file, 2020-05-10]
stl/electronic-parts/dupont/dupontx2.stl
28.8 x 19.1 x 2.40
