phiphi33/block/stl/electronic-parts/nodemcu/nodemcu-top-2side.stl

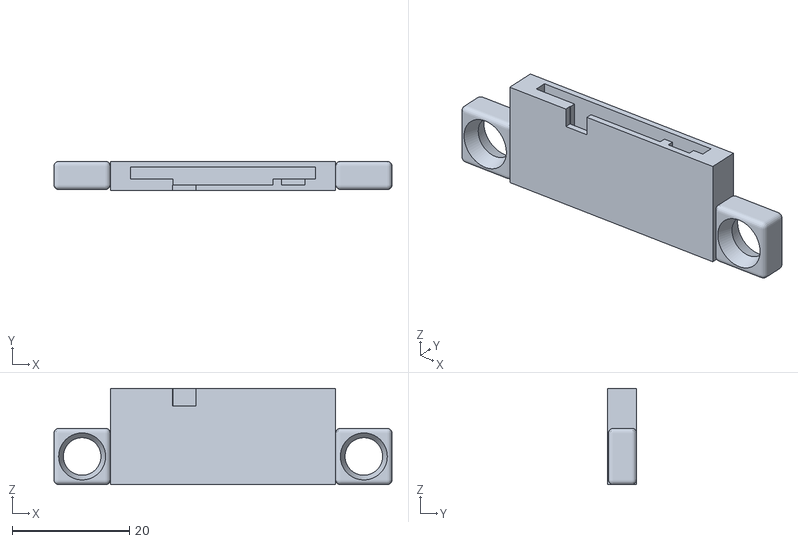
[picture p267: CAD file, 2024-01-14]
stl/electronic-parts/nodemcu/nodemcu-top-2side.stl
57.6 x 5.00 x 16.4
