phiphi33/block/stl/electronic-parts/sg90/sg90-helix-2.stl

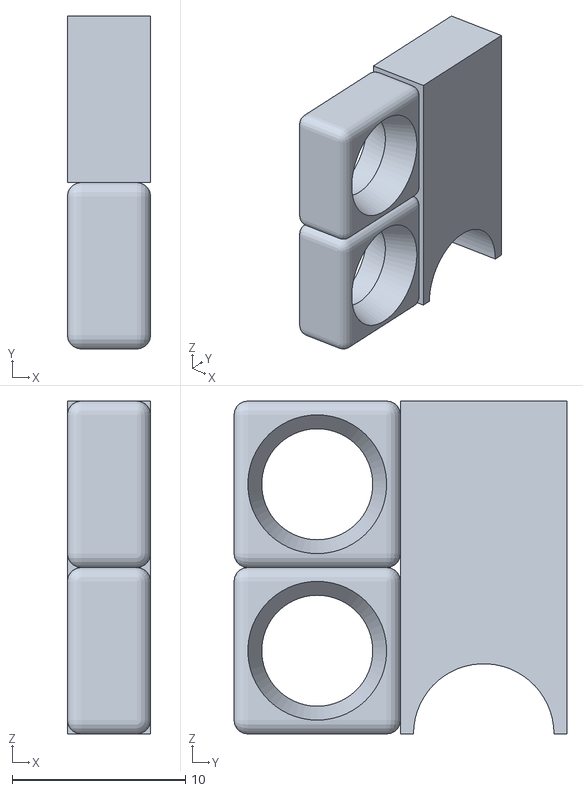
[picture p269: CAD file, 2024-01-14]
stl/electronic-parts/sg90/sg90-helix-2.stl
4.80 x 19.2 x 19.2
