phiphi33/block/dat/other/other-sg90.stl

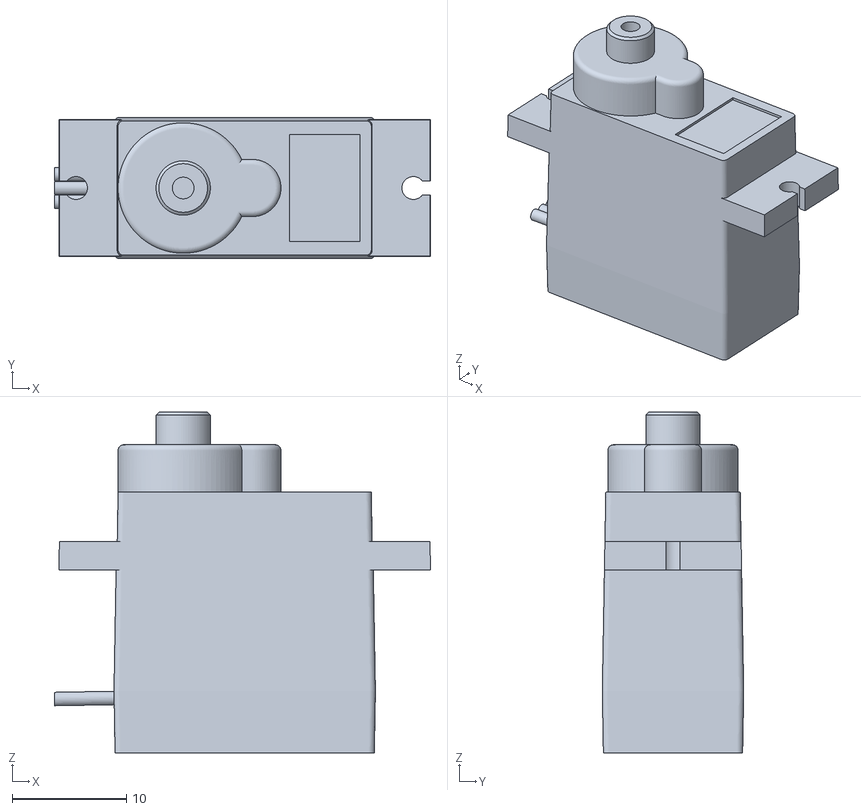
[picture p270: CAD file, 2022-05-13]
dat/other/other-sg90.stl
32.9 x 12.4 x 29.8
