phiphi33/block/imports/hole-cube-rounded.stl

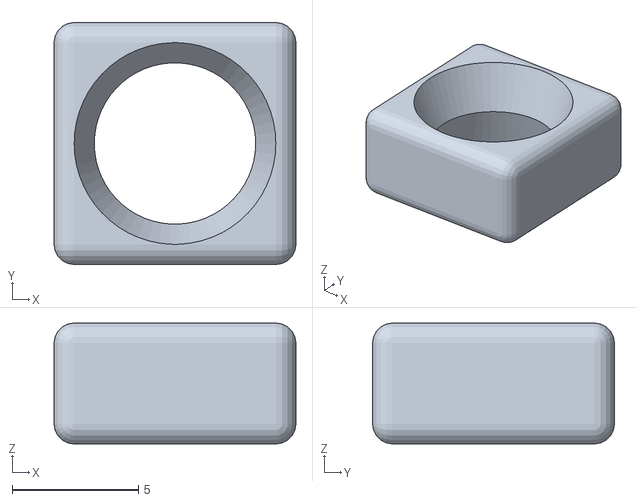
[picture p271: CAD file, 2024-01-11]
imports/hole-cube-rounded.stl
9.60 x 9.60 x 4.80
