phiphi33/block/other/12.8/stl/clips/clip-2.stl

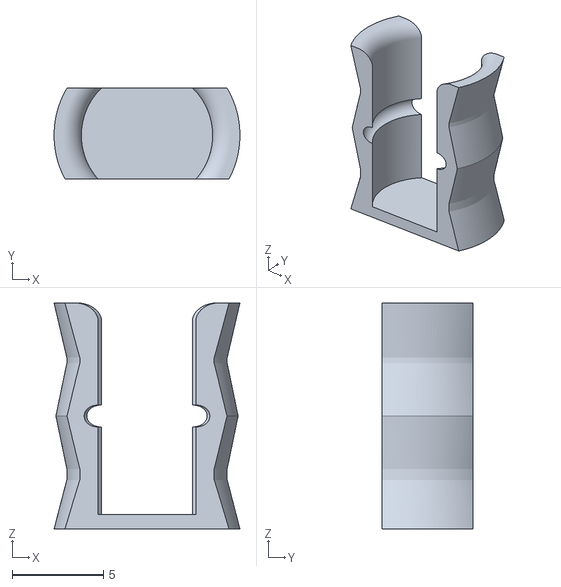
[picture p272: CAD file, 2020-06-02]
other/12.8/stl/clips/clip-2.stl
10.2 x 5.00 x 12.4
