phiphi33/block/other/gears/stl/gears_helical-33.stl

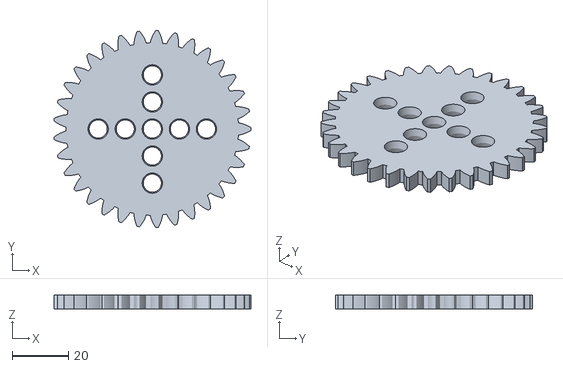
[picture p273: CAD file, 2023-11-19]
other/gears/stl/gears_helical-33.stl
69.9 x 70.0 x 4.80
