phiphi33/block/other/lego/stl/L7.stl

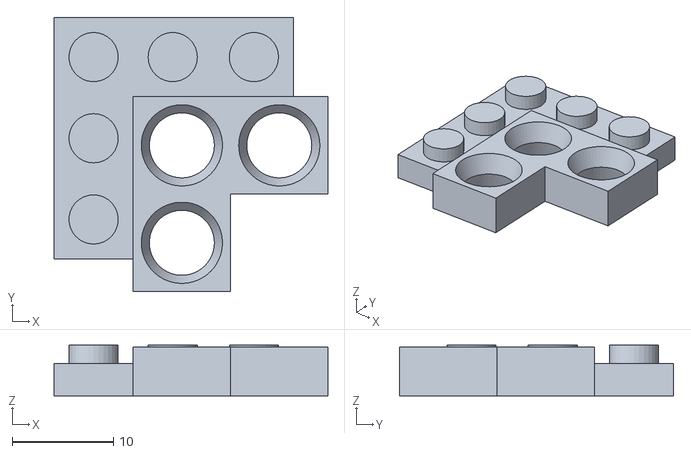
[picture p274: CAD file, 2022-05-13]
other/lego/stl/L7.stl
27.0 x 27.0 x 5.00
