phiphi33/block/stl/basic-parts/L-1-1-3.stl

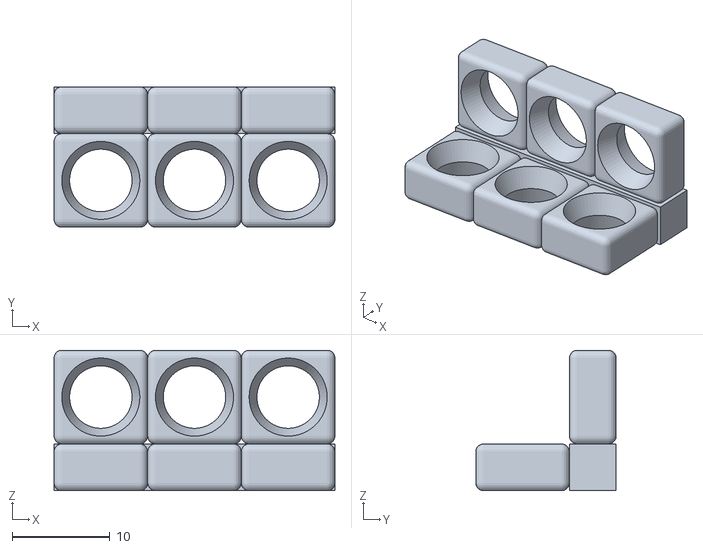
[picture p275: CAD file, 2024-01-11]
stl/basic-parts/L-1-1-3.stl
28.8 x 14.4 x 14.4
