phiphi33/block/stl/clips/clip-4-M4.stl

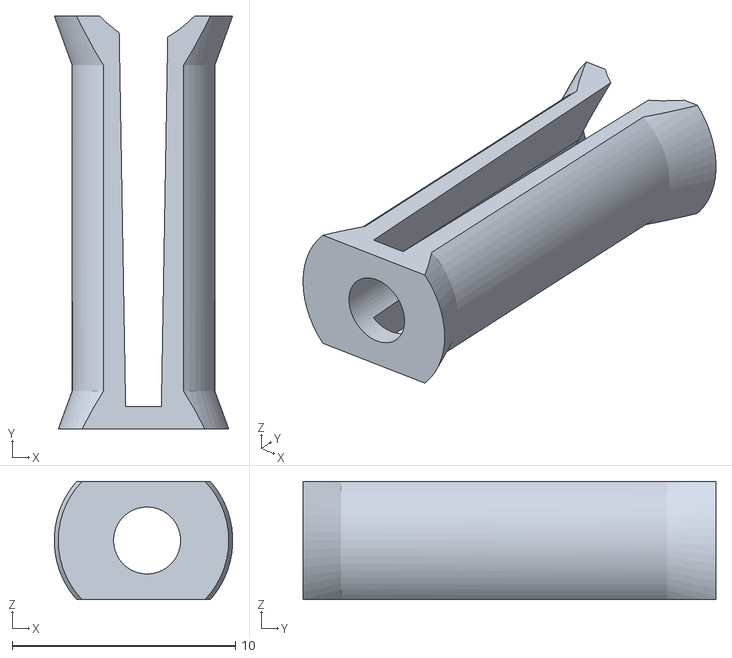
[picture p276: CAD file, 2024-01-07]
stl/clips/clip-4-M4.stl
7.99 x 18.5 x 5.30
