phiphi33/block/stl/electronic-parts/battery-shield/battery-shield-usb-2.3mf

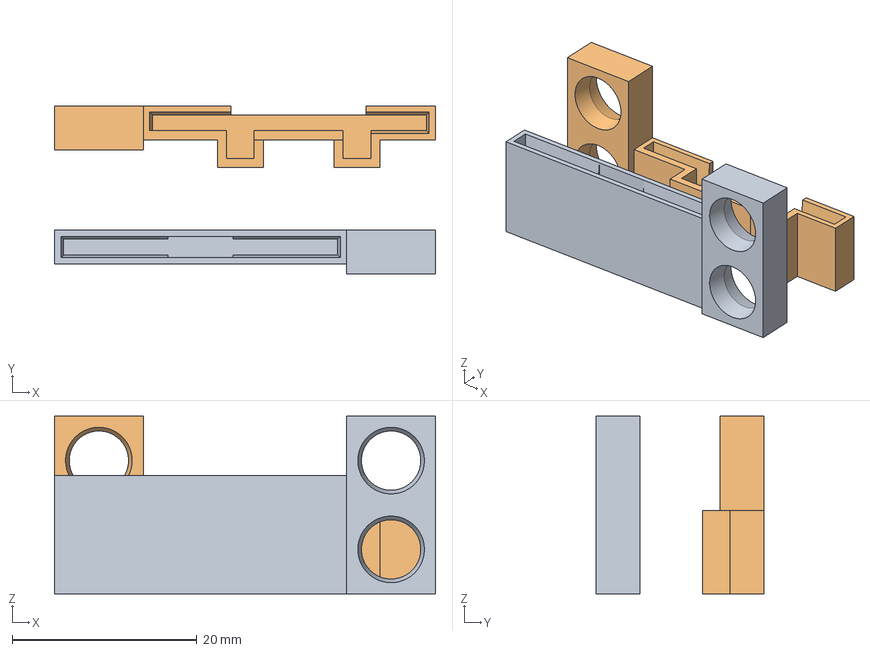
[picture p277: CAD file, 2023-08-28]
stl/electronic-parts/battery-shield/battery-shield-usb-2.3mf
41.2 x 18.2 x 19.2 mm
battery-shield-bottom-2.stl
battery-shield-usb-2.stl
