phiphi33/block/stl/electronic-parts/button14x20/button14x20-half-bottomx2-2side.stl

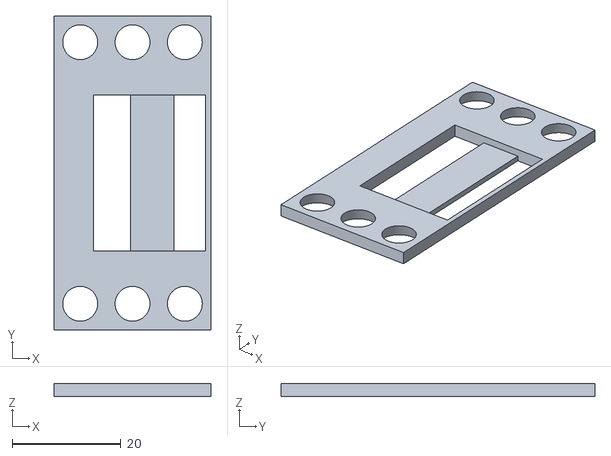
[picture p278: CAD file, 2022-05-13]
stl/electronic-parts/button14x20/button14x20-half-bottomx2-2side.stl
28.8 x 57.6 x 2.40
