phiphi33/block/stl/electronic-parts/D1-mini/D1-mini-generic.stl

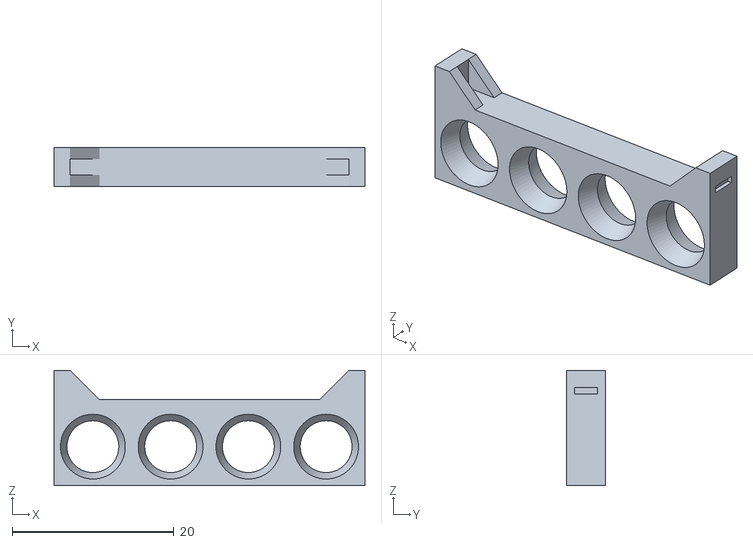
[picture p279: CAD file, 2024-01-14]
stl/electronic-parts/D1-mini/D1-mini-generic.stl
38.4 x 4.80 x 14.2
