phiphi33/block/stl/electronic-parts/nodemcu/nodemcu-top-small.stl

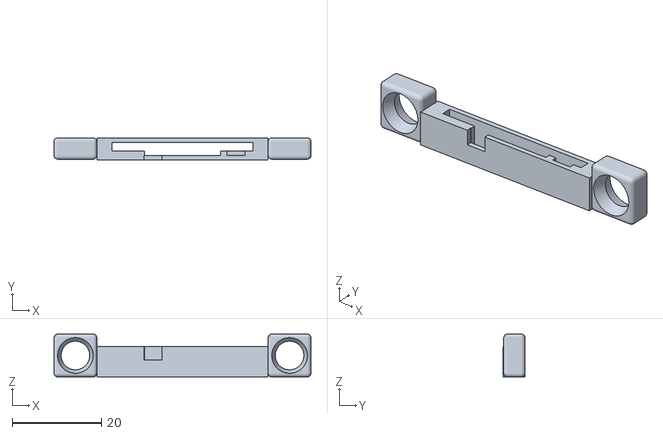
[picture p280: CAD file, 2024-01-14]
stl/electronic-parts/nodemcu/nodemcu-top-small.stl
57.6 x 5.00 x 9.60
