phiphi33/block/stl/electronic-parts/oled-128x64/oled-128x64-top-2side.stl

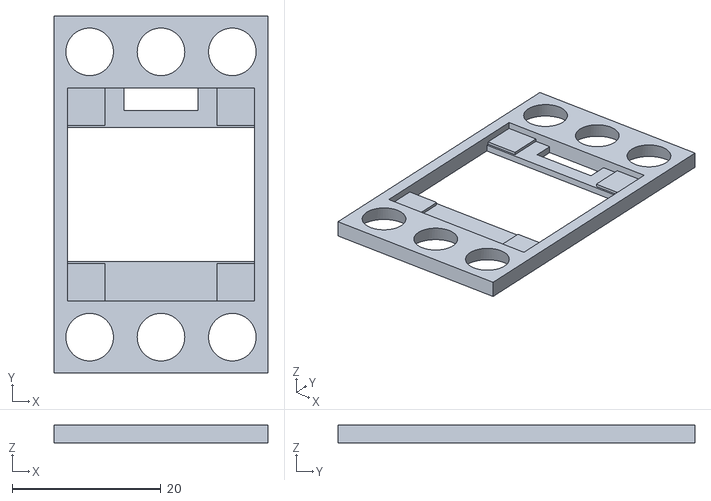
[picture p281: CAD file, 2019-08-03]
stl/electronic-parts/oled-128x64/oled-128x64-top-2side.stl
28.8 x 48.0 x 2.40
