phiphi33/block/stl/electronic-parts/sg90/direction-center.stl

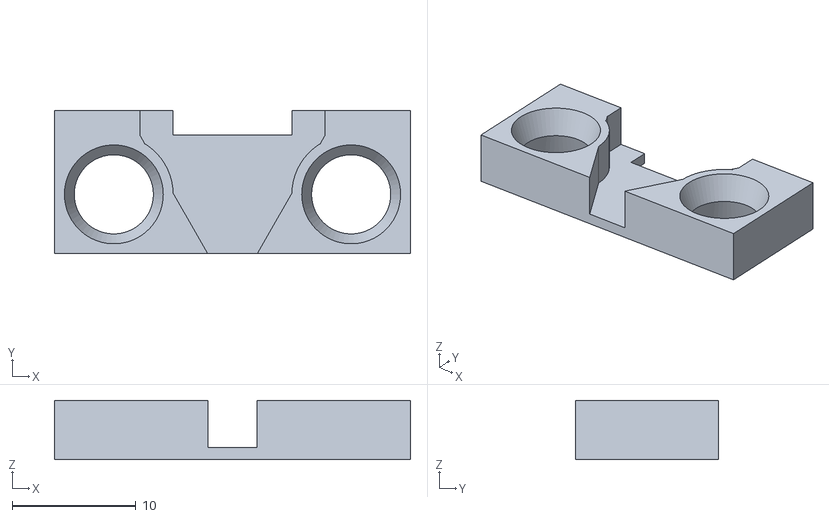
[picture p282: CAD file, 2019-08-28]
stl/electronic-parts/sg90/direction-center.stl
28.8 x 11.6 x 4.80
