phiphi33/block/stl/electronic/sg90-3x1-1side.stl

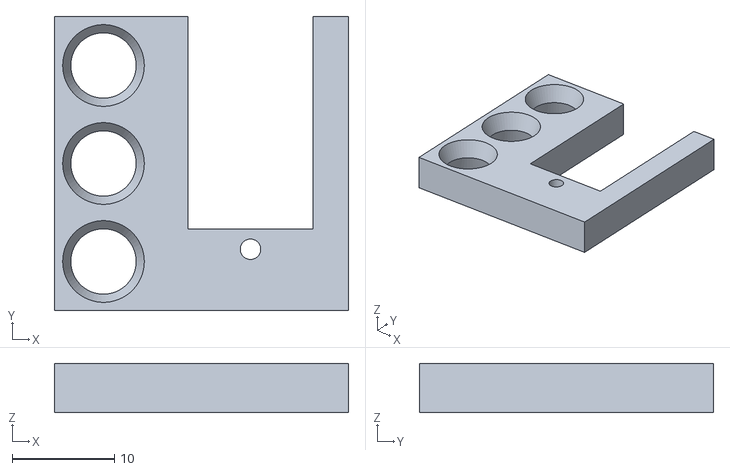
[picture p283: CAD file, 2020-05-04]
stl/electronic/sg90-3x1-1side.stl
28.8 x 28.8 x 4.80
