phiphi33/block/other/12.8/stl/clips/blocker-2.stl

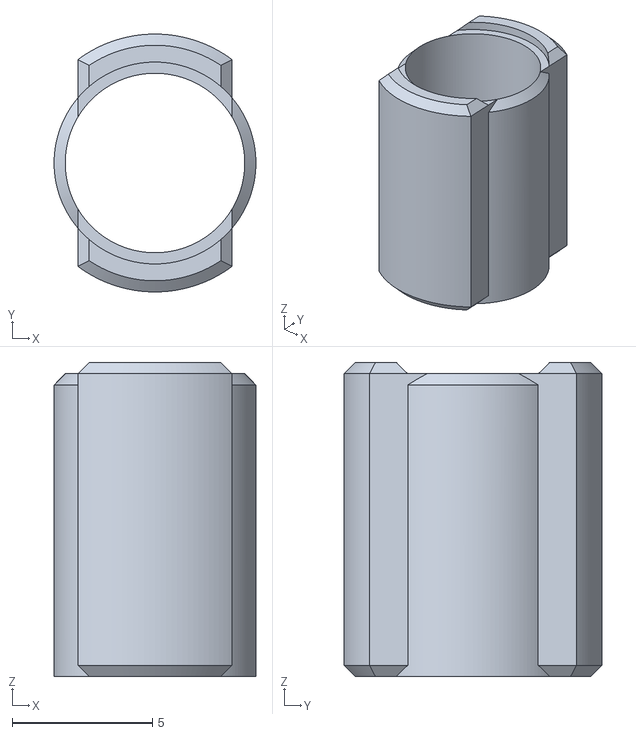
[picture p284: CAD file, 2020-06-02]
other/12.8/stl/clips/blocker-2.stl
7.20 x 9.20 x 11.2
