phiphi33/block/other/gears/stl/gears_helical-33-14.stl

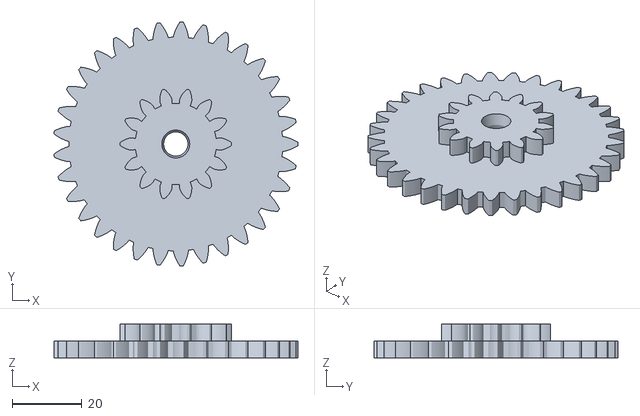
[picture p285: CAD file, 2023-11-19]
other/gears/stl/gears_helical-33-14.stl
69.9 x 70.0 x 9.60
