phiphi33/block/other/lego/stl/L2.stl

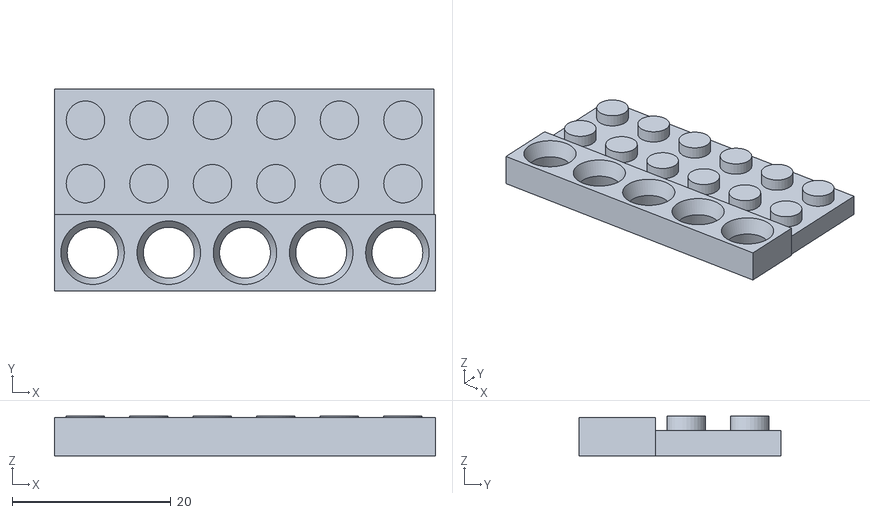
[picture p286: CAD file, 2022-05-13]
other/lego/stl/L2.stl
48.0 x 25.4 x 5.00
