phiphi33/block/other/spiralwheel/stl/SP75-medium-sg90.stl

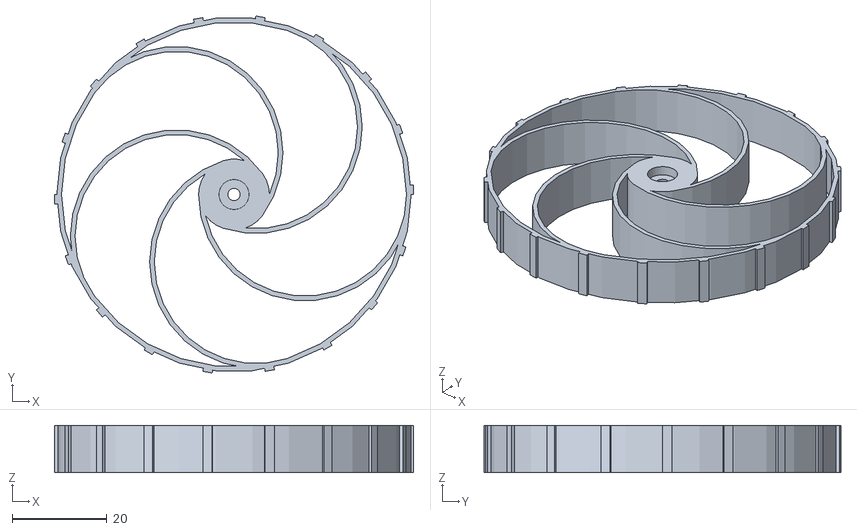
[picture p287: CAD file, 2024-02-18]
other/spiralwheel/stl/SP75-medium-sg90.stl
76.0 x 75.5 x 10.0
