phiphi33/block/stl/basic-parts/LF-2-2.stl

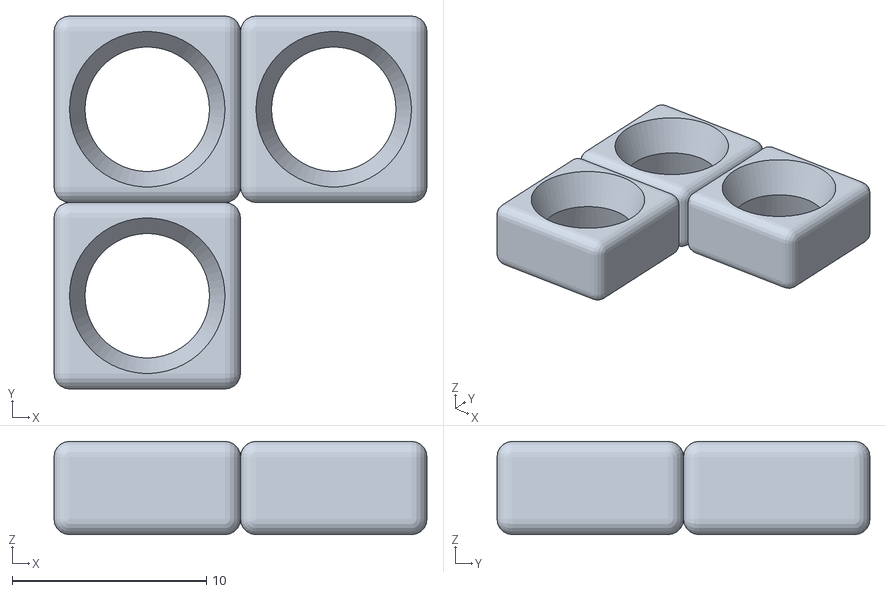
[picture p288: CAD file, 2024-01-11]
stl/basic-parts/LF-2-2.stl
19.2 x 19.2 x 4.80
