phiphi33/block/stl/electronic-parts/D1-mini/D1-mini-small.stl

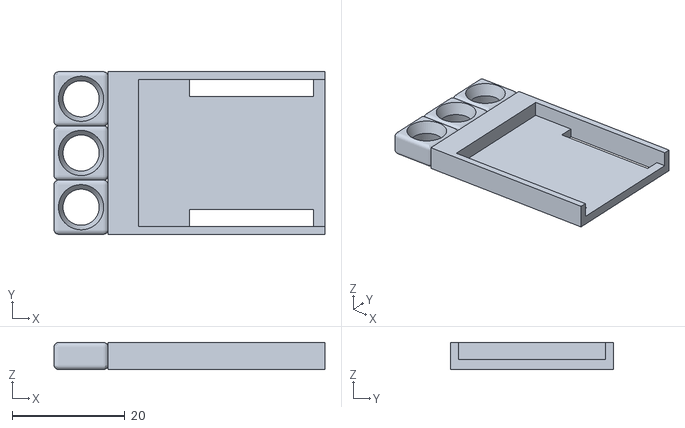
[picture p290: CAD file, 2024-01-14]
stl/electronic-parts/D1-mini/D1-mini-small.stl
48.0 x 28.8 x 4.80
