phiphi33/block/stl/electronic-parts/nodemcu/nodemcu-bottom-2side.stl

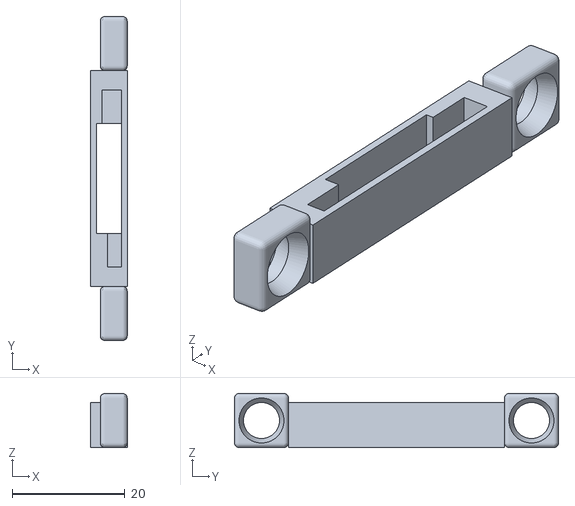
[picture p291: CAD file, 2024-01-14]
stl/electronic-parts/nodemcu/nodemcu-bottom-2side.stl
6.50 x 57.6 x 9.60
