phiphi33/block/stl/electronic-parts/tm1637/tm1637-top.stl

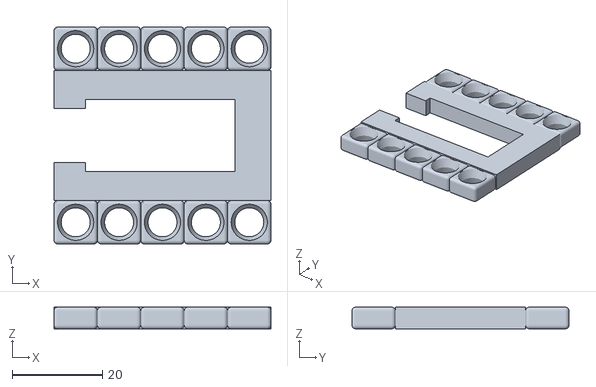
[picture p293: CAD file, 2024-01-14]
stl/electronic-parts/tm1637/tm1637-top.stl
48.0 x 48.0 x 4.80
