phiphi33/block/stl/electronic-parts/wire/wire-6.stl

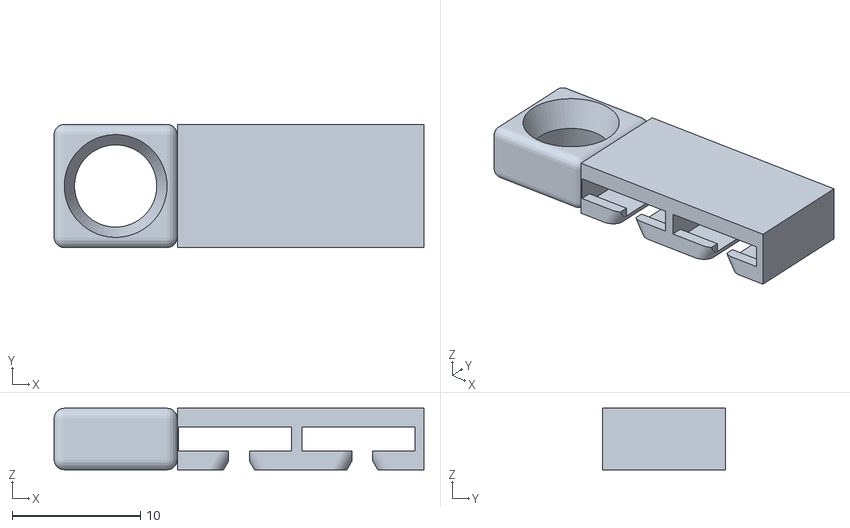
[picture p294: CAD file, 2024-01-14]
stl/electronic-parts/wire/wire-6.stl
28.8 x 9.60 x 4.80
