phiphi33/block/stl/electronic/sg90-2x1-front.stl

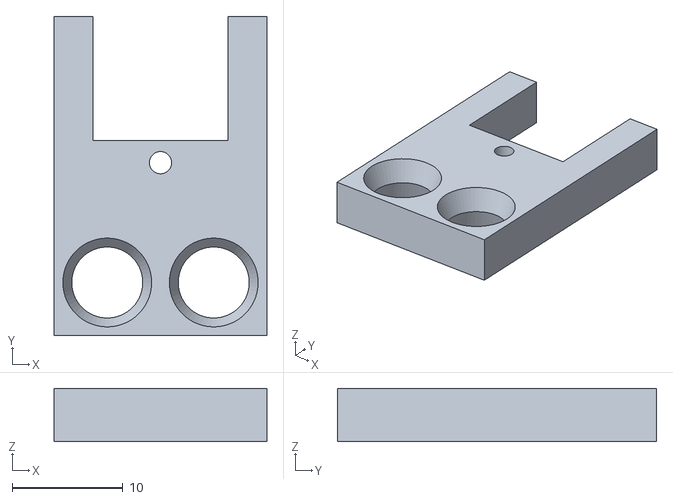
[picture p295: CAD file, 2020-05-04]
stl/electronic/sg90-2x1-front.stl
19.2 x 28.8 x 4.80
