phiphi33/block/other/gears/stl/gears_helical-24.stl

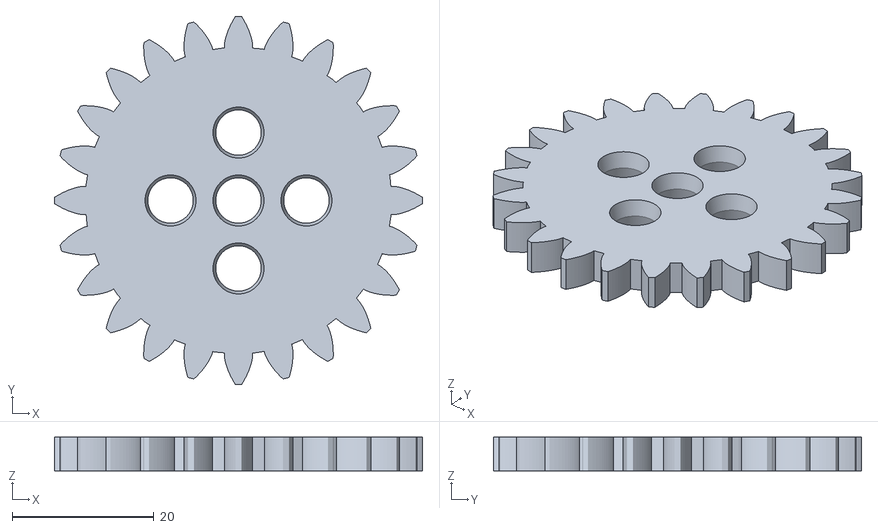
[picture p296: CAD file, 2023-11-19]
other/gears/stl/gears_helical-24.stl
52.0 x 52.0 x 4.80
