phiphi33/block/other/lego/stl/L5.stl

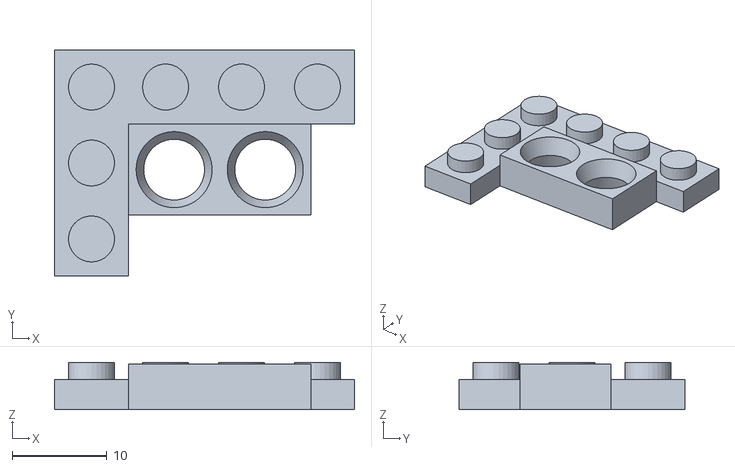
[picture p297: CAD file, 2022-05-13]
other/lego/stl/L5.stl
31.6 x 23.8 x 5.00
