phiphi33/block/other/spiralwheel/stl/SP45-hard-sg90.stl

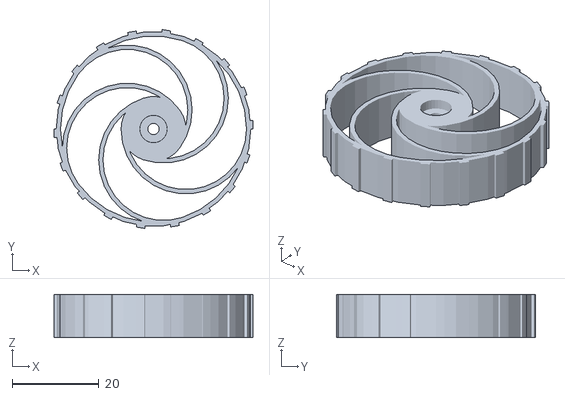
[picture p298: CAD file, 2024-02-18]
other/spiralwheel/stl/SP45-hard-sg90.stl
46.0 x 46.0 x 10.0
