phiphi33/block/stl/basic-parts/I-4.stl

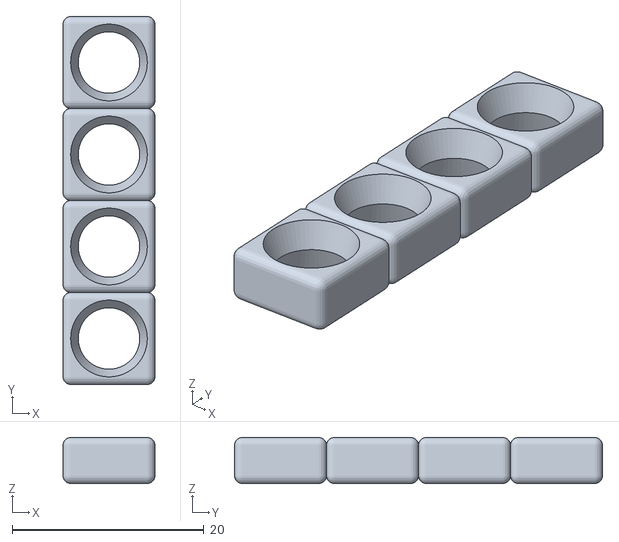
[picture p299: CAD file, 2024-01-11]
stl/basic-parts/I-4.stl
9.60 x 38.4 x 4.80
