phiphi33/block/stl/clips/clip-2.stl

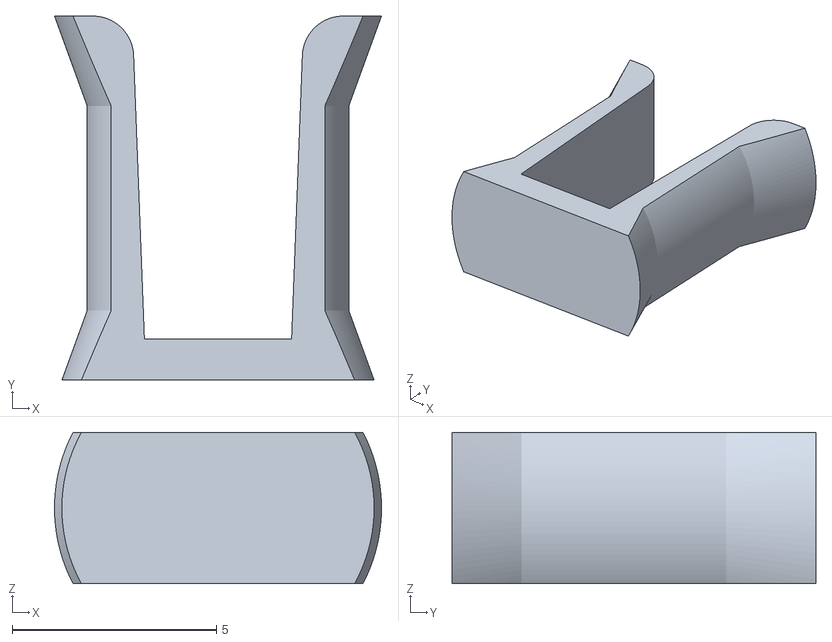
[picture p300: CAD file, 2020-06-02]
stl/clips/clip-2.stl
8.00 x 8.90 x 3.70
