phiphi33/block/stl/electronic-parts/button14x20/button14x20-top-2side.stl

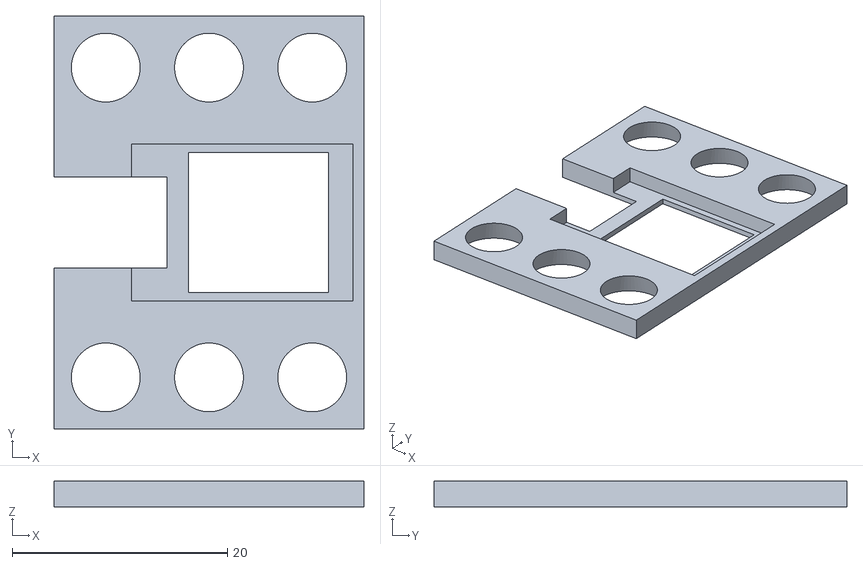
[picture p301: CAD file, 2019-08-03]
stl/electronic-parts/button14x20/button14x20-top-2side.stl
28.8 x 38.4 x 2.40
