phiphi33/block/stl/electronic-parts/nodemcu/nodemcu-bottom-2.stl

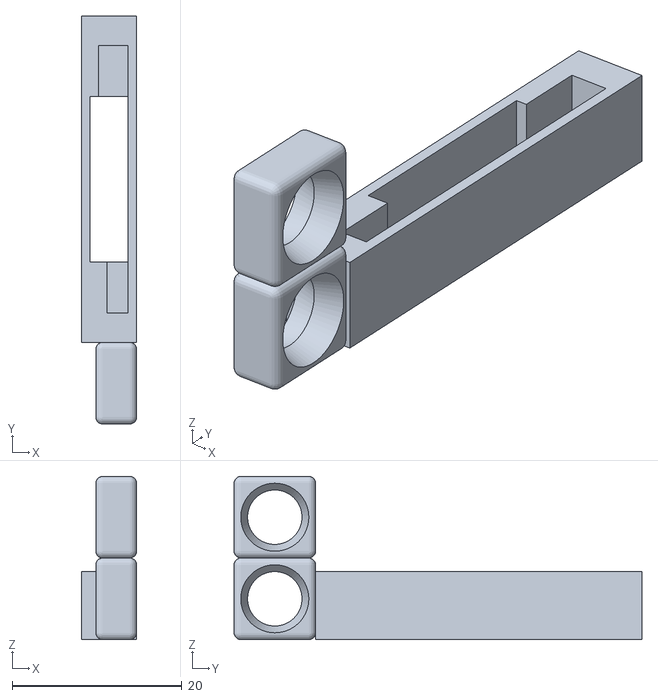
[picture p302: CAD file, 2024-01-14]
stl/electronic-parts/nodemcu/nodemcu-bottom-2.stl
6.50 x 48.0 x 19.2
