phiphi33/block/stl/electronic-parts/oled-128x64/oled-128x64-top-1side.stl

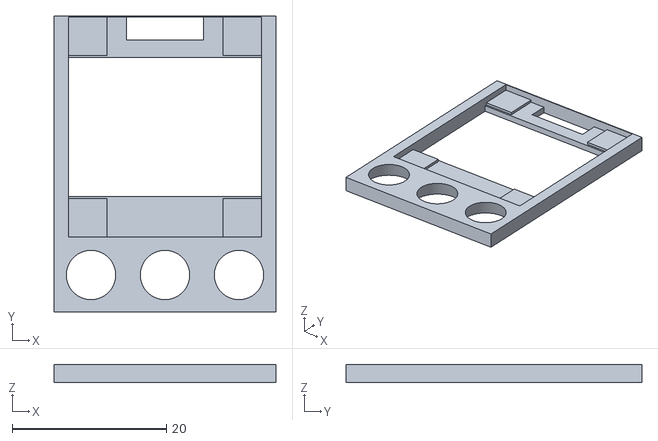
[picture p303: CAD file, 2019-08-03]
stl/electronic-parts/oled-128x64/oled-128x64-top-1side.stl
28.8 x 38.4 x 2.40
