phiphi33/block/stl/electronic-parts/wire/wire-6-2side.stl

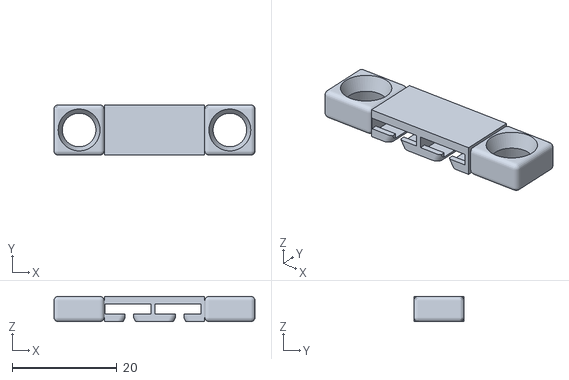
[picture p304: CAD file, 2024-01-14]
stl/electronic-parts/wire/wire-6-2side.stl
38.4 x 9.60 x 4.80
