phiphi33/block/stl/electronic/sg90-4x1-front.stl

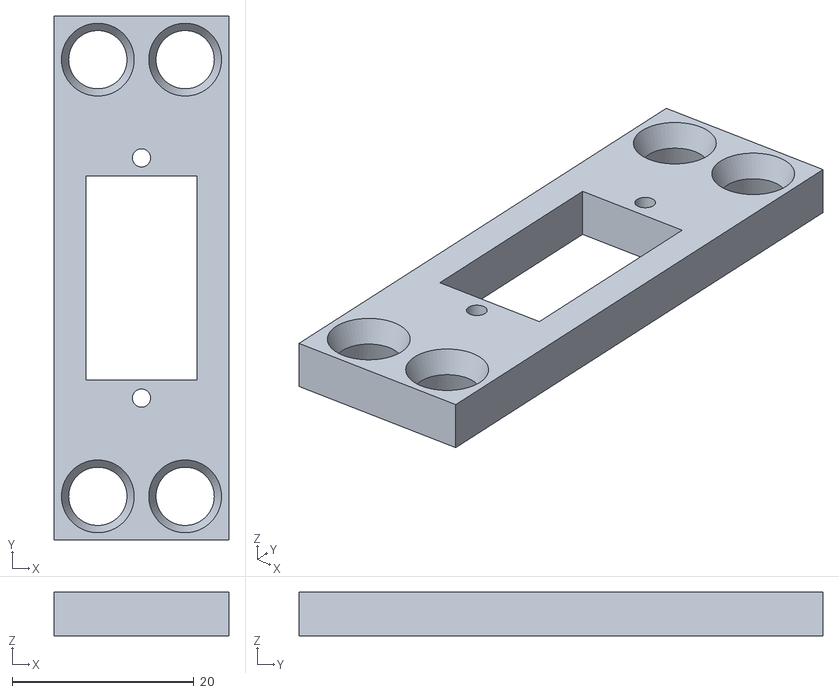
[picture p305: CAD file, 2020-05-04]
stl/electronic/sg90-4x1-front.stl
19.2 x 57.6 x 4.80
