phiphi33/block/other/gears/stl/gears_helical-14.stl

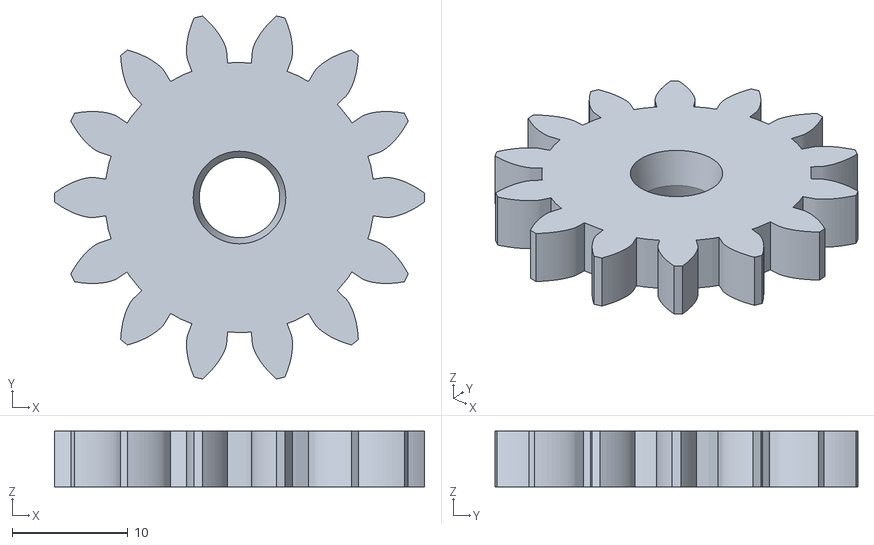
[picture p306: CAD file, 2023-11-19]
other/gears/stl/gears_helical-14.stl
32.0 x 31.4 x 4.80
