phiphi33/block/other/lego/stl/L1.stl

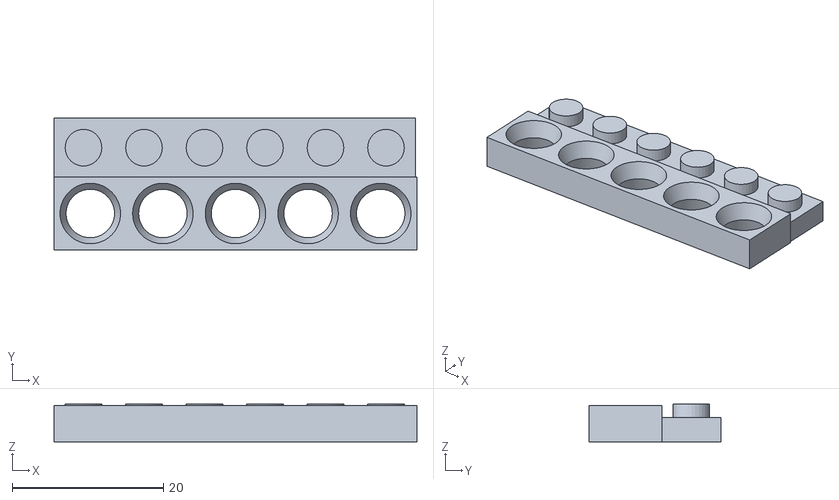
[picture p307: CAD file, 2022-05-13]
other/lego/stl/L1.stl
48.0 x 17.4 x 5.00
