phiphi33/block/other/spiralwheel/stl/test-clip.stl

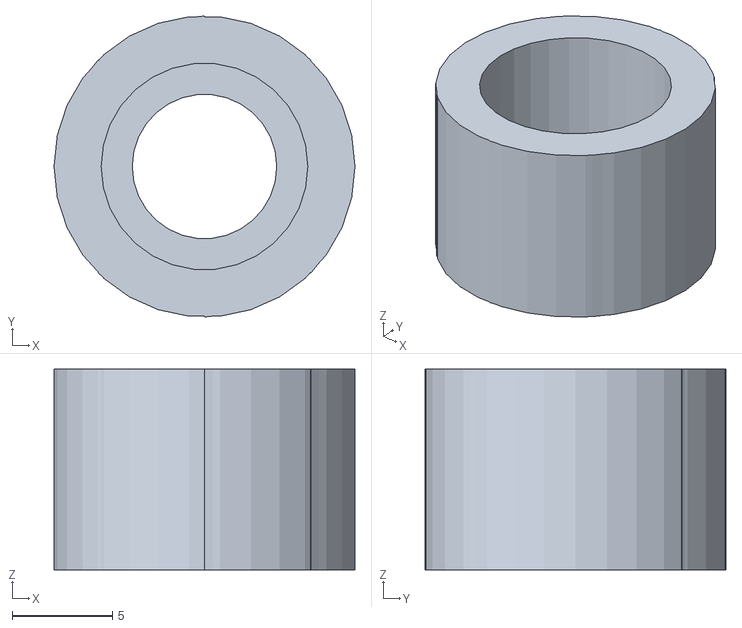
[picture p308: CAD file, 2024-02-18]
other/spiralwheel/stl/test-clip.stl
15.0 x 15.0 x 10.0
