phiphi33/block/stl/basic-parts/LF-4-4.stl

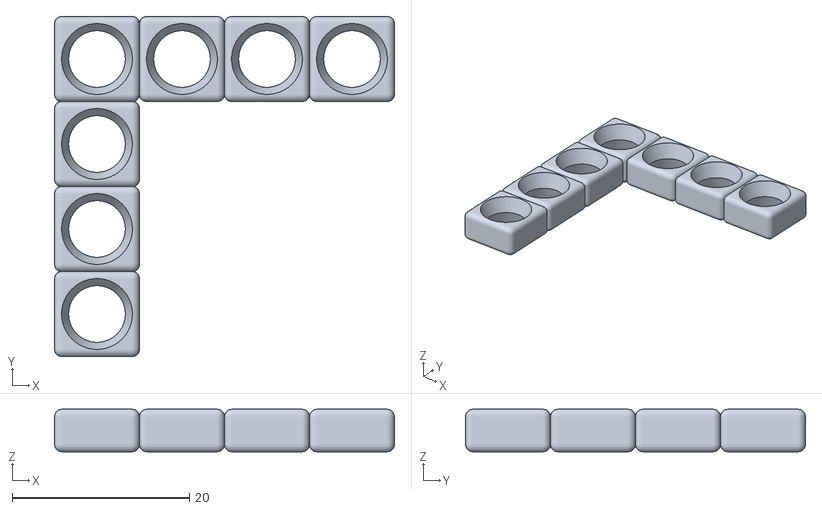
[picture p309: CAD file, 2024-01-11]
stl/basic-parts/LF-4-4.stl
38.4 x 38.4 x 4.80
