phiphi33/block/stl/clips/blocker-3-easy.stl

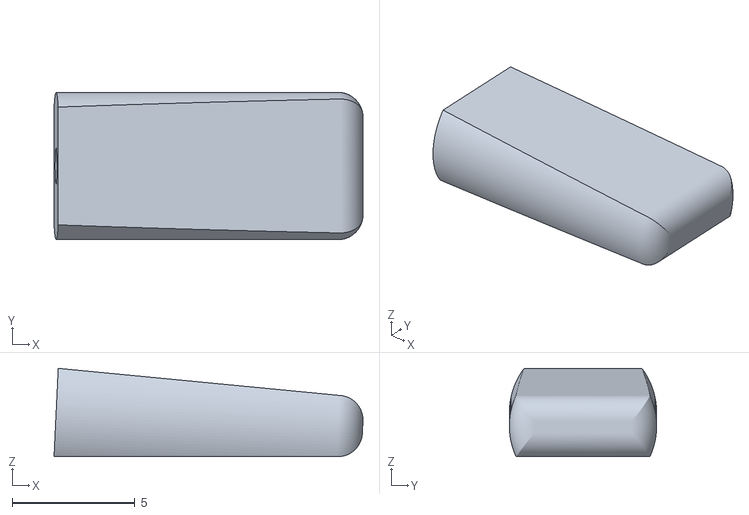
[picture p310: CAD file, 2020-06-02]
stl/clips/blocker-3-easy.stl
12.6 x 6.00 x 3.60
