phiphi33/block/stl/electronic-parts/button14x20/button14x20-top-small.stl

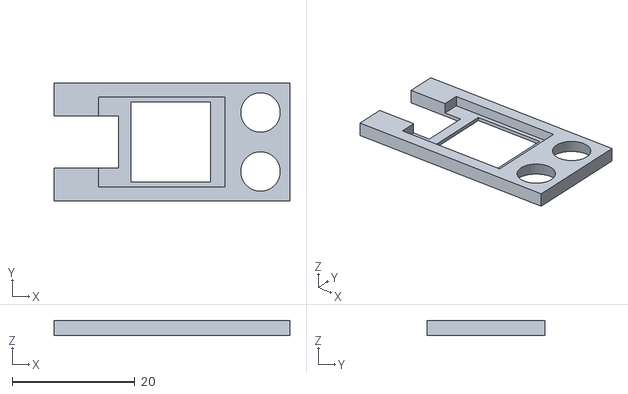
[picture p311: CAD file, 2019-08-03]
stl/electronic-parts/button14x20/button14x20-top-small.stl
38.4 x 19.2 x 2.40
