phiphi33/block/imports/sg90-helix.stl

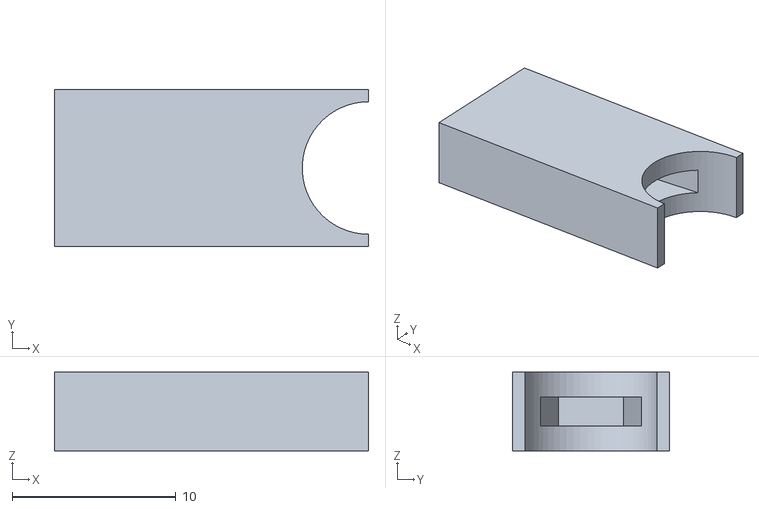
[picture p312: CAD file, 2023-09-15]
imports/sg90-helix.stl
19.2 x 9.60 x 4.80
