phiphi33/block/other/gears/stl/gears_helical-9.stl

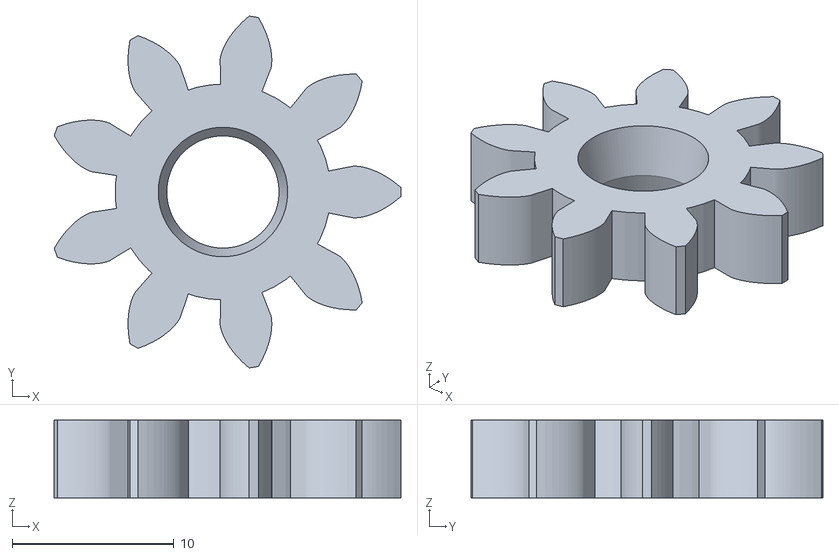
[picture p313: CAD file, 2023-11-19]
other/gears/stl/gears_helical-9.stl
21.4 x 21.8 x 4.80
