phiphi33/block/other/spiralwheel/stl/SP65-hard-dc-gearbox.stl

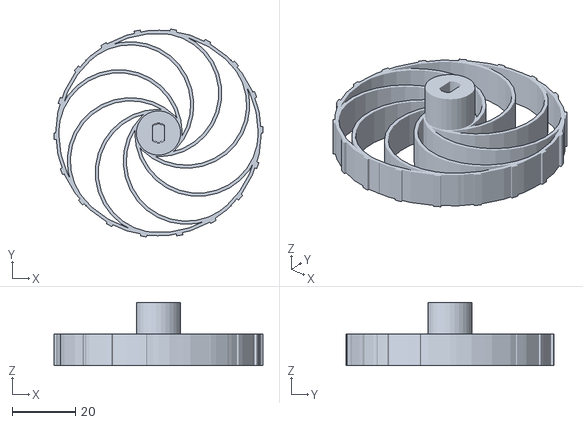
[picture p314: CAD file, 2024-02-18]
other/spiralwheel/stl/SP65-hard-dc-gearbox.stl
66.0 x 65.7 x 20.0
