phiphi33/block/stl/basic-parts/C-2-2-2.stl

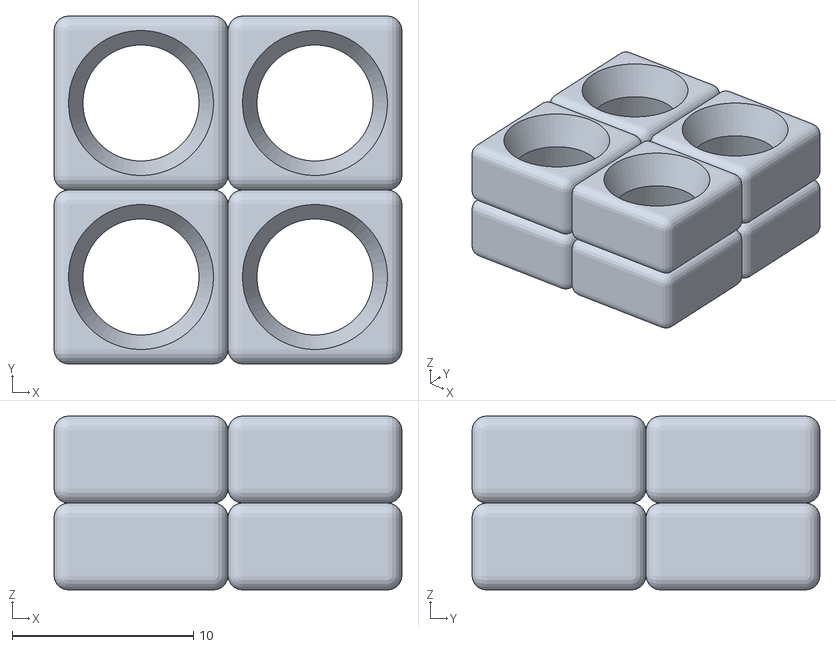
[picture p315: CAD file, 2024-01-11]
stl/basic-parts/C-2-2-2.stl
19.2 x 19.2 x 9.60
