phiphi33/block/stl/clips/blocker-4.stl

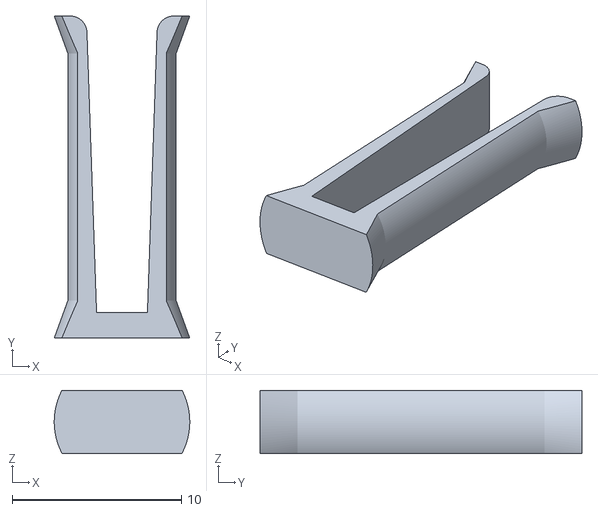
[picture p316: CAD file, 2020-06-02]
stl/clips/blocker-4.stl
8.00 x 19.0 x 3.73
