phiphi33/block/stl/electronic-parts/button14x20/button14x20-top-1side.stl

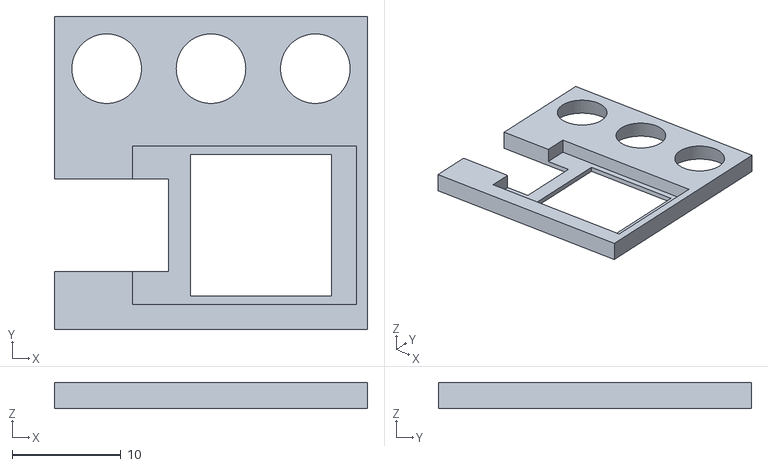
[picture p317: CAD file, 2019-08-03]
stl/electronic-parts/button14x20/button14x20-top-1side.stl
28.8 x 28.8 x 2.40
