phiphi33/block/stl/electronic-parts/nodemcu/nodemcu-top-1side2.stl

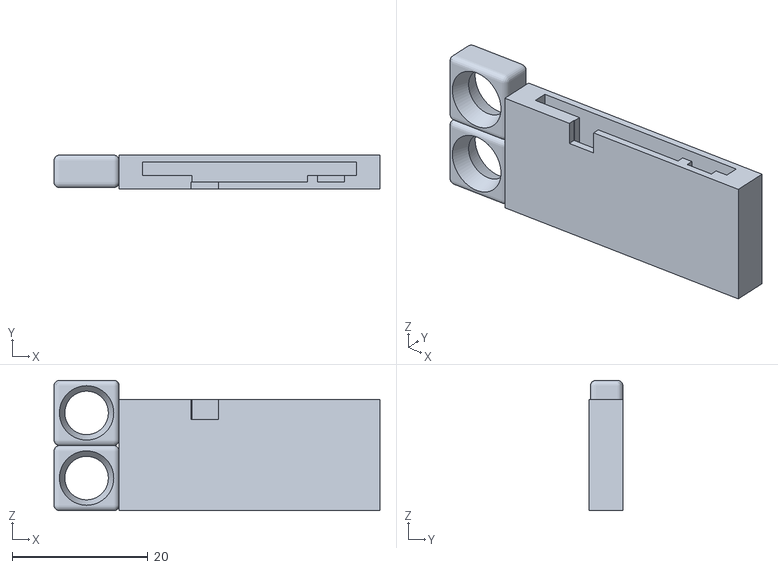
[picture p318: CAD file, 2024-01-14]
stl/electronic-parts/nodemcu/nodemcu-top-1side2.stl
48.0 x 5.00 x 19.2
