phiphi33/block/stl/electronic-parts/wire/wire-3H-strong.stl

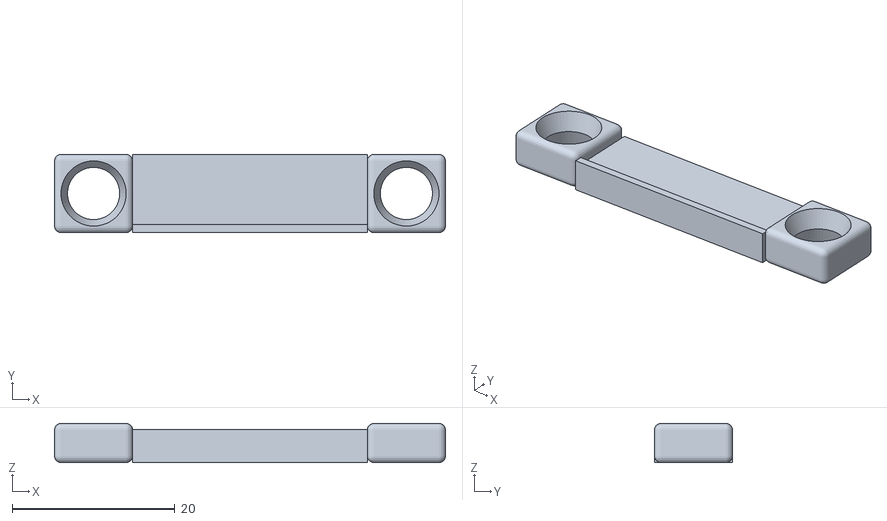
[picture p319: CAD file, 2024-01-14]
stl/electronic-parts/wire/wire-3H-strong.stl
48.0 x 9.60 x 4.80
