phiphi33/block/stl/electronic/sg90-4x1.stl

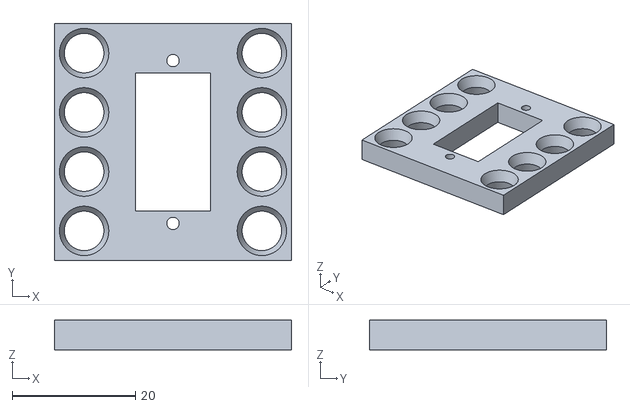
[picture p320: CAD file, 2020-05-04]
stl/electronic/sg90-4x1.stl
38.4 x 38.4 x 4.80
