phiphi33/block/imports/breadboard25.stl

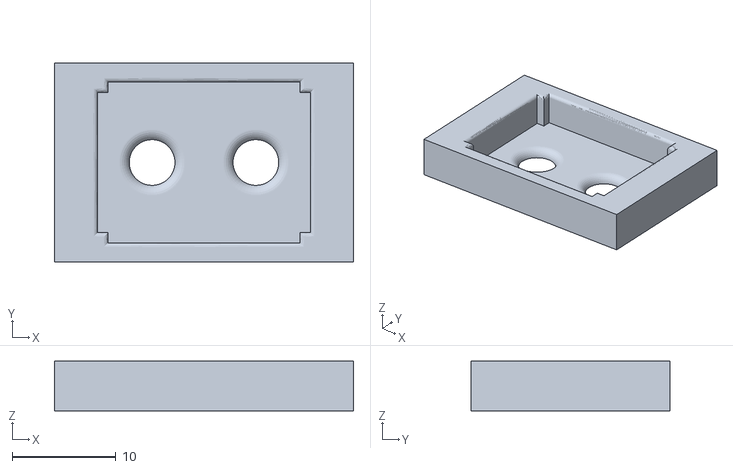
[picture p321: CAD file, 2023-09-15]
imports/breadboard25.stl
28.8 x 19.2 x 4.80
