phiphi33/block/other/12.8/stl_preview.scad

// Only used for preview

filename="./stl/clips/blocker-2.stl";

import(filename);
