phiphi33/block/other/spiralwheel/stl/test-dc-gearbox.png

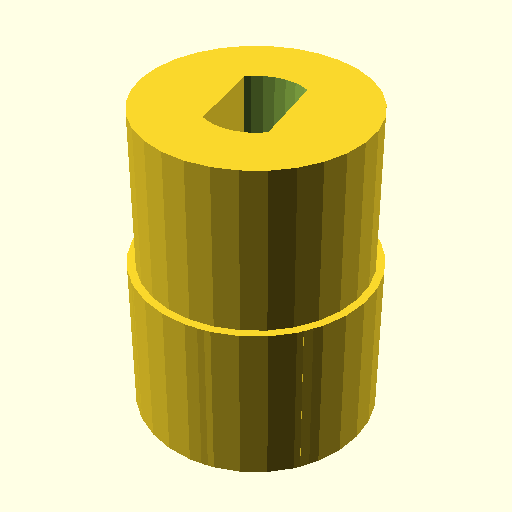
other/spiralwheel/stl/test-dc-gearbox.png
